TitouanMelon/ENIB_Robot_Mobile_Ros2/docs/latex/motor_command_8h_source.tex

\doxysection{motor\+Command.\+h}
\hypertarget{motor_command_8h_source}{}\label{motor_command_8h_source}\index{C:/Users/Administrator/Documents/GitHub/ENIB\_Robot\_Mobile\_Ros2/finalCode/WORKSPACE\_F411\_uROS/base\_robot/Core/Inc/motorCommand.h@{C:/Users/Administrator/Documents/GitHub/ENIB\_Robot\_Mobile\_Ros2/finalCode/WORKSPACE\_F411\_uROS/base\_robot/Core/Inc/motorCommand.h}}

\begin{DoxyCode}{0}
\DoxyCodeLine{\Hypertarget{motor_command_8h_source_l00001}00001\ \textcolor{comment}{/*}}
\DoxyCodeLine{\Hypertarget{motor_command_8h_source_l00002}00002\ \textcolor{comment}{\ *\ MotorCommand.h}}
\DoxyCodeLine{\Hypertarget{motor_command_8h_source_l00003}00003\ \textcolor{comment}{\ */}}
\DoxyCodeLine{\Hypertarget{motor_command_8h_source_l00004}00004\ }
\DoxyCodeLine{\Hypertarget{motor_command_8h_source_l00005}00005\ \textcolor{preprocessor}{\#ifndef\ INC\_MOTORCOMMAND\_H\_}}
\DoxyCodeLine{\Hypertarget{motor_command_8h_source_l00006}00006\ \textcolor{preprocessor}{\#define\ INC\_MOTORCOMMAND\_H\_}}
\DoxyCodeLine{\Hypertarget{motor_command_8h_source_l00007}00007\ }
\DoxyCodeLine{\Hypertarget{motor_command_8h_source_l00008}00008\ \textcolor{preprocessor}{\#include\ "{}\mbox{\hyperlink{main_8h}{main.h}}"{}}}
\DoxyCodeLine{\Hypertarget{motor_command_8h_source_l00009}00009\ }
\DoxyCodeLine{\Hypertarget{motor_command_8h_source_l00010}00010\ }
\DoxyCodeLine{\Hypertarget{motor_command_8h_source_l00011}00011\ \textcolor{keywordtype}{void}\ motorCommand\_Init(\textcolor{keywordtype}{void});}
\DoxyCodeLine{\Hypertarget{motor_command_8h_source_l00012}00012\ \textcolor{keywordtype}{void}\ motorLeft\_SetDuty(\textcolor{keywordtype}{int});}
\DoxyCodeLine{\Hypertarget{motor_command_8h_source_l00013}00013\ \textcolor{keywordtype}{void}\ motorRight\_SetDuty(\textcolor{keywordtype}{int});}
\DoxyCodeLine{\Hypertarget{motor_command_8h_source_l00014}00014\ }
\DoxyCodeLine{\Hypertarget{motor_command_8h_source_l00015}00015\ }
\DoxyCodeLine{\Hypertarget{motor_command_8h_source_l00016}00016\ }
\DoxyCodeLine{\Hypertarget{motor_command_8h_source_l00017}00017\ \textcolor{preprocessor}{\#endif\ }\textcolor{comment}{/*\ INC\_MOTORCOMMAND\_H\_\ */}\textcolor{preprocessor}{}}

\end{DoxyCode}
