TitouanMelon/ENIB_Robot_Mobile_Ros2/docs/latex/stm32f4xx__hal__conf_8h_source.tex

\doxysection{stm32f4xx\+\_\+hal\+\_\+conf.\+h}
\hypertarget{stm32f4xx__hal__conf_8h_source}{}\label{stm32f4xx__hal__conf_8h_source}\index{C:/Users/Administrator/Documents/GitHub/ENIB\_Robot\_Mobile\_Ros2/finalCode/WORKSPACE\_F411\_uROS/base\_robot/Core/Inc/stm32f4xx\_hal\_conf.h@{C:/Users/Administrator/Documents/GitHub/ENIB\_Robot\_Mobile\_Ros2/finalCode/WORKSPACE\_F411\_uROS/base\_robot/Core/Inc/stm32f4xx\_hal\_conf.h}}

\begin{DoxyCode}{0}
\DoxyCodeLine{\Hypertarget{stm32f4xx__hal__conf_8h_source_l00001}00001\ \textcolor{comment}{/*\ USER\ CODE\ BEGIN\ Header\ */}}
\DoxyCodeLine{\Hypertarget{stm32f4xx__hal__conf_8h_source_l00021}00021\ \textcolor{comment}{/*\ USER\ CODE\ END\ Header\ */}}
\DoxyCodeLine{\Hypertarget{stm32f4xx__hal__conf_8h_source_l00022}00022\ }
\DoxyCodeLine{\Hypertarget{stm32f4xx__hal__conf_8h_source_l00023}00023\ \textcolor{comment}{/*\ Define\ to\ prevent\ recursive\ inclusion\ -\/-\/-\/-\/-\/-\/-\/-\/-\/-\/-\/-\/-\/-\/-\/-\/-\/-\/-\/-\/-\/-\/-\/-\/-\/-\/-\/-\/-\/-\/-\/-\/-\/-\/-\/-\/-\/*/}}
\DoxyCodeLine{\Hypertarget{stm32f4xx__hal__conf_8h_source_l00024}00024\ \textcolor{preprocessor}{\#ifndef\ \_\_STM32F4xx\_HAL\_CONF\_H}}
\DoxyCodeLine{\Hypertarget{stm32f4xx__hal__conf_8h_source_l00025}00025\ \textcolor{preprocessor}{\#define\ \_\_STM32F4xx\_HAL\_CONF\_H}}
\DoxyCodeLine{\Hypertarget{stm32f4xx__hal__conf_8h_source_l00026}00026\ }
\DoxyCodeLine{\Hypertarget{stm32f4xx__hal__conf_8h_source_l00027}00027\ \textcolor{preprocessor}{\#ifdef\ \_\_cplusplus}}
\DoxyCodeLine{\Hypertarget{stm32f4xx__hal__conf_8h_source_l00028}00028\ \ \textcolor{keyword}{extern}\ \textcolor{stringliteral}{"{}C"{}}\ \{}
\DoxyCodeLine{\Hypertarget{stm32f4xx__hal__conf_8h_source_l00029}00029\ \textcolor{preprocessor}{\#endif}}
\DoxyCodeLine{\Hypertarget{stm32f4xx__hal__conf_8h_source_l00030}00030\ }
\DoxyCodeLine{\Hypertarget{stm32f4xx__hal__conf_8h_source_l00031}00031\ \textcolor{comment}{/*\ Exported\ types\ -\/-\/-\/-\/-\/-\/-\/-\/-\/-\/-\/-\/-\/-\/-\/-\/-\/-\/-\/-\/-\/-\/-\/-\/-\/-\/-\/-\/-\/-\/-\/-\/-\/-\/-\/-\/-\/-\/-\/-\/-\/-\/-\/-\/-\/-\/-\/-\/-\/-\/-\/-\/-\/-\/-\/-\/-\/-\/-\/-\/*/}}
\DoxyCodeLine{\Hypertarget{stm32f4xx__hal__conf_8h_source_l00032}00032\ \textcolor{comment}{/*\ Exported\ constants\ -\/-\/-\/-\/-\/-\/-\/-\/-\/-\/-\/-\/-\/-\/-\/-\/-\/-\/-\/-\/-\/-\/-\/-\/-\/-\/-\/-\/-\/-\/-\/-\/-\/-\/-\/-\/-\/-\/-\/-\/-\/-\/-\/-\/-\/-\/-\/-\/-\/-\/-\/-\/-\/-\/-\/-\/*/}}
\DoxyCodeLine{\Hypertarget{stm32f4xx__hal__conf_8h_source_l00033}00033\ }
\DoxyCodeLine{\Hypertarget{stm32f4xx__hal__conf_8h_source_l00034}00034\ \textcolor{comment}{/*\ \#\#\#\#\#\#\#\#\#\#\#\#\#\#\#\#\#\#\#\#\#\#\#\#\#\#\ Module\ Selection\ \#\#\#\#\#\#\#\#\#\#\#\#\#\#\#\#\#\#\#\#\#\#\#\#\#\#\#\#\#\#\ */}}
\DoxyCodeLine{\Hypertarget{stm32f4xx__hal__conf_8h_source_l00038}00038\ \textcolor{preprocessor}{\#define\ HAL\_MODULE\_ENABLED}}
\DoxyCodeLine{\Hypertarget{stm32f4xx__hal__conf_8h_source_l00039}00039\ }
\DoxyCodeLine{\Hypertarget{stm32f4xx__hal__conf_8h_source_l00040}00040\ \textcolor{preprocessor}{\ \#define\ HAL\_ADC\_MODULE\_ENABLED}}
\DoxyCodeLine{\Hypertarget{stm32f4xx__hal__conf_8h_source_l00041}00041\ \textcolor{comment}{/*\ \#define\ HAL\_CRYP\_MODULE\_ENABLED\ \ \ */}}
\DoxyCodeLine{\Hypertarget{stm32f4xx__hal__conf_8h_source_l00042}00042\ \textcolor{comment}{/*\ \#define\ HAL\_CAN\_MODULE\_ENABLED\ \ \ */}}
\DoxyCodeLine{\Hypertarget{stm32f4xx__hal__conf_8h_source_l00043}00043\ \textcolor{comment}{/*\ \#define\ HAL\_CRC\_MODULE\_ENABLED\ \ \ */}}
\DoxyCodeLine{\Hypertarget{stm32f4xx__hal__conf_8h_source_l00044}00044\ \textcolor{comment}{/*\ \#define\ HAL\_CAN\_LEGACY\_MODULE\_ENABLED\ \ \ */}}
\DoxyCodeLine{\Hypertarget{stm32f4xx__hal__conf_8h_source_l00045}00045\ \textcolor{comment}{/*\ \#define\ HAL\_CRYP\_MODULE\_ENABLED\ \ \ */}}
\DoxyCodeLine{\Hypertarget{stm32f4xx__hal__conf_8h_source_l00046}00046\ \textcolor{comment}{/*\ \#define\ HAL\_DAC\_MODULE\_ENABLED\ \ \ */}}
\DoxyCodeLine{\Hypertarget{stm32f4xx__hal__conf_8h_source_l00047}00047\ \textcolor{comment}{/*\ \#define\ HAL\_DCMI\_MODULE\_ENABLED\ \ \ */}}
\DoxyCodeLine{\Hypertarget{stm32f4xx__hal__conf_8h_source_l00048}00048\ \textcolor{comment}{/*\ \#define\ HAL\_DMA2D\_MODULE\_ENABLED\ \ \ */}}
\DoxyCodeLine{\Hypertarget{stm32f4xx__hal__conf_8h_source_l00049}00049\ \textcolor{comment}{/*\ \#define\ HAL\_ETH\_MODULE\_ENABLED\ \ \ */}}
\DoxyCodeLine{\Hypertarget{stm32f4xx__hal__conf_8h_source_l00050}00050\ \textcolor{comment}{/*\ \#define\ HAL\_NAND\_MODULE\_ENABLED\ \ \ */}}
\DoxyCodeLine{\Hypertarget{stm32f4xx__hal__conf_8h_source_l00051}00051\ \textcolor{comment}{/*\ \#define\ HAL\_NOR\_MODULE\_ENABLED\ \ \ */}}
\DoxyCodeLine{\Hypertarget{stm32f4xx__hal__conf_8h_source_l00052}00052\ \textcolor{comment}{/*\ \#define\ HAL\_PCCARD\_MODULE\_ENABLED\ \ \ */}}
\DoxyCodeLine{\Hypertarget{stm32f4xx__hal__conf_8h_source_l00053}00053\ \textcolor{comment}{/*\ \#define\ HAL\_SRAM\_MODULE\_ENABLED\ \ \ */}}
\DoxyCodeLine{\Hypertarget{stm32f4xx__hal__conf_8h_source_l00054}00054\ \textcolor{comment}{/*\ \#define\ HAL\_SDRAM\_MODULE\_ENABLED\ \ \ */}}
\DoxyCodeLine{\Hypertarget{stm32f4xx__hal__conf_8h_source_l00055}00055\ \textcolor{comment}{/*\ \#define\ HAL\_HASH\_MODULE\_ENABLED\ \ \ */}}
\DoxyCodeLine{\Hypertarget{stm32f4xx__hal__conf_8h_source_l00056}00056\ \textcolor{preprocessor}{\#define\ HAL\_I2C\_MODULE\_ENABLED}}
\DoxyCodeLine{\Hypertarget{stm32f4xx__hal__conf_8h_source_l00057}00057\ \textcolor{comment}{/*\ \#define\ HAL\_I2S\_MODULE\_ENABLED\ \ \ */}}
\DoxyCodeLine{\Hypertarget{stm32f4xx__hal__conf_8h_source_l00058}00058\ \textcolor{comment}{/*\ \#define\ HAL\_IWDG\_MODULE\_ENABLED\ \ \ */}}
\DoxyCodeLine{\Hypertarget{stm32f4xx__hal__conf_8h_source_l00059}00059\ \textcolor{comment}{/*\ \#define\ HAL\_LTDC\_MODULE\_ENABLED\ \ \ */}}
\DoxyCodeLine{\Hypertarget{stm32f4xx__hal__conf_8h_source_l00060}00060\ \textcolor{comment}{/*\ \#define\ HAL\_RNG\_MODULE\_ENABLED\ \ \ */}}
\DoxyCodeLine{\Hypertarget{stm32f4xx__hal__conf_8h_source_l00061}00061\ \textcolor{comment}{/*\ \#define\ HAL\_RTC\_MODULE\_ENABLED\ \ \ */}}
\DoxyCodeLine{\Hypertarget{stm32f4xx__hal__conf_8h_source_l00062}00062\ \textcolor{comment}{/*\ \#define\ HAL\_SAI\_MODULE\_ENABLED\ \ \ */}}
\DoxyCodeLine{\Hypertarget{stm32f4xx__hal__conf_8h_source_l00063}00063\ \textcolor{comment}{/*\ \#define\ HAL\_SD\_MODULE\_ENABLED\ \ \ */}}
\DoxyCodeLine{\Hypertarget{stm32f4xx__hal__conf_8h_source_l00064}00064\ \textcolor{comment}{/*\ \#define\ HAL\_MMC\_MODULE\_ENABLED\ \ \ */}}
\DoxyCodeLine{\Hypertarget{stm32f4xx__hal__conf_8h_source_l00065}00065\ \textcolor{comment}{/*\ \#define\ HAL\_SPI\_MODULE\_ENABLED\ \ \ */}}
\DoxyCodeLine{\Hypertarget{stm32f4xx__hal__conf_8h_source_l00066}00066\ \textcolor{preprocessor}{\#define\ HAL\_TIM\_MODULE\_ENABLED}}
\DoxyCodeLine{\Hypertarget{stm32f4xx__hal__conf_8h_source_l00067}00067\ \textcolor{preprocessor}{\#define\ HAL\_UART\_MODULE\_ENABLED}}
\DoxyCodeLine{\Hypertarget{stm32f4xx__hal__conf_8h_source_l00068}00068\ \textcolor{comment}{/*\ \#define\ HAL\_USART\_MODULE\_ENABLED\ \ \ */}}
\DoxyCodeLine{\Hypertarget{stm32f4xx__hal__conf_8h_source_l00069}00069\ \textcolor{comment}{/*\ \#define\ HAL\_IRDA\_MODULE\_ENABLED\ \ \ */}}
\DoxyCodeLine{\Hypertarget{stm32f4xx__hal__conf_8h_source_l00070}00070\ \textcolor{comment}{/*\ \#define\ HAL\_SMARTCARD\_MODULE\_ENABLED\ \ \ */}}
\DoxyCodeLine{\Hypertarget{stm32f4xx__hal__conf_8h_source_l00071}00071\ \textcolor{comment}{/*\ \#define\ HAL\_SMBUS\_MODULE\_ENABLED\ \ \ */}}
\DoxyCodeLine{\Hypertarget{stm32f4xx__hal__conf_8h_source_l00072}00072\ \textcolor{comment}{/*\ \#define\ HAL\_WWDG\_MODULE\_ENABLED\ \ \ */}}
\DoxyCodeLine{\Hypertarget{stm32f4xx__hal__conf_8h_source_l00073}00073\ \textcolor{comment}{/*\ \#define\ HAL\_PCD\_MODULE\_ENABLED\ \ \ */}}
\DoxyCodeLine{\Hypertarget{stm32f4xx__hal__conf_8h_source_l00074}00074\ \textcolor{comment}{/*\ \#define\ HAL\_HCD\_MODULE\_ENABLED\ \ \ */}}
\DoxyCodeLine{\Hypertarget{stm32f4xx__hal__conf_8h_source_l00075}00075\ \textcolor{comment}{/*\ \#define\ HAL\_DSI\_MODULE\_ENABLED\ \ \ */}}
\DoxyCodeLine{\Hypertarget{stm32f4xx__hal__conf_8h_source_l00076}00076\ \textcolor{comment}{/*\ \#define\ HAL\_QSPI\_MODULE\_ENABLED\ \ \ */}}
\DoxyCodeLine{\Hypertarget{stm32f4xx__hal__conf_8h_source_l00077}00077\ \textcolor{comment}{/*\ \#define\ HAL\_QSPI\_MODULE\_ENABLED\ \ \ */}}
\DoxyCodeLine{\Hypertarget{stm32f4xx__hal__conf_8h_source_l00078}00078\ \textcolor{comment}{/*\ \#define\ HAL\_CEC\_MODULE\_ENABLED\ \ \ */}}
\DoxyCodeLine{\Hypertarget{stm32f4xx__hal__conf_8h_source_l00079}00079\ \textcolor{comment}{/*\ \#define\ HAL\_FMPI2C\_MODULE\_ENABLED\ \ \ */}}
\DoxyCodeLine{\Hypertarget{stm32f4xx__hal__conf_8h_source_l00080}00080\ \textcolor{comment}{/*\ \#define\ HAL\_FMPSMBUS\_MODULE\_ENABLED\ \ \ */}}
\DoxyCodeLine{\Hypertarget{stm32f4xx__hal__conf_8h_source_l00081}00081\ \textcolor{comment}{/*\ \#define\ HAL\_SPDIFRX\_MODULE\_ENABLED\ \ \ */}}
\DoxyCodeLine{\Hypertarget{stm32f4xx__hal__conf_8h_source_l00082}00082\ \textcolor{comment}{/*\ \#define\ HAL\_DFSDM\_MODULE\_ENABLED\ \ \ */}}
\DoxyCodeLine{\Hypertarget{stm32f4xx__hal__conf_8h_source_l00083}00083\ \textcolor{comment}{/*\ \#define\ HAL\_LPTIM\_MODULE\_ENABLED\ \ \ */}}
\DoxyCodeLine{\Hypertarget{stm32f4xx__hal__conf_8h_source_l00084}00084\ \textcolor{preprocessor}{\#define\ HAL\_GPIO\_MODULE\_ENABLED}}
\DoxyCodeLine{\Hypertarget{stm32f4xx__hal__conf_8h_source_l00085}00085\ \textcolor{preprocessor}{\#define\ HAL\_EXTI\_MODULE\_ENABLED}}
\DoxyCodeLine{\Hypertarget{stm32f4xx__hal__conf_8h_source_l00086}00086\ \textcolor{preprocessor}{\#define\ HAL\_DMA\_MODULE\_ENABLED}}
\DoxyCodeLine{\Hypertarget{stm32f4xx__hal__conf_8h_source_l00087}00087\ \textcolor{preprocessor}{\#define\ HAL\_RCC\_MODULE\_ENABLED}}
\DoxyCodeLine{\Hypertarget{stm32f4xx__hal__conf_8h_source_l00088}00088\ \textcolor{preprocessor}{\#define\ HAL\_FLASH\_MODULE\_ENABLED}}
\DoxyCodeLine{\Hypertarget{stm32f4xx__hal__conf_8h_source_l00089}00089\ \textcolor{preprocessor}{\#define\ HAL\_PWR\_MODULE\_ENABLED}}
\DoxyCodeLine{\Hypertarget{stm32f4xx__hal__conf_8h_source_l00090}00090\ \textcolor{preprocessor}{\#define\ HAL\_CORTEX\_MODULE\_ENABLED}}
\DoxyCodeLine{\Hypertarget{stm32f4xx__hal__conf_8h_source_l00091}00091\ }
\DoxyCodeLine{\Hypertarget{stm32f4xx__hal__conf_8h_source_l00092}00092\ \textcolor{comment}{/*\ \#\#\#\#\#\#\#\#\#\#\#\#\#\#\#\#\#\#\#\#\#\#\#\#\#\#\ HSE/HSI\ Values\ adaptation\ \#\#\#\#\#\#\#\#\#\#\#\#\#\#\#\#\#\#\#\#\#\ */}}
\DoxyCodeLine{\Hypertarget{stm32f4xx__hal__conf_8h_source_l00098}00098\ \textcolor{preprocessor}{\#if\ !defined\ \ (HSE\_VALUE)}}
\DoxyCodeLine{\Hypertarget{stm32f4xx__hal__conf_8h_source_l00099}00099\ \textcolor{preprocessor}{\ \ \#define\ HSE\_VALUE\ \ \ \ 8000000U\ }}
\DoxyCodeLine{\Hypertarget{stm32f4xx__hal__conf_8h_source_l00100}00100\ \textcolor{preprocessor}{\#endif\ }\textcolor{comment}{/*\ HSE\_VALUE\ */}\textcolor{preprocessor}{}}
\DoxyCodeLine{\Hypertarget{stm32f4xx__hal__conf_8h_source_l00101}00101\ }
\DoxyCodeLine{\Hypertarget{stm32f4xx__hal__conf_8h_source_l00102}00102\ \textcolor{preprocessor}{\#if\ !defined\ \ (HSE\_STARTUP\_TIMEOUT)}}
\DoxyCodeLine{\Hypertarget{stm32f4xx__hal__conf_8h_source_l00103}00103\ \textcolor{preprocessor}{\ \ \#define\ HSE\_STARTUP\_TIMEOUT\ \ \ \ 100U\ \ \ }}
\DoxyCodeLine{\Hypertarget{stm32f4xx__hal__conf_8h_source_l00104}00104\ \textcolor{preprocessor}{\#endif\ }\textcolor{comment}{/*\ HSE\_STARTUP\_TIMEOUT\ */}\textcolor{preprocessor}{}}
\DoxyCodeLine{\Hypertarget{stm32f4xx__hal__conf_8h_source_l00105}00105\ }
\DoxyCodeLine{\Hypertarget{stm32f4xx__hal__conf_8h_source_l00111}00111\ \textcolor{preprocessor}{\#if\ !defined\ \ (HSI\_VALUE)}}
\DoxyCodeLine{\Hypertarget{stm32f4xx__hal__conf_8h_source_l00112}00112\ \textcolor{preprocessor}{\ \ \#define\ HSI\_VALUE\ \ \ \ ((uint32\_t)16000000U)\ }}
\DoxyCodeLine{\Hypertarget{stm32f4xx__hal__conf_8h_source_l00113}00113\ \textcolor{preprocessor}{\#endif\ }\textcolor{comment}{/*\ HSI\_VALUE\ */}\textcolor{preprocessor}{}}
\DoxyCodeLine{\Hypertarget{stm32f4xx__hal__conf_8h_source_l00114}00114\ }
\DoxyCodeLine{\Hypertarget{stm32f4xx__hal__conf_8h_source_l00118}00118\ \textcolor{preprocessor}{\#if\ !defined\ \ (LSI\_VALUE)}}
\DoxyCodeLine{\Hypertarget{stm32f4xx__hal__conf_8h_source_l00119}00119\ \textcolor{preprocessor}{\ \#define\ LSI\_VALUE\ \ 32000U\ \ \ \ \ \ \ }}
\DoxyCodeLine{\Hypertarget{stm32f4xx__hal__conf_8h_source_l00120}00120\ \textcolor{preprocessor}{\#endif\ }\textcolor{comment}{/*\ LSI\_VALUE\ */}\textcolor{preprocessor}{\ \ \ \ \ \ \ \ \ \ \ \ \ \ \ \ \ \ \ \ \ \ }}
\DoxyCodeLine{\Hypertarget{stm32f4xx__hal__conf_8h_source_l00126}00126\ \textcolor{preprocessor}{\#if\ !defined\ \ (LSE\_VALUE)}}
\DoxyCodeLine{\Hypertarget{stm32f4xx__hal__conf_8h_source_l00127}00127\ \textcolor{preprocessor}{\ \#define\ LSE\_VALUE\ \ 32768U\ \ \ \ }}
\DoxyCodeLine{\Hypertarget{stm32f4xx__hal__conf_8h_source_l00128}00128\ \textcolor{preprocessor}{\#endif\ }\textcolor{comment}{/*\ LSE\_VALUE\ */}\textcolor{preprocessor}{}}
\DoxyCodeLine{\Hypertarget{stm32f4xx__hal__conf_8h_source_l00129}00129\ }
\DoxyCodeLine{\Hypertarget{stm32f4xx__hal__conf_8h_source_l00130}00130\ \textcolor{preprocessor}{\#if\ !defined\ \ (LSE\_STARTUP\_TIMEOUT)}}
\DoxyCodeLine{\Hypertarget{stm32f4xx__hal__conf_8h_source_l00131}00131\ \textcolor{preprocessor}{\ \ \#define\ LSE\_STARTUP\_TIMEOUT\ \ \ \ 5000U\ \ \ }}
\DoxyCodeLine{\Hypertarget{stm32f4xx__hal__conf_8h_source_l00132}00132\ \textcolor{preprocessor}{\#endif\ }\textcolor{comment}{/*\ LSE\_STARTUP\_TIMEOUT\ */}\textcolor{preprocessor}{}}
\DoxyCodeLine{\Hypertarget{stm32f4xx__hal__conf_8h_source_l00133}00133\ }
\DoxyCodeLine{\Hypertarget{stm32f4xx__hal__conf_8h_source_l00139}00139\ \textcolor{preprocessor}{\#if\ !defined\ \ (EXTERNAL\_CLOCK\_VALUE)}}
\DoxyCodeLine{\Hypertarget{stm32f4xx__hal__conf_8h_source_l00140}00140\ \textcolor{preprocessor}{\ \ \#define\ EXTERNAL\_CLOCK\_VALUE\ \ \ \ 12288000U\ }}
\DoxyCodeLine{\Hypertarget{stm32f4xx__hal__conf_8h_source_l00141}00141\ \textcolor{preprocessor}{\#endif\ }\textcolor{comment}{/*\ EXTERNAL\_CLOCK\_VALUE\ */}\textcolor{preprocessor}{}}
\DoxyCodeLine{\Hypertarget{stm32f4xx__hal__conf_8h_source_l00142}00142\ }
\DoxyCodeLine{\Hypertarget{stm32f4xx__hal__conf_8h_source_l00143}00143\ \textcolor{comment}{/*\ Tip:\ To\ avoid\ modifying\ this\ file\ each\ time\ you\ need\ to\ use\ different\ HSE,}}
\DoxyCodeLine{\Hypertarget{stm32f4xx__hal__conf_8h_source_l00144}00144\ \textcolor{comment}{\ \ \ ===\ \ you\ can\ define\ the\ HSE\ value\ in\ your\ toolchain\ compiler\ preprocessor.\ */}}
\DoxyCodeLine{\Hypertarget{stm32f4xx__hal__conf_8h_source_l00145}00145\ }
\DoxyCodeLine{\Hypertarget{stm32f4xx__hal__conf_8h_source_l00146}00146\ \textcolor{comment}{/*\ \#\#\#\#\#\#\#\#\#\#\#\#\#\#\#\#\#\#\#\#\#\#\#\#\#\#\#\ System\ Configuration\ \#\#\#\#\#\#\#\#\#\#\#\#\#\#\#\#\#\#\#\#\#\#\#\#\#\ */}}
\DoxyCodeLine{\Hypertarget{stm32f4xx__hal__conf_8h_source_l00150}00150\ \textcolor{preprocessor}{\#define\ \ VDD\_VALUE\ \ \ \ \ \ \ \ \ \ \ \ 3300U\ }}
\DoxyCodeLine{\Hypertarget{stm32f4xx__hal__conf_8h_source_l00151}00151\ \textcolor{preprocessor}{\#define\ \ TICK\_INT\_PRIORITY\ \ \ \ \ \ \ \ \ \ \ \ 15U\ \ \ }}
\DoxyCodeLine{\Hypertarget{stm32f4xx__hal__conf_8h_source_l00152}00152\ \textcolor{preprocessor}{\#define\ \ USE\_RTOS\ \ \ \ \ \ \ \ \ \ \ \ \ \ \ \ \ \ \ \ \ 0U}}
\DoxyCodeLine{\Hypertarget{stm32f4xx__hal__conf_8h_source_l00153}00153\ \textcolor{preprocessor}{\#define\ \ PREFETCH\_ENABLE\ \ \ \ \ \ \ \ \ \ \ \ \ \ 1U}}
\DoxyCodeLine{\Hypertarget{stm32f4xx__hal__conf_8h_source_l00154}00154\ \textcolor{preprocessor}{\#define\ \ INSTRUCTION\_CACHE\_ENABLE\ \ \ \ \ 1U}}
\DoxyCodeLine{\Hypertarget{stm32f4xx__hal__conf_8h_source_l00155}00155\ \textcolor{preprocessor}{\#define\ \ DATA\_CACHE\_ENABLE\ \ \ \ \ \ \ \ \ \ \ \ 1U}}
\DoxyCodeLine{\Hypertarget{stm32f4xx__hal__conf_8h_source_l00156}00156\ }
\DoxyCodeLine{\Hypertarget{stm32f4xx__hal__conf_8h_source_l00157}00157\ \textcolor{preprocessor}{\#define\ \ USE\_HAL\_ADC\_REGISTER\_CALLBACKS\ \ \ \ \ \ \ \ \ 0U\ }\textcolor{comment}{/*\ ADC\ register\ callback\ disabled\ \ \ \ \ \ \ */}\textcolor{preprocessor}{}}
\DoxyCodeLine{\Hypertarget{stm32f4xx__hal__conf_8h_source_l00158}00158\ \textcolor{preprocessor}{\#define\ \ USE\_HAL\_CAN\_REGISTER\_CALLBACKS\ \ \ \ \ \ \ \ \ 0U\ }\textcolor{comment}{/*\ CAN\ register\ callback\ disabled\ \ \ \ \ \ \ */}\textcolor{preprocessor}{}}
\DoxyCodeLine{\Hypertarget{stm32f4xx__hal__conf_8h_source_l00159}00159\ \textcolor{preprocessor}{\#define\ \ USE\_HAL\_CEC\_REGISTER\_CALLBACKS\ \ \ \ \ \ \ \ \ 0U\ }\textcolor{comment}{/*\ CEC\ register\ callback\ disabled\ \ \ \ \ \ \ */}\textcolor{preprocessor}{}}
\DoxyCodeLine{\Hypertarget{stm32f4xx__hal__conf_8h_source_l00160}00160\ \textcolor{preprocessor}{\#define\ \ USE\_HAL\_CRYP\_REGISTER\_CALLBACKS\ \ \ \ \ \ \ \ 0U\ }\textcolor{comment}{/*\ CRYP\ register\ callback\ disabled\ \ \ \ \ \ */}\textcolor{preprocessor}{}}
\DoxyCodeLine{\Hypertarget{stm32f4xx__hal__conf_8h_source_l00161}00161\ \textcolor{preprocessor}{\#define\ \ USE\_HAL\_DAC\_REGISTER\_CALLBACKS\ \ \ \ \ \ \ \ \ 0U\ }\textcolor{comment}{/*\ DAC\ register\ callback\ disabled\ \ \ \ \ \ \ */}\textcolor{preprocessor}{}}
\DoxyCodeLine{\Hypertarget{stm32f4xx__hal__conf_8h_source_l00162}00162\ \textcolor{preprocessor}{\#define\ \ USE\_HAL\_DCMI\_REGISTER\_CALLBACKS\ \ \ \ \ \ \ \ 0U\ }\textcolor{comment}{/*\ DCMI\ register\ callback\ disabled\ \ \ \ \ \ */}\textcolor{preprocessor}{}}
\DoxyCodeLine{\Hypertarget{stm32f4xx__hal__conf_8h_source_l00163}00163\ \textcolor{preprocessor}{\#define\ \ USE\_HAL\_DFSDM\_REGISTER\_CALLBACKS\ \ \ \ \ \ \ 0U\ }\textcolor{comment}{/*\ DFSDM\ register\ callback\ disabled\ \ \ \ \ */}\textcolor{preprocessor}{}}
\DoxyCodeLine{\Hypertarget{stm32f4xx__hal__conf_8h_source_l00164}00164\ \textcolor{preprocessor}{\#define\ \ USE\_HAL\_DMA2D\_REGISTER\_CALLBACKS\ \ \ \ \ \ \ 0U\ }\textcolor{comment}{/*\ DMA2D\ register\ callback\ disabled\ \ \ \ \ */}\textcolor{preprocessor}{}}
\DoxyCodeLine{\Hypertarget{stm32f4xx__hal__conf_8h_source_l00165}00165\ \textcolor{preprocessor}{\#define\ \ USE\_HAL\_DSI\_REGISTER\_CALLBACKS\ \ \ \ \ \ \ \ \ 0U\ }\textcolor{comment}{/*\ DSI\ register\ callback\ disabled\ \ \ \ \ \ \ */}\textcolor{preprocessor}{}}
\DoxyCodeLine{\Hypertarget{stm32f4xx__hal__conf_8h_source_l00166}00166\ \textcolor{preprocessor}{\#define\ \ USE\_HAL\_ETH\_REGISTER\_CALLBACKS\ \ \ \ \ \ \ \ \ 0U\ }\textcolor{comment}{/*\ ETH\ register\ callback\ disabled\ \ \ \ \ \ \ */}\textcolor{preprocessor}{}}
\DoxyCodeLine{\Hypertarget{stm32f4xx__hal__conf_8h_source_l00167}00167\ \textcolor{preprocessor}{\#define\ \ USE\_HAL\_HASH\_REGISTER\_CALLBACKS\ \ \ \ \ \ \ \ 0U\ }\textcolor{comment}{/*\ HASH\ register\ callback\ disabled\ \ \ \ \ \ */}\textcolor{preprocessor}{}}
\DoxyCodeLine{\Hypertarget{stm32f4xx__hal__conf_8h_source_l00168}00168\ \textcolor{preprocessor}{\#define\ \ USE\_HAL\_HCD\_REGISTER\_CALLBACKS\ \ \ \ \ \ \ \ \ 0U\ }\textcolor{comment}{/*\ HCD\ register\ callback\ disabled\ \ \ \ \ \ \ */}\textcolor{preprocessor}{}}
\DoxyCodeLine{\Hypertarget{stm32f4xx__hal__conf_8h_source_l00169}00169\ \textcolor{preprocessor}{\#define\ \ USE\_HAL\_I2C\_REGISTER\_CALLBACKS\ \ \ \ \ \ \ \ \ 0U\ }\textcolor{comment}{/*\ I2C\ register\ callback\ disabled\ \ \ \ \ \ \ */}\textcolor{preprocessor}{}}
\DoxyCodeLine{\Hypertarget{stm32f4xx__hal__conf_8h_source_l00170}00170\ \textcolor{preprocessor}{\#define\ \ USE\_HAL\_FMPI2C\_REGISTER\_CALLBACKS\ \ \ \ \ \ 0U\ }\textcolor{comment}{/*\ FMPI2C\ register\ callback\ disabled\ \ \ \ */}\textcolor{preprocessor}{}}
\DoxyCodeLine{\Hypertarget{stm32f4xx__hal__conf_8h_source_l00171}00171\ \textcolor{preprocessor}{\#define\ \ USE\_HAL\_FMPSMBUS\_REGISTER\_CALLBACKS\ \ \ \ 0U\ }\textcolor{comment}{/*\ FMPSMBUS\ register\ callback\ disabled\ \ */}\textcolor{preprocessor}{}}
\DoxyCodeLine{\Hypertarget{stm32f4xx__hal__conf_8h_source_l00172}00172\ \textcolor{preprocessor}{\#define\ \ USE\_HAL\_I2S\_REGISTER\_CALLBACKS\ \ \ \ \ \ \ \ \ 0U\ }\textcolor{comment}{/*\ I2S\ register\ callback\ disabled\ \ \ \ \ \ \ */}\textcolor{preprocessor}{}}
\DoxyCodeLine{\Hypertarget{stm32f4xx__hal__conf_8h_source_l00173}00173\ \textcolor{preprocessor}{\#define\ \ USE\_HAL\_IRDA\_REGISTER\_CALLBACKS\ \ \ \ \ \ \ \ 0U\ }\textcolor{comment}{/*\ IRDA\ register\ callback\ disabled\ \ \ \ \ \ */}\textcolor{preprocessor}{}}
\DoxyCodeLine{\Hypertarget{stm32f4xx__hal__conf_8h_source_l00174}00174\ \textcolor{preprocessor}{\#define\ \ USE\_HAL\_LPTIM\_REGISTER\_CALLBACKS\ \ \ \ \ \ \ 0U\ }\textcolor{comment}{/*\ LPTIM\ register\ callback\ disabled\ \ \ \ \ */}\textcolor{preprocessor}{}}
\DoxyCodeLine{\Hypertarget{stm32f4xx__hal__conf_8h_source_l00175}00175\ \textcolor{preprocessor}{\#define\ \ USE\_HAL\_LTDC\_REGISTER\_CALLBACKS\ \ \ \ \ \ \ \ 0U\ }\textcolor{comment}{/*\ LTDC\ register\ callback\ disabled\ \ \ \ \ \ */}\textcolor{preprocessor}{}}
\DoxyCodeLine{\Hypertarget{stm32f4xx__hal__conf_8h_source_l00176}00176\ \textcolor{preprocessor}{\#define\ \ USE\_HAL\_MMC\_REGISTER\_CALLBACKS\ \ \ \ \ \ \ \ \ 0U\ }\textcolor{comment}{/*\ MMC\ register\ callback\ disabled\ \ \ \ \ \ \ */}\textcolor{preprocessor}{}}
\DoxyCodeLine{\Hypertarget{stm32f4xx__hal__conf_8h_source_l00177}00177\ \textcolor{preprocessor}{\#define\ \ USE\_HAL\_NAND\_REGISTER\_CALLBACKS\ \ \ \ \ \ \ \ 0U\ }\textcolor{comment}{/*\ NAND\ register\ callback\ disabled\ \ \ \ \ \ */}\textcolor{preprocessor}{}}
\DoxyCodeLine{\Hypertarget{stm32f4xx__hal__conf_8h_source_l00178}00178\ \textcolor{preprocessor}{\#define\ \ USE\_HAL\_NOR\_REGISTER\_CALLBACKS\ \ \ \ \ \ \ \ \ 0U\ }\textcolor{comment}{/*\ NOR\ register\ callback\ disabled\ \ \ \ \ \ \ */}\textcolor{preprocessor}{}}
\DoxyCodeLine{\Hypertarget{stm32f4xx__hal__conf_8h_source_l00179}00179\ \textcolor{preprocessor}{\#define\ \ USE\_HAL\_PCCARD\_REGISTER\_CALLBACKS\ \ \ \ \ \ 0U\ }\textcolor{comment}{/*\ PCCARD\ register\ callback\ disabled\ \ \ \ */}\textcolor{preprocessor}{}}
\DoxyCodeLine{\Hypertarget{stm32f4xx__hal__conf_8h_source_l00180}00180\ \textcolor{preprocessor}{\#define\ \ USE\_HAL\_PCD\_REGISTER\_CALLBACKS\ \ \ \ \ \ \ \ \ 0U\ }\textcolor{comment}{/*\ PCD\ register\ callback\ disabled\ \ \ \ \ \ \ */}\textcolor{preprocessor}{}}
\DoxyCodeLine{\Hypertarget{stm32f4xx__hal__conf_8h_source_l00181}00181\ \textcolor{preprocessor}{\#define\ \ USE\_HAL\_QSPI\_REGISTER\_CALLBACKS\ \ \ \ \ \ \ \ 0U\ }\textcolor{comment}{/*\ QSPI\ register\ callback\ disabled\ \ \ \ \ \ */}\textcolor{preprocessor}{}}
\DoxyCodeLine{\Hypertarget{stm32f4xx__hal__conf_8h_source_l00182}00182\ \textcolor{preprocessor}{\#define\ \ USE\_HAL\_RNG\_REGISTER\_CALLBACKS\ \ \ \ \ \ \ \ \ 0U\ }\textcolor{comment}{/*\ RNG\ register\ callback\ disabled\ \ \ \ \ \ \ */}\textcolor{preprocessor}{}}
\DoxyCodeLine{\Hypertarget{stm32f4xx__hal__conf_8h_source_l00183}00183\ \textcolor{preprocessor}{\#define\ \ USE\_HAL\_RTC\_REGISTER\_CALLBACKS\ \ \ \ \ \ \ \ \ 0U\ }\textcolor{comment}{/*\ RTC\ register\ callback\ disabled\ \ \ \ \ \ \ */}\textcolor{preprocessor}{}}
\DoxyCodeLine{\Hypertarget{stm32f4xx__hal__conf_8h_source_l00184}00184\ \textcolor{preprocessor}{\#define\ \ USE\_HAL\_SAI\_REGISTER\_CALLBACKS\ \ \ \ \ \ \ \ \ 0U\ }\textcolor{comment}{/*\ SAI\ register\ callback\ disabled\ \ \ \ \ \ \ */}\textcolor{preprocessor}{}}
\DoxyCodeLine{\Hypertarget{stm32f4xx__hal__conf_8h_source_l00185}00185\ \textcolor{preprocessor}{\#define\ \ USE\_HAL\_SD\_REGISTER\_CALLBACKS\ \ \ \ \ \ \ \ \ \ 0U\ }\textcolor{comment}{/*\ SD\ register\ callback\ disabled\ \ \ \ \ \ \ \ */}\textcolor{preprocessor}{}}
\DoxyCodeLine{\Hypertarget{stm32f4xx__hal__conf_8h_source_l00186}00186\ \textcolor{preprocessor}{\#define\ \ USE\_HAL\_SMARTCARD\_REGISTER\_CALLBACKS\ \ \ 0U\ }\textcolor{comment}{/*\ SMARTCARD\ register\ callback\ disabled\ */}\textcolor{preprocessor}{}}
\DoxyCodeLine{\Hypertarget{stm32f4xx__hal__conf_8h_source_l00187}00187\ \textcolor{preprocessor}{\#define\ \ USE\_HAL\_SDRAM\_REGISTER\_CALLBACKS\ \ \ \ \ \ \ 0U\ }\textcolor{comment}{/*\ SDRAM\ register\ callback\ disabled\ \ \ \ \ */}\textcolor{preprocessor}{}}
\DoxyCodeLine{\Hypertarget{stm32f4xx__hal__conf_8h_source_l00188}00188\ \textcolor{preprocessor}{\#define\ \ USE\_HAL\_SRAM\_REGISTER\_CALLBACKS\ \ \ \ \ \ \ \ 0U\ }\textcolor{comment}{/*\ SRAM\ register\ callback\ disabled\ \ \ \ \ \ */}\textcolor{preprocessor}{}}
\DoxyCodeLine{\Hypertarget{stm32f4xx__hal__conf_8h_source_l00189}00189\ \textcolor{preprocessor}{\#define\ \ USE\_HAL\_SPDIFRX\_REGISTER\_CALLBACKS\ \ \ \ \ 0U\ }\textcolor{comment}{/*\ SPDIFRX\ register\ callback\ disabled\ \ \ */}\textcolor{preprocessor}{}}
\DoxyCodeLine{\Hypertarget{stm32f4xx__hal__conf_8h_source_l00190}00190\ \textcolor{preprocessor}{\#define\ \ USE\_HAL\_SMBUS\_REGISTER\_CALLBACKS\ \ \ \ \ \ \ 0U\ }\textcolor{comment}{/*\ SMBUS\ register\ callback\ disabled\ \ \ \ \ */}\textcolor{preprocessor}{}}
\DoxyCodeLine{\Hypertarget{stm32f4xx__hal__conf_8h_source_l00191}00191\ \textcolor{preprocessor}{\#define\ \ USE\_HAL\_SPI\_REGISTER\_CALLBACKS\ \ \ \ \ \ \ \ \ 0U\ }\textcolor{comment}{/*\ SPI\ register\ callback\ disabled\ \ \ \ \ \ \ */}\textcolor{preprocessor}{}}
\DoxyCodeLine{\Hypertarget{stm32f4xx__hal__conf_8h_source_l00192}00192\ \textcolor{preprocessor}{\#define\ \ USE\_HAL\_TIM\_REGISTER\_CALLBACKS\ \ \ \ \ \ \ \ \ 0U\ }\textcolor{comment}{/*\ TIM\ register\ callback\ disabled\ \ \ \ \ \ \ */}\textcolor{preprocessor}{}}
\DoxyCodeLine{\Hypertarget{stm32f4xx__hal__conf_8h_source_l00193}00193\ \textcolor{preprocessor}{\#define\ \ USE\_HAL\_UART\_REGISTER\_CALLBACKS\ \ \ \ \ \ \ \ 0U\ }\textcolor{comment}{/*\ UART\ register\ callback\ disabled\ \ \ \ \ \ */}\textcolor{preprocessor}{}}
\DoxyCodeLine{\Hypertarget{stm32f4xx__hal__conf_8h_source_l00194}00194\ \textcolor{preprocessor}{\#define\ \ USE\_HAL\_USART\_REGISTER\_CALLBACKS\ \ \ \ \ \ \ 0U\ }\textcolor{comment}{/*\ USART\ register\ callback\ disabled\ \ \ \ \ */}\textcolor{preprocessor}{}}
\DoxyCodeLine{\Hypertarget{stm32f4xx__hal__conf_8h_source_l00195}00195\ \textcolor{preprocessor}{\#define\ \ USE\_HAL\_WWDG\_REGISTER\_CALLBACKS\ \ \ \ \ \ \ \ 0U\ }\textcolor{comment}{/*\ WWDG\ register\ callback\ disabled\ \ \ \ \ \ */}\textcolor{preprocessor}{}}
\DoxyCodeLine{\Hypertarget{stm32f4xx__hal__conf_8h_source_l00196}00196\ }
\DoxyCodeLine{\Hypertarget{stm32f4xx__hal__conf_8h_source_l00197}00197\ \textcolor{comment}{/*\ \#\#\#\#\#\#\#\#\#\#\#\#\#\#\#\#\#\#\#\#\#\#\#\#\#\#\ Assert\ Selection\ \#\#\#\#\#\#\#\#\#\#\#\#\#\#\#\#\#\#\#\#\#\#\#\#\#\#\#\#\#\#\ */}}
\DoxyCodeLine{\Hypertarget{stm32f4xx__hal__conf_8h_source_l00202}00202\ \textcolor{comment}{/*\ \#define\ USE\_FULL\_ASSERT\ \ \ \ 1U\ */}}
\DoxyCodeLine{\Hypertarget{stm32f4xx__hal__conf_8h_source_l00203}00203\ }
\DoxyCodeLine{\Hypertarget{stm32f4xx__hal__conf_8h_source_l00204}00204\ \textcolor{comment}{/*\ \#\#\#\#\#\#\#\#\#\#\#\#\#\#\#\#\#\#\ Ethernet\ peripheral\ configuration\ \#\#\#\#\#\#\#\#\#\#\#\#\#\#\#\#\#\#\#\#\#\ */}}
\DoxyCodeLine{\Hypertarget{stm32f4xx__hal__conf_8h_source_l00205}00205\ }
\DoxyCodeLine{\Hypertarget{stm32f4xx__hal__conf_8h_source_l00206}00206\ \textcolor{comment}{/*\ Section\ 1\ :\ Ethernet\ peripheral\ configuration\ */}}
\DoxyCodeLine{\Hypertarget{stm32f4xx__hal__conf_8h_source_l00207}00207\ }
\DoxyCodeLine{\Hypertarget{stm32f4xx__hal__conf_8h_source_l00208}00208\ \textcolor{comment}{/*\ MAC\ ADDRESS:\ MAC\_ADDR0:MAC\_ADDR1:MAC\_ADDR2:MAC\_ADDR3:MAC\_ADDR4:MAC\_ADDR5\ */}}
\DoxyCodeLine{\Hypertarget{stm32f4xx__hal__conf_8h_source_l00209}00209\ \textcolor{preprocessor}{\#define\ MAC\_ADDR0\ \ \ 2U}}
\DoxyCodeLine{\Hypertarget{stm32f4xx__hal__conf_8h_source_l00210}00210\ \textcolor{preprocessor}{\#define\ MAC\_ADDR1\ \ \ 0U}}
\DoxyCodeLine{\Hypertarget{stm32f4xx__hal__conf_8h_source_l00211}00211\ \textcolor{preprocessor}{\#define\ MAC\_ADDR2\ \ \ 0U}}
\DoxyCodeLine{\Hypertarget{stm32f4xx__hal__conf_8h_source_l00212}00212\ \textcolor{preprocessor}{\#define\ MAC\_ADDR3\ \ \ 0U}}
\DoxyCodeLine{\Hypertarget{stm32f4xx__hal__conf_8h_source_l00213}00213\ \textcolor{preprocessor}{\#define\ MAC\_ADDR4\ \ \ 0U}}
\DoxyCodeLine{\Hypertarget{stm32f4xx__hal__conf_8h_source_l00214}00214\ \textcolor{preprocessor}{\#define\ MAC\_ADDR5\ \ \ 0U}}
\DoxyCodeLine{\Hypertarget{stm32f4xx__hal__conf_8h_source_l00215}00215\ }
\DoxyCodeLine{\Hypertarget{stm32f4xx__hal__conf_8h_source_l00216}00216\ \textcolor{comment}{/*\ Definition\ of\ the\ Ethernet\ driver\ buffers\ size\ and\ count\ */}}
\DoxyCodeLine{\Hypertarget{stm32f4xx__hal__conf_8h_source_l00217}00217\ \textcolor{preprocessor}{\#define\ ETH\_RX\_BUF\_SIZE\ \ \ \ \ \ \ \ \ \ \ \ \ \ \ \ ETH\_MAX\_PACKET\_SIZE\ }\textcolor{comment}{/*\ buffer\ size\ for\ receive\ \ \ \ \ \ \ \ \ \ \ \ \ \ \ */}\textcolor{preprocessor}{}}
\DoxyCodeLine{\Hypertarget{stm32f4xx__hal__conf_8h_source_l00218}00218\ \textcolor{preprocessor}{\#define\ ETH\_TX\_BUF\_SIZE\ \ \ \ \ \ \ \ \ \ \ \ \ \ \ \ ETH\_MAX\_PACKET\_SIZE\ }\textcolor{comment}{/*\ buffer\ size\ for\ transmit\ \ \ \ \ \ \ \ \ \ \ \ \ \ */}\textcolor{preprocessor}{}}
\DoxyCodeLine{\Hypertarget{stm32f4xx__hal__conf_8h_source_l00219}00219\ \textcolor{preprocessor}{\#define\ ETH\_RXBUFNB\ \ \ \ \ \ \ \ \ \ \ \ \ \ \ \ \ \ \ \ 4U\ \ \ \ \ \ \ }\textcolor{comment}{/*\ 4\ Rx\ buffers\ of\ size\ ETH\_RX\_BUF\_SIZE\ \ */}\textcolor{preprocessor}{}}
\DoxyCodeLine{\Hypertarget{stm32f4xx__hal__conf_8h_source_l00220}00220\ \textcolor{preprocessor}{\#define\ ETH\_TXBUFNB\ \ \ \ \ \ \ \ \ \ \ \ \ \ \ \ \ \ \ \ 4U\ \ \ \ \ \ \ }\textcolor{comment}{/*\ 4\ Tx\ buffers\ of\ size\ ETH\_TX\_BUF\_SIZE\ \ */}\textcolor{preprocessor}{}}
\DoxyCodeLine{\Hypertarget{stm32f4xx__hal__conf_8h_source_l00221}00221\ }
\DoxyCodeLine{\Hypertarget{stm32f4xx__hal__conf_8h_source_l00222}00222\ \textcolor{comment}{/*\ Section\ 2:\ PHY\ configuration\ section\ */}}
\DoxyCodeLine{\Hypertarget{stm32f4xx__hal__conf_8h_source_l00223}00223\ }
\DoxyCodeLine{\Hypertarget{stm32f4xx__hal__conf_8h_source_l00224}00224\ \textcolor{comment}{/*\ DP83848\_PHY\_ADDRESS\ Address*/}}
\DoxyCodeLine{\Hypertarget{stm32f4xx__hal__conf_8h_source_l00225}00225\ \textcolor{preprocessor}{\#define\ DP83848\_PHY\_ADDRESS\ \ \ \ \ \ \ \ \ \ \ 0x01U}}
\DoxyCodeLine{\Hypertarget{stm32f4xx__hal__conf_8h_source_l00226}00226\ \textcolor{comment}{/*\ PHY\ Reset\ delay\ these\ values\ are\ based\ on\ a\ 1\ ms\ Systick\ interrupt*/}}
\DoxyCodeLine{\Hypertarget{stm32f4xx__hal__conf_8h_source_l00227}00227\ \textcolor{preprocessor}{\#define\ PHY\_RESET\_DELAY\ \ \ \ \ \ \ \ \ \ \ \ \ \ \ \ \ 0x000000FFU}}
\DoxyCodeLine{\Hypertarget{stm32f4xx__hal__conf_8h_source_l00228}00228\ \textcolor{comment}{/*\ PHY\ Configuration\ delay\ */}}
\DoxyCodeLine{\Hypertarget{stm32f4xx__hal__conf_8h_source_l00229}00229\ \textcolor{preprocessor}{\#define\ PHY\_CONFIG\_DELAY\ \ \ \ \ \ \ \ \ \ \ \ \ \ \ \ 0x00000FFFU}}
\DoxyCodeLine{\Hypertarget{stm32f4xx__hal__conf_8h_source_l00230}00230\ }
\DoxyCodeLine{\Hypertarget{stm32f4xx__hal__conf_8h_source_l00231}00231\ \textcolor{preprocessor}{\#define\ PHY\_READ\_TO\ \ \ \ \ \ \ \ \ \ \ \ \ \ \ \ \ \ \ \ \ 0x0000FFFFU}}
\DoxyCodeLine{\Hypertarget{stm32f4xx__hal__conf_8h_source_l00232}00232\ \textcolor{preprocessor}{\#define\ PHY\_WRITE\_TO\ \ \ \ \ \ \ \ \ \ \ \ \ \ \ \ \ \ \ \ 0x0000FFFFU}}
\DoxyCodeLine{\Hypertarget{stm32f4xx__hal__conf_8h_source_l00233}00233\ }
\DoxyCodeLine{\Hypertarget{stm32f4xx__hal__conf_8h_source_l00234}00234\ \textcolor{comment}{/*\ Section\ 3:\ Common\ PHY\ Registers\ */}}
\DoxyCodeLine{\Hypertarget{stm32f4xx__hal__conf_8h_source_l00235}00235\ }
\DoxyCodeLine{\Hypertarget{stm32f4xx__hal__conf_8h_source_l00236}00236\ \textcolor{preprocessor}{\#define\ PHY\_BCR\ \ \ \ \ \ \ \ \ \ \ \ \ \ \ \ \ \ \ \ \ \ \ \ \ ((uint16\_t)0x0000U)\ \ \ \ }}
\DoxyCodeLine{\Hypertarget{stm32f4xx__hal__conf_8h_source_l00237}00237\ \textcolor{preprocessor}{\#define\ PHY\_BSR\ \ \ \ \ \ \ \ \ \ \ \ \ \ \ \ \ \ \ \ \ \ \ \ \ ((uint16\_t)0x0001U)\ \ \ \ }}
\DoxyCodeLine{\Hypertarget{stm32f4xx__hal__conf_8h_source_l00239}00239\ \textcolor{preprocessor}{\#define\ PHY\_RESET\ \ \ \ \ \ \ \ \ \ \ \ \ \ \ \ \ \ \ \ \ \ \ ((uint16\_t)0x8000U)\ \ }}
\DoxyCodeLine{\Hypertarget{stm32f4xx__hal__conf_8h_source_l00240}00240\ \textcolor{preprocessor}{\#define\ PHY\_LOOPBACK\ \ \ \ \ \ \ \ \ \ \ \ \ \ \ \ \ \ \ \ ((uint16\_t)0x4000U)\ \ }}
\DoxyCodeLine{\Hypertarget{stm32f4xx__hal__conf_8h_source_l00241}00241\ \textcolor{preprocessor}{\#define\ PHY\_FULLDUPLEX\_100M\ \ \ \ \ \ \ \ \ \ \ \ \ ((uint16\_t)0x2100U)\ \ }}
\DoxyCodeLine{\Hypertarget{stm32f4xx__hal__conf_8h_source_l00242}00242\ \textcolor{preprocessor}{\#define\ PHY\_HALFDUPLEX\_100M\ \ \ \ \ \ \ \ \ \ \ \ \ ((uint16\_t)0x2000U)\ \ }}
\DoxyCodeLine{\Hypertarget{stm32f4xx__hal__conf_8h_source_l00243}00243\ \textcolor{preprocessor}{\#define\ PHY\_FULLDUPLEX\_10M\ \ \ \ \ \ \ \ \ \ \ \ \ \ ((uint16\_t)0x0100U)\ \ }}
\DoxyCodeLine{\Hypertarget{stm32f4xx__hal__conf_8h_source_l00244}00244\ \textcolor{preprocessor}{\#define\ PHY\_HALFDUPLEX\_10M\ \ \ \ \ \ \ \ \ \ \ \ \ \ ((uint16\_t)0x0000U)\ \ }}
\DoxyCodeLine{\Hypertarget{stm32f4xx__hal__conf_8h_source_l00245}00245\ \textcolor{preprocessor}{\#define\ PHY\_AUTONEGOTIATION\ \ \ \ \ \ \ \ \ \ \ \ \ ((uint16\_t)0x1000U)\ \ }}
\DoxyCodeLine{\Hypertarget{stm32f4xx__hal__conf_8h_source_l00246}00246\ \textcolor{preprocessor}{\#define\ PHY\_RESTART\_AUTONEGOTIATION\ \ \ \ \ ((uint16\_t)0x0200U)\ \ }}
\DoxyCodeLine{\Hypertarget{stm32f4xx__hal__conf_8h_source_l00247}00247\ \textcolor{preprocessor}{\#define\ PHY\_POWERDOWN\ \ \ \ \ \ \ \ \ \ \ \ \ \ \ \ \ \ \ ((uint16\_t)0x0800U)\ \ }}
\DoxyCodeLine{\Hypertarget{stm32f4xx__hal__conf_8h_source_l00248}00248\ \textcolor{preprocessor}{\#define\ PHY\_ISOLATE\ \ \ \ \ \ \ \ \ \ \ \ \ \ \ \ \ \ \ \ \ ((uint16\_t)0x0400U)\ \ }}
\DoxyCodeLine{\Hypertarget{stm32f4xx__hal__conf_8h_source_l00250}00250\ \textcolor{preprocessor}{\#define\ PHY\_AUTONEGO\_COMPLETE\ \ \ \ \ \ \ \ \ \ \ ((uint16\_t)0x0020U)\ \ }}
\DoxyCodeLine{\Hypertarget{stm32f4xx__hal__conf_8h_source_l00251}00251\ \textcolor{preprocessor}{\#define\ PHY\_LINKED\_STATUS\ \ \ \ \ \ \ \ \ \ \ \ \ \ \ ((uint16\_t)0x0004U)\ \ }}
\DoxyCodeLine{\Hypertarget{stm32f4xx__hal__conf_8h_source_l00252}00252\ \textcolor{preprocessor}{\#define\ PHY\_JABBER\_DETECTION\ \ \ \ \ \ \ \ \ \ \ \ ((uint16\_t)0x0002U)\ \ }}
\DoxyCodeLine{\Hypertarget{stm32f4xx__hal__conf_8h_source_l00254}00254\ \textcolor{comment}{/*\ Section\ 4:\ Extended\ PHY\ Registers\ */}}
\DoxyCodeLine{\Hypertarget{stm32f4xx__hal__conf_8h_source_l00255}00255\ \textcolor{preprocessor}{\#define\ PHY\_SR\ \ \ \ \ \ \ \ \ \ \ \ \ \ \ \ \ \ \ \ \ \ \ \ \ \ ((uint16\_t)0x10U)\ \ \ \ }}
\DoxyCodeLine{\Hypertarget{stm32f4xx__hal__conf_8h_source_l00257}00257\ \textcolor{preprocessor}{\#define\ PHY\_SPEED\_STATUS\ \ \ \ \ \ \ \ \ \ \ \ \ \ \ \ ((uint16\_t)0x0002U)\ \ }}
\DoxyCodeLine{\Hypertarget{stm32f4xx__hal__conf_8h_source_l00258}00258\ \textcolor{preprocessor}{\#define\ PHY\_DUPLEX\_STATUS\ \ \ \ \ \ \ \ \ \ \ \ \ \ \ ((uint16\_t)0x0004U)\ \ }}
\DoxyCodeLine{\Hypertarget{stm32f4xx__hal__conf_8h_source_l00260}00260\ \textcolor{comment}{/*\ \#\#\#\#\#\#\#\#\#\#\#\#\#\#\#\#\#\#\ SPI\ peripheral\ configuration\ \#\#\#\#\#\#\#\#\#\#\#\#\#\#\#\#\#\#\#\#\#\#\#\#\#\#\ */}}
\DoxyCodeLine{\Hypertarget{stm32f4xx__hal__conf_8h_source_l00261}00261\ }
\DoxyCodeLine{\Hypertarget{stm32f4xx__hal__conf_8h_source_l00262}00262\ \textcolor{comment}{/*\ CRC\ FEATURE:\ Use\ to\ activate\ CRC\ feature\ inside\ HAL\ SPI\ Driver}}
\DoxyCodeLine{\Hypertarget{stm32f4xx__hal__conf_8h_source_l00263}00263\ \textcolor{comment}{*\ Activated:\ CRC\ code\ is\ present\ inside\ driver}}
\DoxyCodeLine{\Hypertarget{stm32f4xx__hal__conf_8h_source_l00264}00264\ \textcolor{comment}{*\ Deactivated:\ CRC\ code\ cleaned\ from\ driver}}
\DoxyCodeLine{\Hypertarget{stm32f4xx__hal__conf_8h_source_l00265}00265\ \textcolor{comment}{*/}}
\DoxyCodeLine{\Hypertarget{stm32f4xx__hal__conf_8h_source_l00266}00266\ }
\DoxyCodeLine{\Hypertarget{stm32f4xx__hal__conf_8h_source_l00267}00267\ \textcolor{preprocessor}{\#define\ USE\_SPI\_CRC\ \ \ \ \ \ \ \ \ \ \ \ \ \ \ \ \ \ \ \ \ 0U}}
\DoxyCodeLine{\Hypertarget{stm32f4xx__hal__conf_8h_source_l00268}00268\ }
\DoxyCodeLine{\Hypertarget{stm32f4xx__hal__conf_8h_source_l00269}00269\ \textcolor{comment}{/*\ Includes\ -\/-\/-\/-\/-\/-\/-\/-\/-\/-\/-\/-\/-\/-\/-\/-\/-\/-\/-\/-\/-\/-\/-\/-\/-\/-\/-\/-\/-\/-\/-\/-\/-\/-\/-\/-\/-\/-\/-\/-\/-\/-\/-\/-\/-\/-\/-\/-\/-\/-\/-\/-\/-\/-\/-\/-\/-\/-\/-\/-\/-\/-\/-\/-\/-\/-\/*/}}
\DoxyCodeLine{\Hypertarget{stm32f4xx__hal__conf_8h_source_l00274}00274\ \textcolor{preprocessor}{\#ifdef\ HAL\_RCC\_MODULE\_ENABLED}}
\DoxyCodeLine{\Hypertarget{stm32f4xx__hal__conf_8h_source_l00275}00275\ \textcolor{preprocessor}{\ \ \#include\ "{}stm32f4xx\_hal\_rcc.h"{}}}
\DoxyCodeLine{\Hypertarget{stm32f4xx__hal__conf_8h_source_l00276}00276\ \textcolor{preprocessor}{\#endif\ }\textcolor{comment}{/*\ HAL\_RCC\_MODULE\_ENABLED\ */}\textcolor{preprocessor}{}}
\DoxyCodeLine{\Hypertarget{stm32f4xx__hal__conf_8h_source_l00277}00277\ }
\DoxyCodeLine{\Hypertarget{stm32f4xx__hal__conf_8h_source_l00278}00278\ \textcolor{preprocessor}{\#ifdef\ HAL\_GPIO\_MODULE\_ENABLED}}
\DoxyCodeLine{\Hypertarget{stm32f4xx__hal__conf_8h_source_l00279}00279\ \textcolor{preprocessor}{\ \ \#include\ "{}stm32f4xx\_hal\_gpio.h"{}}}
\DoxyCodeLine{\Hypertarget{stm32f4xx__hal__conf_8h_source_l00280}00280\ \textcolor{preprocessor}{\#endif\ }\textcolor{comment}{/*\ HAL\_GPIO\_MODULE\_ENABLED\ */}\textcolor{preprocessor}{}}
\DoxyCodeLine{\Hypertarget{stm32f4xx__hal__conf_8h_source_l00281}00281\ }
\DoxyCodeLine{\Hypertarget{stm32f4xx__hal__conf_8h_source_l00282}00282\ \textcolor{preprocessor}{\#ifdef\ HAL\_EXTI\_MODULE\_ENABLED}}
\DoxyCodeLine{\Hypertarget{stm32f4xx__hal__conf_8h_source_l00283}00283\ \textcolor{preprocessor}{\ \ \#include\ "{}stm32f4xx\_hal\_exti.h"{}}}
\DoxyCodeLine{\Hypertarget{stm32f4xx__hal__conf_8h_source_l00284}00284\ \textcolor{preprocessor}{\#endif\ }\textcolor{comment}{/*\ HAL\_EXTI\_MODULE\_ENABLED\ */}\textcolor{preprocessor}{}}
\DoxyCodeLine{\Hypertarget{stm32f4xx__hal__conf_8h_source_l00285}00285\ }
\DoxyCodeLine{\Hypertarget{stm32f4xx__hal__conf_8h_source_l00286}00286\ \textcolor{preprocessor}{\#ifdef\ HAL\_DMA\_MODULE\_ENABLED}}
\DoxyCodeLine{\Hypertarget{stm32f4xx__hal__conf_8h_source_l00287}00287\ \textcolor{preprocessor}{\ \ \#include\ "{}stm32f4xx\_hal\_dma.h"{}}}
\DoxyCodeLine{\Hypertarget{stm32f4xx__hal__conf_8h_source_l00288}00288\ \textcolor{preprocessor}{\#endif\ }\textcolor{comment}{/*\ HAL\_DMA\_MODULE\_ENABLED\ */}\textcolor{preprocessor}{}}
\DoxyCodeLine{\Hypertarget{stm32f4xx__hal__conf_8h_source_l00289}00289\ }
\DoxyCodeLine{\Hypertarget{stm32f4xx__hal__conf_8h_source_l00290}00290\ \textcolor{preprocessor}{\#ifdef\ HAL\_CORTEX\_MODULE\_ENABLED}}
\DoxyCodeLine{\Hypertarget{stm32f4xx__hal__conf_8h_source_l00291}00291\ \textcolor{preprocessor}{\ \ \#include\ "{}stm32f4xx\_hal\_cortex.h"{}}}
\DoxyCodeLine{\Hypertarget{stm32f4xx__hal__conf_8h_source_l00292}00292\ \textcolor{preprocessor}{\#endif\ }\textcolor{comment}{/*\ HAL\_CORTEX\_MODULE\_ENABLED\ */}\textcolor{preprocessor}{}}
\DoxyCodeLine{\Hypertarget{stm32f4xx__hal__conf_8h_source_l00293}00293\ }
\DoxyCodeLine{\Hypertarget{stm32f4xx__hal__conf_8h_source_l00294}00294\ \textcolor{preprocessor}{\#ifdef\ HAL\_ADC\_MODULE\_ENABLED}}
\DoxyCodeLine{\Hypertarget{stm32f4xx__hal__conf_8h_source_l00295}00295\ \textcolor{preprocessor}{\ \ \#include\ "{}stm32f4xx\_hal\_adc.h"{}}}
\DoxyCodeLine{\Hypertarget{stm32f4xx__hal__conf_8h_source_l00296}00296\ \textcolor{preprocessor}{\#endif\ }\textcolor{comment}{/*\ HAL\_ADC\_MODULE\_ENABLED\ */}\textcolor{preprocessor}{}}
\DoxyCodeLine{\Hypertarget{stm32f4xx__hal__conf_8h_source_l00297}00297\ }
\DoxyCodeLine{\Hypertarget{stm32f4xx__hal__conf_8h_source_l00298}00298\ \textcolor{preprocessor}{\#ifdef\ HAL\_CAN\_MODULE\_ENABLED}}
\DoxyCodeLine{\Hypertarget{stm32f4xx__hal__conf_8h_source_l00299}00299\ \textcolor{preprocessor}{\ \ \#include\ "{}stm32f4xx\_hal\_can.h"{}}}
\DoxyCodeLine{\Hypertarget{stm32f4xx__hal__conf_8h_source_l00300}00300\ \textcolor{preprocessor}{\#endif\ }\textcolor{comment}{/*\ HAL\_CAN\_MODULE\_ENABLED\ */}\textcolor{preprocessor}{}}
\DoxyCodeLine{\Hypertarget{stm32f4xx__hal__conf_8h_source_l00301}00301\ }
\DoxyCodeLine{\Hypertarget{stm32f4xx__hal__conf_8h_source_l00302}00302\ \textcolor{preprocessor}{\#ifdef\ HAL\_CAN\_LEGACY\_MODULE\_ENABLED}}
\DoxyCodeLine{\Hypertarget{stm32f4xx__hal__conf_8h_source_l00303}00303\ \textcolor{preprocessor}{\ \ \#include\ "{}stm32f4xx\_hal\_can\_legacy.h"{}}}
\DoxyCodeLine{\Hypertarget{stm32f4xx__hal__conf_8h_source_l00304}00304\ \textcolor{preprocessor}{\#endif\ }\textcolor{comment}{/*\ HAL\_CAN\_LEGACY\_MODULE\_ENABLED\ */}\textcolor{preprocessor}{}}
\DoxyCodeLine{\Hypertarget{stm32f4xx__hal__conf_8h_source_l00305}00305\ }
\DoxyCodeLine{\Hypertarget{stm32f4xx__hal__conf_8h_source_l00306}00306\ \textcolor{preprocessor}{\#ifdef\ HAL\_CRC\_MODULE\_ENABLED}}
\DoxyCodeLine{\Hypertarget{stm32f4xx__hal__conf_8h_source_l00307}00307\ \textcolor{preprocessor}{\ \ \#include\ "{}stm32f4xx\_hal\_crc.h"{}}}
\DoxyCodeLine{\Hypertarget{stm32f4xx__hal__conf_8h_source_l00308}00308\ \textcolor{preprocessor}{\#endif\ }\textcolor{comment}{/*\ HAL\_CRC\_MODULE\_ENABLED\ */}\textcolor{preprocessor}{}}
\DoxyCodeLine{\Hypertarget{stm32f4xx__hal__conf_8h_source_l00309}00309\ }
\DoxyCodeLine{\Hypertarget{stm32f4xx__hal__conf_8h_source_l00310}00310\ \textcolor{preprocessor}{\#ifdef\ HAL\_CRYP\_MODULE\_ENABLED}}
\DoxyCodeLine{\Hypertarget{stm32f4xx__hal__conf_8h_source_l00311}00311\ \textcolor{preprocessor}{\ \ \#include\ "{}stm32f4xx\_hal\_cryp.h"{}}}
\DoxyCodeLine{\Hypertarget{stm32f4xx__hal__conf_8h_source_l00312}00312\ \textcolor{preprocessor}{\#endif\ }\textcolor{comment}{/*\ HAL\_CRYP\_MODULE\_ENABLED\ */}\textcolor{preprocessor}{}}
\DoxyCodeLine{\Hypertarget{stm32f4xx__hal__conf_8h_source_l00313}00313\ }
\DoxyCodeLine{\Hypertarget{stm32f4xx__hal__conf_8h_source_l00314}00314\ \textcolor{preprocessor}{\#ifdef\ HAL\_DMA2D\_MODULE\_ENABLED}}
\DoxyCodeLine{\Hypertarget{stm32f4xx__hal__conf_8h_source_l00315}00315\ \textcolor{preprocessor}{\ \ \#include\ "{}stm32f4xx\_hal\_dma2d.h"{}}}
\DoxyCodeLine{\Hypertarget{stm32f4xx__hal__conf_8h_source_l00316}00316\ \textcolor{preprocessor}{\#endif\ }\textcolor{comment}{/*\ HAL\_DMA2D\_MODULE\_ENABLED\ */}\textcolor{preprocessor}{}}
\DoxyCodeLine{\Hypertarget{stm32f4xx__hal__conf_8h_source_l00317}00317\ }
\DoxyCodeLine{\Hypertarget{stm32f4xx__hal__conf_8h_source_l00318}00318\ \textcolor{preprocessor}{\#ifdef\ HAL\_DAC\_MODULE\_ENABLED}}
\DoxyCodeLine{\Hypertarget{stm32f4xx__hal__conf_8h_source_l00319}00319\ \textcolor{preprocessor}{\ \ \#include\ "{}stm32f4xx\_hal\_dac.h"{}}}
\DoxyCodeLine{\Hypertarget{stm32f4xx__hal__conf_8h_source_l00320}00320\ \textcolor{preprocessor}{\#endif\ }\textcolor{comment}{/*\ HAL\_DAC\_MODULE\_ENABLED\ */}\textcolor{preprocessor}{}}
\DoxyCodeLine{\Hypertarget{stm32f4xx__hal__conf_8h_source_l00321}00321\ }
\DoxyCodeLine{\Hypertarget{stm32f4xx__hal__conf_8h_source_l00322}00322\ \textcolor{preprocessor}{\#ifdef\ HAL\_DCMI\_MODULE\_ENABLED}}
\DoxyCodeLine{\Hypertarget{stm32f4xx__hal__conf_8h_source_l00323}00323\ \textcolor{preprocessor}{\ \ \#include\ "{}stm32f4xx\_hal\_dcmi.h"{}}}
\DoxyCodeLine{\Hypertarget{stm32f4xx__hal__conf_8h_source_l00324}00324\ \textcolor{preprocessor}{\#endif\ }\textcolor{comment}{/*\ HAL\_DCMI\_MODULE\_ENABLED\ */}\textcolor{preprocessor}{}}
\DoxyCodeLine{\Hypertarget{stm32f4xx__hal__conf_8h_source_l00325}00325\ }
\DoxyCodeLine{\Hypertarget{stm32f4xx__hal__conf_8h_source_l00326}00326\ \textcolor{preprocessor}{\#ifdef\ HAL\_ETH\_MODULE\_ENABLED}}
\DoxyCodeLine{\Hypertarget{stm32f4xx__hal__conf_8h_source_l00327}00327\ \textcolor{preprocessor}{\ \ \#include\ "{}stm32f4xx\_hal\_eth.h"{}}}
\DoxyCodeLine{\Hypertarget{stm32f4xx__hal__conf_8h_source_l00328}00328\ \textcolor{preprocessor}{\#endif\ }\textcolor{comment}{/*\ HAL\_ETH\_MODULE\_ENABLED\ */}\textcolor{preprocessor}{}}
\DoxyCodeLine{\Hypertarget{stm32f4xx__hal__conf_8h_source_l00329}00329\ }
\DoxyCodeLine{\Hypertarget{stm32f4xx__hal__conf_8h_source_l00330}00330\ \textcolor{preprocessor}{\#ifdef\ HAL\_FLASH\_MODULE\_ENABLED}}
\DoxyCodeLine{\Hypertarget{stm32f4xx__hal__conf_8h_source_l00331}00331\ \textcolor{preprocessor}{\ \ \#include\ "{}stm32f4xx\_hal\_flash.h"{}}}
\DoxyCodeLine{\Hypertarget{stm32f4xx__hal__conf_8h_source_l00332}00332\ \textcolor{preprocessor}{\#endif\ }\textcolor{comment}{/*\ HAL\_FLASH\_MODULE\_ENABLED\ */}\textcolor{preprocessor}{}}
\DoxyCodeLine{\Hypertarget{stm32f4xx__hal__conf_8h_source_l00333}00333\ }
\DoxyCodeLine{\Hypertarget{stm32f4xx__hal__conf_8h_source_l00334}00334\ \textcolor{preprocessor}{\#ifdef\ HAL\_SRAM\_MODULE\_ENABLED}}
\DoxyCodeLine{\Hypertarget{stm32f4xx__hal__conf_8h_source_l00335}00335\ \textcolor{preprocessor}{\ \ \#include\ "{}stm32f4xx\_hal\_sram.h"{}}}
\DoxyCodeLine{\Hypertarget{stm32f4xx__hal__conf_8h_source_l00336}00336\ \textcolor{preprocessor}{\#endif\ }\textcolor{comment}{/*\ HAL\_SRAM\_MODULE\_ENABLED\ */}\textcolor{preprocessor}{}}
\DoxyCodeLine{\Hypertarget{stm32f4xx__hal__conf_8h_source_l00337}00337\ }
\DoxyCodeLine{\Hypertarget{stm32f4xx__hal__conf_8h_source_l00338}00338\ \textcolor{preprocessor}{\#ifdef\ HAL\_NOR\_MODULE\_ENABLED}}
\DoxyCodeLine{\Hypertarget{stm32f4xx__hal__conf_8h_source_l00339}00339\ \textcolor{preprocessor}{\ \ \#include\ "{}stm32f4xx\_hal\_nor.h"{}}}
\DoxyCodeLine{\Hypertarget{stm32f4xx__hal__conf_8h_source_l00340}00340\ \textcolor{preprocessor}{\#endif\ }\textcolor{comment}{/*\ HAL\_NOR\_MODULE\_ENABLED\ */}\textcolor{preprocessor}{}}
\DoxyCodeLine{\Hypertarget{stm32f4xx__hal__conf_8h_source_l00341}00341\ }
\DoxyCodeLine{\Hypertarget{stm32f4xx__hal__conf_8h_source_l00342}00342\ \textcolor{preprocessor}{\#ifdef\ HAL\_NAND\_MODULE\_ENABLED}}
\DoxyCodeLine{\Hypertarget{stm32f4xx__hal__conf_8h_source_l00343}00343\ \textcolor{preprocessor}{\ \ \#include\ "{}stm32f4xx\_hal\_nand.h"{}}}
\DoxyCodeLine{\Hypertarget{stm32f4xx__hal__conf_8h_source_l00344}00344\ \textcolor{preprocessor}{\#endif\ }\textcolor{comment}{/*\ HAL\_NAND\_MODULE\_ENABLED\ */}\textcolor{preprocessor}{}}
\DoxyCodeLine{\Hypertarget{stm32f4xx__hal__conf_8h_source_l00345}00345\ }
\DoxyCodeLine{\Hypertarget{stm32f4xx__hal__conf_8h_source_l00346}00346\ \textcolor{preprocessor}{\#ifdef\ HAL\_PCCARD\_MODULE\_ENABLED}}
\DoxyCodeLine{\Hypertarget{stm32f4xx__hal__conf_8h_source_l00347}00347\ \textcolor{preprocessor}{\ \ \#include\ "{}stm32f4xx\_hal\_pccard.h"{}}}
\DoxyCodeLine{\Hypertarget{stm32f4xx__hal__conf_8h_source_l00348}00348\ \textcolor{preprocessor}{\#endif\ }\textcolor{comment}{/*\ HAL\_PCCARD\_MODULE\_ENABLED\ */}\textcolor{preprocessor}{}}
\DoxyCodeLine{\Hypertarget{stm32f4xx__hal__conf_8h_source_l00349}00349\ }
\DoxyCodeLine{\Hypertarget{stm32f4xx__hal__conf_8h_source_l00350}00350\ \textcolor{preprocessor}{\#ifdef\ HAL\_SDRAM\_MODULE\_ENABLED}}
\DoxyCodeLine{\Hypertarget{stm32f4xx__hal__conf_8h_source_l00351}00351\ \textcolor{preprocessor}{\ \ \#include\ "{}stm32f4xx\_hal\_sdram.h"{}}}
\DoxyCodeLine{\Hypertarget{stm32f4xx__hal__conf_8h_source_l00352}00352\ \textcolor{preprocessor}{\#endif\ }\textcolor{comment}{/*\ HAL\_SDRAM\_MODULE\_ENABLED\ */}\textcolor{preprocessor}{}}
\DoxyCodeLine{\Hypertarget{stm32f4xx__hal__conf_8h_source_l00353}00353\ }
\DoxyCodeLine{\Hypertarget{stm32f4xx__hal__conf_8h_source_l00354}00354\ \textcolor{preprocessor}{\#ifdef\ HAL\_HASH\_MODULE\_ENABLED}}
\DoxyCodeLine{\Hypertarget{stm32f4xx__hal__conf_8h_source_l00355}00355\ \textcolor{preprocessor}{\ \#include\ "{}stm32f4xx\_hal\_hash.h"{}}}
\DoxyCodeLine{\Hypertarget{stm32f4xx__hal__conf_8h_source_l00356}00356\ \textcolor{preprocessor}{\#endif\ }\textcolor{comment}{/*\ HAL\_HASH\_MODULE\_ENABLED\ */}\textcolor{preprocessor}{}}
\DoxyCodeLine{\Hypertarget{stm32f4xx__hal__conf_8h_source_l00357}00357\ }
\DoxyCodeLine{\Hypertarget{stm32f4xx__hal__conf_8h_source_l00358}00358\ \textcolor{preprocessor}{\#ifdef\ HAL\_I2C\_MODULE\_ENABLED}}
\DoxyCodeLine{\Hypertarget{stm32f4xx__hal__conf_8h_source_l00359}00359\ \textcolor{preprocessor}{\ \#include\ "{}stm32f4xx\_hal\_i2c.h"{}}}
\DoxyCodeLine{\Hypertarget{stm32f4xx__hal__conf_8h_source_l00360}00360\ \textcolor{preprocessor}{\#endif\ }\textcolor{comment}{/*\ HAL\_I2C\_MODULE\_ENABLED\ */}\textcolor{preprocessor}{}}
\DoxyCodeLine{\Hypertarget{stm32f4xx__hal__conf_8h_source_l00361}00361\ }
\DoxyCodeLine{\Hypertarget{stm32f4xx__hal__conf_8h_source_l00362}00362\ \textcolor{preprocessor}{\#ifdef\ HAL\_SMBUS\_MODULE\_ENABLED}}
\DoxyCodeLine{\Hypertarget{stm32f4xx__hal__conf_8h_source_l00363}00363\ \textcolor{preprocessor}{\ \#include\ "{}stm32f4xx\_hal\_smbus.h"{}}}
\DoxyCodeLine{\Hypertarget{stm32f4xx__hal__conf_8h_source_l00364}00364\ \textcolor{preprocessor}{\#endif\ }\textcolor{comment}{/*\ HAL\_SMBUS\_MODULE\_ENABLED\ */}\textcolor{preprocessor}{}}
\DoxyCodeLine{\Hypertarget{stm32f4xx__hal__conf_8h_source_l00365}00365\ }
\DoxyCodeLine{\Hypertarget{stm32f4xx__hal__conf_8h_source_l00366}00366\ \textcolor{preprocessor}{\#ifdef\ HAL\_I2S\_MODULE\_ENABLED}}
\DoxyCodeLine{\Hypertarget{stm32f4xx__hal__conf_8h_source_l00367}00367\ \textcolor{preprocessor}{\ \#include\ "{}stm32f4xx\_hal\_i2s.h"{}}}
\DoxyCodeLine{\Hypertarget{stm32f4xx__hal__conf_8h_source_l00368}00368\ \textcolor{preprocessor}{\#endif\ }\textcolor{comment}{/*\ HAL\_I2S\_MODULE\_ENABLED\ */}\textcolor{preprocessor}{}}
\DoxyCodeLine{\Hypertarget{stm32f4xx__hal__conf_8h_source_l00369}00369\ }
\DoxyCodeLine{\Hypertarget{stm32f4xx__hal__conf_8h_source_l00370}00370\ \textcolor{preprocessor}{\#ifdef\ HAL\_IWDG\_MODULE\_ENABLED}}
\DoxyCodeLine{\Hypertarget{stm32f4xx__hal__conf_8h_source_l00371}00371\ \textcolor{preprocessor}{\ \#include\ "{}stm32f4xx\_hal\_iwdg.h"{}}}
\DoxyCodeLine{\Hypertarget{stm32f4xx__hal__conf_8h_source_l00372}00372\ \textcolor{preprocessor}{\#endif\ }\textcolor{comment}{/*\ HAL\_IWDG\_MODULE\_ENABLED\ */}\textcolor{preprocessor}{}}
\DoxyCodeLine{\Hypertarget{stm32f4xx__hal__conf_8h_source_l00373}00373\ }
\DoxyCodeLine{\Hypertarget{stm32f4xx__hal__conf_8h_source_l00374}00374\ \textcolor{preprocessor}{\#ifdef\ HAL\_LTDC\_MODULE\_ENABLED}}
\DoxyCodeLine{\Hypertarget{stm32f4xx__hal__conf_8h_source_l00375}00375\ \textcolor{preprocessor}{\ \#include\ "{}stm32f4xx\_hal\_ltdc.h"{}}}
\DoxyCodeLine{\Hypertarget{stm32f4xx__hal__conf_8h_source_l00376}00376\ \textcolor{preprocessor}{\#endif\ }\textcolor{comment}{/*\ HAL\_LTDC\_MODULE\_ENABLED\ */}\textcolor{preprocessor}{}}
\DoxyCodeLine{\Hypertarget{stm32f4xx__hal__conf_8h_source_l00377}00377\ }
\DoxyCodeLine{\Hypertarget{stm32f4xx__hal__conf_8h_source_l00378}00378\ \textcolor{preprocessor}{\#ifdef\ HAL\_PWR\_MODULE\_ENABLED}}
\DoxyCodeLine{\Hypertarget{stm32f4xx__hal__conf_8h_source_l00379}00379\ \textcolor{preprocessor}{\ \#include\ "{}stm32f4xx\_hal\_pwr.h"{}}}
\DoxyCodeLine{\Hypertarget{stm32f4xx__hal__conf_8h_source_l00380}00380\ \textcolor{preprocessor}{\#endif\ }\textcolor{comment}{/*\ HAL\_PWR\_MODULE\_ENABLED\ */}\textcolor{preprocessor}{}}
\DoxyCodeLine{\Hypertarget{stm32f4xx__hal__conf_8h_source_l00381}00381\ }
\DoxyCodeLine{\Hypertarget{stm32f4xx__hal__conf_8h_source_l00382}00382\ \textcolor{preprocessor}{\#ifdef\ HAL\_RNG\_MODULE\_ENABLED}}
\DoxyCodeLine{\Hypertarget{stm32f4xx__hal__conf_8h_source_l00383}00383\ \textcolor{preprocessor}{\ \#include\ "{}stm32f4xx\_hal\_rng.h"{}}}
\DoxyCodeLine{\Hypertarget{stm32f4xx__hal__conf_8h_source_l00384}00384\ \textcolor{preprocessor}{\#endif\ }\textcolor{comment}{/*\ HAL\_RNG\_MODULE\_ENABLED\ */}\textcolor{preprocessor}{}}
\DoxyCodeLine{\Hypertarget{stm32f4xx__hal__conf_8h_source_l00385}00385\ }
\DoxyCodeLine{\Hypertarget{stm32f4xx__hal__conf_8h_source_l00386}00386\ \textcolor{preprocessor}{\#ifdef\ HAL\_RTC\_MODULE\_ENABLED}}
\DoxyCodeLine{\Hypertarget{stm32f4xx__hal__conf_8h_source_l00387}00387\ \textcolor{preprocessor}{\ \#include\ "{}stm32f4xx\_hal\_rtc.h"{}}}
\DoxyCodeLine{\Hypertarget{stm32f4xx__hal__conf_8h_source_l00388}00388\ \textcolor{preprocessor}{\#endif\ }\textcolor{comment}{/*\ HAL\_RTC\_MODULE\_ENABLED\ */}\textcolor{preprocessor}{}}
\DoxyCodeLine{\Hypertarget{stm32f4xx__hal__conf_8h_source_l00389}00389\ }
\DoxyCodeLine{\Hypertarget{stm32f4xx__hal__conf_8h_source_l00390}00390\ \textcolor{preprocessor}{\#ifdef\ HAL\_SAI\_MODULE\_ENABLED}}
\DoxyCodeLine{\Hypertarget{stm32f4xx__hal__conf_8h_source_l00391}00391\ \textcolor{preprocessor}{\ \#include\ "{}stm32f4xx\_hal\_sai.h"{}}}
\DoxyCodeLine{\Hypertarget{stm32f4xx__hal__conf_8h_source_l00392}00392\ \textcolor{preprocessor}{\#endif\ }\textcolor{comment}{/*\ HAL\_SAI\_MODULE\_ENABLED\ */}\textcolor{preprocessor}{}}
\DoxyCodeLine{\Hypertarget{stm32f4xx__hal__conf_8h_source_l00393}00393\ }
\DoxyCodeLine{\Hypertarget{stm32f4xx__hal__conf_8h_source_l00394}00394\ \textcolor{preprocessor}{\#ifdef\ HAL\_SD\_MODULE\_ENABLED}}
\DoxyCodeLine{\Hypertarget{stm32f4xx__hal__conf_8h_source_l00395}00395\ \textcolor{preprocessor}{\ \#include\ "{}stm32f4xx\_hal\_sd.h"{}}}
\DoxyCodeLine{\Hypertarget{stm32f4xx__hal__conf_8h_source_l00396}00396\ \textcolor{preprocessor}{\#endif\ }\textcolor{comment}{/*\ HAL\_SD\_MODULE\_ENABLED\ */}\textcolor{preprocessor}{}}
\DoxyCodeLine{\Hypertarget{stm32f4xx__hal__conf_8h_source_l00397}00397\ }
\DoxyCodeLine{\Hypertarget{stm32f4xx__hal__conf_8h_source_l00398}00398\ \textcolor{preprocessor}{\#ifdef\ HAL\_SPI\_MODULE\_ENABLED}}
\DoxyCodeLine{\Hypertarget{stm32f4xx__hal__conf_8h_source_l00399}00399\ \textcolor{preprocessor}{\ \#include\ "{}stm32f4xx\_hal\_spi.h"{}}}
\DoxyCodeLine{\Hypertarget{stm32f4xx__hal__conf_8h_source_l00400}00400\ \textcolor{preprocessor}{\#endif\ }\textcolor{comment}{/*\ HAL\_SPI\_MODULE\_ENABLED\ */}\textcolor{preprocessor}{}}
\DoxyCodeLine{\Hypertarget{stm32f4xx__hal__conf_8h_source_l00401}00401\ }
\DoxyCodeLine{\Hypertarget{stm32f4xx__hal__conf_8h_source_l00402}00402\ \textcolor{preprocessor}{\#ifdef\ HAL\_TIM\_MODULE\_ENABLED}}
\DoxyCodeLine{\Hypertarget{stm32f4xx__hal__conf_8h_source_l00403}00403\ \textcolor{preprocessor}{\ \#include\ "{}stm32f4xx\_hal\_tim.h"{}}}
\DoxyCodeLine{\Hypertarget{stm32f4xx__hal__conf_8h_source_l00404}00404\ \textcolor{preprocessor}{\#endif\ }\textcolor{comment}{/*\ HAL\_TIM\_MODULE\_ENABLED\ */}\textcolor{preprocessor}{}}
\DoxyCodeLine{\Hypertarget{stm32f4xx__hal__conf_8h_source_l00405}00405\ }
\DoxyCodeLine{\Hypertarget{stm32f4xx__hal__conf_8h_source_l00406}00406\ \textcolor{preprocessor}{\#ifdef\ HAL\_UART\_MODULE\_ENABLED}}
\DoxyCodeLine{\Hypertarget{stm32f4xx__hal__conf_8h_source_l00407}00407\ \textcolor{preprocessor}{\ \#include\ "{}stm32f4xx\_hal\_uart.h"{}}}
\DoxyCodeLine{\Hypertarget{stm32f4xx__hal__conf_8h_source_l00408}00408\ \textcolor{preprocessor}{\#endif\ }\textcolor{comment}{/*\ HAL\_UART\_MODULE\_ENABLED\ */}\textcolor{preprocessor}{}}
\DoxyCodeLine{\Hypertarget{stm32f4xx__hal__conf_8h_source_l00409}00409\ }
\DoxyCodeLine{\Hypertarget{stm32f4xx__hal__conf_8h_source_l00410}00410\ \textcolor{preprocessor}{\#ifdef\ HAL\_USART\_MODULE\_ENABLED}}
\DoxyCodeLine{\Hypertarget{stm32f4xx__hal__conf_8h_source_l00411}00411\ \textcolor{preprocessor}{\ \#include\ "{}stm32f4xx\_hal\_usart.h"{}}}
\DoxyCodeLine{\Hypertarget{stm32f4xx__hal__conf_8h_source_l00412}00412\ \textcolor{preprocessor}{\#endif\ }\textcolor{comment}{/*\ HAL\_USART\_MODULE\_ENABLED\ */}\textcolor{preprocessor}{}}
\DoxyCodeLine{\Hypertarget{stm32f4xx__hal__conf_8h_source_l00413}00413\ }
\DoxyCodeLine{\Hypertarget{stm32f4xx__hal__conf_8h_source_l00414}00414\ \textcolor{preprocessor}{\#ifdef\ HAL\_IRDA\_MODULE\_ENABLED}}
\DoxyCodeLine{\Hypertarget{stm32f4xx__hal__conf_8h_source_l00415}00415\ \textcolor{preprocessor}{\ \#include\ "{}stm32f4xx\_hal\_irda.h"{}}}
\DoxyCodeLine{\Hypertarget{stm32f4xx__hal__conf_8h_source_l00416}00416\ \textcolor{preprocessor}{\#endif\ }\textcolor{comment}{/*\ HAL\_IRDA\_MODULE\_ENABLED\ */}\textcolor{preprocessor}{}}
\DoxyCodeLine{\Hypertarget{stm32f4xx__hal__conf_8h_source_l00417}00417\ }
\DoxyCodeLine{\Hypertarget{stm32f4xx__hal__conf_8h_source_l00418}00418\ \textcolor{preprocessor}{\#ifdef\ HAL\_SMARTCARD\_MODULE\_ENABLED}}
\DoxyCodeLine{\Hypertarget{stm32f4xx__hal__conf_8h_source_l00419}00419\ \textcolor{preprocessor}{\ \#include\ "{}stm32f4xx\_hal\_smartcard.h"{}}}
\DoxyCodeLine{\Hypertarget{stm32f4xx__hal__conf_8h_source_l00420}00420\ \textcolor{preprocessor}{\#endif\ }\textcolor{comment}{/*\ HAL\_SMARTCARD\_MODULE\_ENABLED\ */}\textcolor{preprocessor}{}}
\DoxyCodeLine{\Hypertarget{stm32f4xx__hal__conf_8h_source_l00421}00421\ }
\DoxyCodeLine{\Hypertarget{stm32f4xx__hal__conf_8h_source_l00422}00422\ \textcolor{preprocessor}{\#ifdef\ HAL\_WWDG\_MODULE\_ENABLED}}
\DoxyCodeLine{\Hypertarget{stm32f4xx__hal__conf_8h_source_l00423}00423\ \textcolor{preprocessor}{\ \#include\ "{}stm32f4xx\_hal\_wwdg.h"{}}}
\DoxyCodeLine{\Hypertarget{stm32f4xx__hal__conf_8h_source_l00424}00424\ \textcolor{preprocessor}{\#endif\ }\textcolor{comment}{/*\ HAL\_WWDG\_MODULE\_ENABLED\ */}\textcolor{preprocessor}{}}
\DoxyCodeLine{\Hypertarget{stm32f4xx__hal__conf_8h_source_l00425}00425\ }
\DoxyCodeLine{\Hypertarget{stm32f4xx__hal__conf_8h_source_l00426}00426\ \textcolor{preprocessor}{\#ifdef\ HAL\_PCD\_MODULE\_ENABLED}}
\DoxyCodeLine{\Hypertarget{stm32f4xx__hal__conf_8h_source_l00427}00427\ \textcolor{preprocessor}{\ \#include\ "{}stm32f4xx\_hal\_pcd.h"{}}}
\DoxyCodeLine{\Hypertarget{stm32f4xx__hal__conf_8h_source_l00428}00428\ \textcolor{preprocessor}{\#endif\ }\textcolor{comment}{/*\ HAL\_PCD\_MODULE\_ENABLED\ */}\textcolor{preprocessor}{}}
\DoxyCodeLine{\Hypertarget{stm32f4xx__hal__conf_8h_source_l00429}00429\ }
\DoxyCodeLine{\Hypertarget{stm32f4xx__hal__conf_8h_source_l00430}00430\ \textcolor{preprocessor}{\#ifdef\ HAL\_HCD\_MODULE\_ENABLED}}
\DoxyCodeLine{\Hypertarget{stm32f4xx__hal__conf_8h_source_l00431}00431\ \textcolor{preprocessor}{\ \#include\ "{}stm32f4xx\_hal\_hcd.h"{}}}
\DoxyCodeLine{\Hypertarget{stm32f4xx__hal__conf_8h_source_l00432}00432\ \textcolor{preprocessor}{\#endif\ }\textcolor{comment}{/*\ HAL\_HCD\_MODULE\_ENABLED\ */}\textcolor{preprocessor}{}}
\DoxyCodeLine{\Hypertarget{stm32f4xx__hal__conf_8h_source_l00433}00433\ }
\DoxyCodeLine{\Hypertarget{stm32f4xx__hal__conf_8h_source_l00434}00434\ \textcolor{preprocessor}{\#ifdef\ HAL\_DSI\_MODULE\_ENABLED}}
\DoxyCodeLine{\Hypertarget{stm32f4xx__hal__conf_8h_source_l00435}00435\ \textcolor{preprocessor}{\ \#include\ "{}stm32f4xx\_hal\_dsi.h"{}}}
\DoxyCodeLine{\Hypertarget{stm32f4xx__hal__conf_8h_source_l00436}00436\ \textcolor{preprocessor}{\#endif\ }\textcolor{comment}{/*\ HAL\_DSI\_MODULE\_ENABLED\ */}\textcolor{preprocessor}{}}
\DoxyCodeLine{\Hypertarget{stm32f4xx__hal__conf_8h_source_l00437}00437\ }
\DoxyCodeLine{\Hypertarget{stm32f4xx__hal__conf_8h_source_l00438}00438\ \textcolor{preprocessor}{\#ifdef\ HAL\_QSPI\_MODULE\_ENABLED}}
\DoxyCodeLine{\Hypertarget{stm32f4xx__hal__conf_8h_source_l00439}00439\ \textcolor{preprocessor}{\ \#include\ "{}stm32f4xx\_hal\_qspi.h"{}}}
\DoxyCodeLine{\Hypertarget{stm32f4xx__hal__conf_8h_source_l00440}00440\ \textcolor{preprocessor}{\#endif\ }\textcolor{comment}{/*\ HAL\_QSPI\_MODULE\_ENABLED\ */}\textcolor{preprocessor}{}}
\DoxyCodeLine{\Hypertarget{stm32f4xx__hal__conf_8h_source_l00441}00441\ }
\DoxyCodeLine{\Hypertarget{stm32f4xx__hal__conf_8h_source_l00442}00442\ \textcolor{preprocessor}{\#ifdef\ HAL\_CEC\_MODULE\_ENABLED}}
\DoxyCodeLine{\Hypertarget{stm32f4xx__hal__conf_8h_source_l00443}00443\ \textcolor{preprocessor}{\ \#include\ "{}stm32f4xx\_hal\_cec.h"{}}}
\DoxyCodeLine{\Hypertarget{stm32f4xx__hal__conf_8h_source_l00444}00444\ \textcolor{preprocessor}{\#endif\ }\textcolor{comment}{/*\ HAL\_CEC\_MODULE\_ENABLED\ */}\textcolor{preprocessor}{}}
\DoxyCodeLine{\Hypertarget{stm32f4xx__hal__conf_8h_source_l00445}00445\ }
\DoxyCodeLine{\Hypertarget{stm32f4xx__hal__conf_8h_source_l00446}00446\ \textcolor{preprocessor}{\#ifdef\ HAL\_FMPI2C\_MODULE\_ENABLED}}
\DoxyCodeLine{\Hypertarget{stm32f4xx__hal__conf_8h_source_l00447}00447\ \textcolor{preprocessor}{\ \#include\ "{}stm32f4xx\_hal\_fmpi2c.h"{}}}
\DoxyCodeLine{\Hypertarget{stm32f4xx__hal__conf_8h_source_l00448}00448\ \textcolor{preprocessor}{\#endif\ }\textcolor{comment}{/*\ HAL\_FMPI2C\_MODULE\_ENABLED\ */}\textcolor{preprocessor}{}}
\DoxyCodeLine{\Hypertarget{stm32f4xx__hal__conf_8h_source_l00449}00449\ }
\DoxyCodeLine{\Hypertarget{stm32f4xx__hal__conf_8h_source_l00450}00450\ \textcolor{preprocessor}{\#ifdef\ HAL\_FMPSMBUS\_MODULE\_ENABLED}}
\DoxyCodeLine{\Hypertarget{stm32f4xx__hal__conf_8h_source_l00451}00451\ \textcolor{preprocessor}{\ \#include\ "{}stm32f4xx\_hal\_fmpsmbus.h"{}}}
\DoxyCodeLine{\Hypertarget{stm32f4xx__hal__conf_8h_source_l00452}00452\ \textcolor{preprocessor}{\#endif\ }\textcolor{comment}{/*\ HAL\_FMPSMBUS\_MODULE\_ENABLED\ */}\textcolor{preprocessor}{}}
\DoxyCodeLine{\Hypertarget{stm32f4xx__hal__conf_8h_source_l00453}00453\ }
\DoxyCodeLine{\Hypertarget{stm32f4xx__hal__conf_8h_source_l00454}00454\ \textcolor{preprocessor}{\#ifdef\ HAL\_SPDIFRX\_MODULE\_ENABLED}}
\DoxyCodeLine{\Hypertarget{stm32f4xx__hal__conf_8h_source_l00455}00455\ \textcolor{preprocessor}{\ \#include\ "{}stm32f4xx\_hal\_spdifrx.h"{}}}
\DoxyCodeLine{\Hypertarget{stm32f4xx__hal__conf_8h_source_l00456}00456\ \textcolor{preprocessor}{\#endif\ }\textcolor{comment}{/*\ HAL\_SPDIFRX\_MODULE\_ENABLED\ */}\textcolor{preprocessor}{}}
\DoxyCodeLine{\Hypertarget{stm32f4xx__hal__conf_8h_source_l00457}00457\ }
\DoxyCodeLine{\Hypertarget{stm32f4xx__hal__conf_8h_source_l00458}00458\ \textcolor{preprocessor}{\#ifdef\ HAL\_DFSDM\_MODULE\_ENABLED}}
\DoxyCodeLine{\Hypertarget{stm32f4xx__hal__conf_8h_source_l00459}00459\ \textcolor{preprocessor}{\ \#include\ "{}stm32f4xx\_hal\_dfsdm.h"{}}}
\DoxyCodeLine{\Hypertarget{stm32f4xx__hal__conf_8h_source_l00460}00460\ \textcolor{preprocessor}{\#endif\ }\textcolor{comment}{/*\ HAL\_DFSDM\_MODULE\_ENABLED\ */}\textcolor{preprocessor}{}}
\DoxyCodeLine{\Hypertarget{stm32f4xx__hal__conf_8h_source_l00461}00461\ }
\DoxyCodeLine{\Hypertarget{stm32f4xx__hal__conf_8h_source_l00462}00462\ \textcolor{preprocessor}{\#ifdef\ HAL\_LPTIM\_MODULE\_ENABLED}}
\DoxyCodeLine{\Hypertarget{stm32f4xx__hal__conf_8h_source_l00463}00463\ \textcolor{preprocessor}{\ \#include\ "{}stm32f4xx\_hal\_lptim.h"{}}}
\DoxyCodeLine{\Hypertarget{stm32f4xx__hal__conf_8h_source_l00464}00464\ \textcolor{preprocessor}{\#endif\ }\textcolor{comment}{/*\ HAL\_LPTIM\_MODULE\_ENABLED\ */}\textcolor{preprocessor}{}}
\DoxyCodeLine{\Hypertarget{stm32f4xx__hal__conf_8h_source_l00465}00465\ }
\DoxyCodeLine{\Hypertarget{stm32f4xx__hal__conf_8h_source_l00466}00466\ \textcolor{preprocessor}{\#ifdef\ HAL\_MMC\_MODULE\_ENABLED}}
\DoxyCodeLine{\Hypertarget{stm32f4xx__hal__conf_8h_source_l00467}00467\ \textcolor{preprocessor}{\ \#include\ "{}stm32f4xx\_hal\_mmc.h"{}}}
\DoxyCodeLine{\Hypertarget{stm32f4xx__hal__conf_8h_source_l00468}00468\ \textcolor{preprocessor}{\#endif\ }\textcolor{comment}{/*\ HAL\_MMC\_MODULE\_ENABLED\ */}\textcolor{preprocessor}{}}
\DoxyCodeLine{\Hypertarget{stm32f4xx__hal__conf_8h_source_l00469}00469\ }
\DoxyCodeLine{\Hypertarget{stm32f4xx__hal__conf_8h_source_l00470}00470\ \textcolor{comment}{/*\ Exported\ macro\ -\/-\/-\/-\/-\/-\/-\/-\/-\/-\/-\/-\/-\/-\/-\/-\/-\/-\/-\/-\/-\/-\/-\/-\/-\/-\/-\/-\/-\/-\/-\/-\/-\/-\/-\/-\/-\/-\/-\/-\/-\/-\/-\/-\/-\/-\/-\/-\/-\/-\/-\/-\/-\/-\/-\/-\/-\/-\/-\/-\/*/}}
\DoxyCodeLine{\Hypertarget{stm32f4xx__hal__conf_8h_source_l00471}00471\ \textcolor{preprocessor}{\#ifdef\ \ USE\_FULL\_ASSERT}}
\DoxyCodeLine{\Hypertarget{stm32f4xx__hal__conf_8h_source_l00480}00480\ \textcolor{preprocessor}{\ \ \#define\ assert\_param(expr)\ ((expr)\ ?\ (void)0U\ :\ assert\_failed((uint8\_t\ *)\_\_FILE\_\_,\ \_\_LINE\_\_))}}
\DoxyCodeLine{\Hypertarget{stm32f4xx__hal__conf_8h_source_l00481}00481\ \textcolor{comment}{/*\ Exported\ functions\ -\/-\/-\/-\/-\/-\/-\/-\/-\/-\/-\/-\/-\/-\/-\/-\/-\/-\/-\/-\/-\/-\/-\/-\/-\/-\/-\/-\/-\/-\/-\/-\/-\/-\/-\/-\/-\/-\/-\/-\/-\/-\/-\/-\/-\/-\/-\/-\/-\/-\/-\/-\/-\/-\/-\/\ */}}
\DoxyCodeLine{\Hypertarget{stm32f4xx__hal__conf_8h_source_l00482}00482\ \ \ \textcolor{keywordtype}{void}\ assert\_failed(uint8\_t*\ file,\ uint32\_t\ line);}
\DoxyCodeLine{\Hypertarget{stm32f4xx__hal__conf_8h_source_l00483}00483\ \textcolor{preprocessor}{\#else}}
\DoxyCodeLine{\Hypertarget{stm32f4xx__hal__conf_8h_source_l00484}00484\ \textcolor{preprocessor}{\ \ \#define\ assert\_param(expr)\ ((void)0U)}}
\DoxyCodeLine{\Hypertarget{stm32f4xx__hal__conf_8h_source_l00485}00485\ \textcolor{preprocessor}{\#endif\ }\textcolor{comment}{/*\ USE\_FULL\_ASSERT\ */}\textcolor{preprocessor}{}}
\DoxyCodeLine{\Hypertarget{stm32f4xx__hal__conf_8h_source_l00486}00486\ }
\DoxyCodeLine{\Hypertarget{stm32f4xx__hal__conf_8h_source_l00487}00487\ \textcolor{preprocessor}{\#ifdef\ \_\_cplusplus}}
\DoxyCodeLine{\Hypertarget{stm32f4xx__hal__conf_8h_source_l00488}00488\ \}}
\DoxyCodeLine{\Hypertarget{stm32f4xx__hal__conf_8h_source_l00489}00489\ \textcolor{preprocessor}{\#endif}}
\DoxyCodeLine{\Hypertarget{stm32f4xx__hal__conf_8h_source_l00490}00490\ }
\DoxyCodeLine{\Hypertarget{stm32f4xx__hal__conf_8h_source_l00491}00491\ \textcolor{preprocessor}{\#endif\ }\textcolor{comment}{/*\ \_\_STM32F4xx\_HAL\_CONF\_H\ */}\textcolor{preprocessor}{}}

\end{DoxyCode}
