TitouanMelon/ENIB_Robot_Mobile_Ros2/docs/latex/stm32f4xx__it_8c_source.tex

\doxysection{stm32f4xx\+\_\+it.\+c}
\hypertarget{stm32f4xx__it_8c_source}{}\label{stm32f4xx__it_8c_source}\index{C:/Users/Administrator/Documents/GitHub/ENIB\_Robot\_Mobile\_Ros2/finalCode/WORKSPACE\_F411\_uROS/base\_robot/Core/Src/stm32f4xx\_it.c@{C:/Users/Administrator/Documents/GitHub/ENIB\_Robot\_Mobile\_Ros2/finalCode/WORKSPACE\_F411\_uROS/base\_robot/Core/Src/stm32f4xx\_it.c}}

\begin{DoxyCode}{0}
\DoxyCodeLine{\Hypertarget{stm32f4xx__it_8c_source_l00001}00001\ }
\DoxyCodeLine{\Hypertarget{stm32f4xx__it_8c_source_l00002}00002\ \textcolor{preprocessor}{\#include\ "{}\mbox{\hyperlink{main_8h}{main.h}}"{}}}
\DoxyCodeLine{\Hypertarget{stm32f4xx__it_8c_source_l00003}00003\ \textcolor{preprocessor}{\#include\ "{}\mbox{\hyperlink{stm32f4xx__it_8h}{stm32f4xx\_it.h}}"{}}}
\DoxyCodeLine{\Hypertarget{stm32f4xx__it_8c_source_l00004}00004\ }
\DoxyCodeLine{\Hypertarget{stm32f4xx__it_8c_source_l00005}00005\ \textcolor{keyword}{extern}\ DMA\_HandleTypeDef\ hdma\_usart1\_rx;}
\DoxyCodeLine{\Hypertarget{stm32f4xx__it_8c_source_l00006}00006\ \textcolor{keyword}{extern}\ DMA\_HandleTypeDef\ hdma\_usart1\_tx;}
\DoxyCodeLine{\Hypertarget{stm32f4xx__it_8c_source_l00007}00007\ \textcolor{keyword}{extern}\ DMA\_HandleTypeDef\ hdma\_usart2\_rx;}
\DoxyCodeLine{\Hypertarget{stm32f4xx__it_8c_source_l00008}00008\ \textcolor{keyword}{extern}\ DMA\_HandleTypeDef\ hdma\_usart2\_tx;}
\DoxyCodeLine{\Hypertarget{stm32f4xx__it_8c_source_l00009}00009\ \textcolor{keyword}{extern}\ UART\_HandleTypeDef\ huart1;}
\DoxyCodeLine{\Hypertarget{stm32f4xx__it_8c_source_l00010}00010\ \textcolor{keyword}{extern}\ UART\_HandleTypeDef\ huart2;}
\DoxyCodeLine{\Hypertarget{stm32f4xx__it_8c_source_l00011}00011\ \textcolor{keyword}{extern}\ TIM\_HandleTypeDef\ htim4;}
\DoxyCodeLine{\Hypertarget{stm32f4xx__it_8c_source_l00012}00012\ \textcolor{keyword}{extern}\ I2C\_HandleTypeDef\ hi2c1;}
\DoxyCodeLine{\Hypertarget{stm32f4xx__it_8c_source_l00013}00013\ }
\DoxyCodeLine{\Hypertarget{stm32f4xx__it_8c_source_l00014}00014\ }
\DoxyCodeLine{\Hypertarget{stm32f4xx__it_8c_source_l00015}00015\ \textcolor{keywordtype}{void}\ NMI\_Handler(\textcolor{keywordtype}{void})}
\DoxyCodeLine{\Hypertarget{stm32f4xx__it_8c_source_l00016}00016\ \{}
\DoxyCodeLine{\Hypertarget{stm32f4xx__it_8c_source_l00017}00017\ \ \ \textcolor{keywordflow}{while}\ (1)}
\DoxyCodeLine{\Hypertarget{stm32f4xx__it_8c_source_l00018}00018\ \ \ \{}
\DoxyCodeLine{\Hypertarget{stm32f4xx__it_8c_source_l00019}00019\ \ \ \}}
\DoxyCodeLine{\Hypertarget{stm32f4xx__it_8c_source_l00020}00020\ \}}
\DoxyCodeLine{\Hypertarget{stm32f4xx__it_8c_source_l00021}00021\ }
\DoxyCodeLine{\Hypertarget{stm32f4xx__it_8c_source_l00022}00022\ \textcolor{keywordtype}{void}\ HardFault\_Handler(\textcolor{keywordtype}{void})}
\DoxyCodeLine{\Hypertarget{stm32f4xx__it_8c_source_l00023}00023\ \{}
\DoxyCodeLine{\Hypertarget{stm32f4xx__it_8c_source_l00024}00024\ }
\DoxyCodeLine{\Hypertarget{stm32f4xx__it_8c_source_l00025}00025\ \ \ \textcolor{keywordflow}{while}\ (1)}
\DoxyCodeLine{\Hypertarget{stm32f4xx__it_8c_source_l00026}00026\ \ \ \{}
\DoxyCodeLine{\Hypertarget{stm32f4xx__it_8c_source_l00027}00027\ \ \ \}}
\DoxyCodeLine{\Hypertarget{stm32f4xx__it_8c_source_l00028}00028\ \}}
\DoxyCodeLine{\Hypertarget{stm32f4xx__it_8c_source_l00029}00029\ }
\DoxyCodeLine{\Hypertarget{stm32f4xx__it_8c_source_l00030}00030\ \textcolor{keywordtype}{void}\ MemManage\_Handler(\textcolor{keywordtype}{void})}
\DoxyCodeLine{\Hypertarget{stm32f4xx__it_8c_source_l00031}00031\ \{}
\DoxyCodeLine{\Hypertarget{stm32f4xx__it_8c_source_l00032}00032\ \ \ \textcolor{keywordflow}{while}\ (1)}
\DoxyCodeLine{\Hypertarget{stm32f4xx__it_8c_source_l00033}00033\ \ \ \{}
\DoxyCodeLine{\Hypertarget{stm32f4xx__it_8c_source_l00034}00034\ \ \ \}}
\DoxyCodeLine{\Hypertarget{stm32f4xx__it_8c_source_l00035}00035\ \}}
\DoxyCodeLine{\Hypertarget{stm32f4xx__it_8c_source_l00036}00036\ }
\DoxyCodeLine{\Hypertarget{stm32f4xx__it_8c_source_l00037}00037\ }
\DoxyCodeLine{\Hypertarget{stm32f4xx__it_8c_source_l00038}00038\ \textcolor{keywordtype}{void}\ BusFault\_Handler(\textcolor{keywordtype}{void})}
\DoxyCodeLine{\Hypertarget{stm32f4xx__it_8c_source_l00039}00039\ \{}
\DoxyCodeLine{\Hypertarget{stm32f4xx__it_8c_source_l00040}00040\ \ \ \textcolor{keywordflow}{while}\ (1)}
\DoxyCodeLine{\Hypertarget{stm32f4xx__it_8c_source_l00041}00041\ \ \ \{}
\DoxyCodeLine{\Hypertarget{stm32f4xx__it_8c_source_l00042}00042\ \ \ \}}
\DoxyCodeLine{\Hypertarget{stm32f4xx__it_8c_source_l00043}00043\ \}}
\DoxyCodeLine{\Hypertarget{stm32f4xx__it_8c_source_l00044}00044\ }
\DoxyCodeLine{\Hypertarget{stm32f4xx__it_8c_source_l00048}\mbox{\hyperlink{stm32f4xx__it_8h_a1d98923de2ed6b7309b66f9ba2971647}{00048}}\ \textcolor{keywordtype}{void}\ \mbox{\hyperlink{stm32f4xx__it_8h_a1d98923de2ed6b7309b66f9ba2971647}{UsageFault\_Handler}}(\textcolor{keywordtype}{void})}
\DoxyCodeLine{\Hypertarget{stm32f4xx__it_8c_source_l00049}00049\ \{}
\DoxyCodeLine{\Hypertarget{stm32f4xx__it_8c_source_l00050}00050\ \ \ \textcolor{keywordflow}{while}\ (1)}
\DoxyCodeLine{\Hypertarget{stm32f4xx__it_8c_source_l00051}00051\ \ \ \{}
\DoxyCodeLine{\Hypertarget{stm32f4xx__it_8c_source_l00052}00052\ \ \ \}}
\DoxyCodeLine{\Hypertarget{stm32f4xx__it_8c_source_l00053}00053\ \}}
\DoxyCodeLine{\Hypertarget{stm32f4xx__it_8c_source_l00054}00054\ }
\DoxyCodeLine{\Hypertarget{stm32f4xx__it_8c_source_l00055}00055\ \textcolor{keywordtype}{void}\ DebugMon\_Handler(\textcolor{keywordtype}{void})}
\DoxyCodeLine{\Hypertarget{stm32f4xx__it_8c_source_l00056}00056\ \{}
\DoxyCodeLine{\Hypertarget{stm32f4xx__it_8c_source_l00057}00057\ \}}
\DoxyCodeLine{\Hypertarget{stm32f4xx__it_8c_source_l00058}00058\ }
\DoxyCodeLine{\Hypertarget{stm32f4xx__it_8c_source_l00059}00059\ \textcolor{comment}{/******************************************************************************/}}
\DoxyCodeLine{\Hypertarget{stm32f4xx__it_8c_source_l00060}00060\ \textcolor{comment}{/*\ STM32F4xx\ Peripheral\ Interrupt\ Handlers\ \ \ \ \ \ \ \ \ \ \ \ \ \ \ \ \ \ \ \ \ \ \ \ \ \ \ \ \ \ \ \ \ \ \ \ */}}
\DoxyCodeLine{\Hypertarget{stm32f4xx__it_8c_source_l00061}00061\ \textcolor{comment}{/*\ Add\ here\ the\ Interrupt\ Handlers\ for\ the\ used\ peripherals.\ \ \ \ \ \ \ \ \ \ \ \ \ \ \ \ \ \ */}}
\DoxyCodeLine{\Hypertarget{stm32f4xx__it_8c_source_l00062}00062\ \textcolor{comment}{/*\ For\ the\ available\ peripheral\ interrupt\ handler\ names,\ \ \ \ \ \ \ \ \ \ \ \ \ \ \ \ \ \ \ \ \ \ */}}
\DoxyCodeLine{\Hypertarget{stm32f4xx__it_8c_source_l00063}00063\ \textcolor{comment}{/*\ please\ refer\ to\ the\ startup\ file\ (startup\_stm32f4xx.s).\ \ \ \ \ \ \ \ \ \ \ \ \ \ \ \ \ \ \ \ */}}
\DoxyCodeLine{\Hypertarget{stm32f4xx__it_8c_source_l00064}00064\ \textcolor{comment}{/******************************************************************************/}}
\DoxyCodeLine{\Hypertarget{stm32f4xx__it_8c_source_l00065}00065\ }
\DoxyCodeLine{\Hypertarget{stm32f4xx__it_8c_source_l00066}00066\ \textcolor{keywordtype}{void}\ DMA1\_Stream5\_IRQHandler(\textcolor{keywordtype}{void})}
\DoxyCodeLine{\Hypertarget{stm32f4xx__it_8c_source_l00067}00067\ \{}
\DoxyCodeLine{\Hypertarget{stm32f4xx__it_8c_source_l00068}00068\ \ \ HAL\_DMA\_IRQHandler(\&hdma\_usart2\_rx);}
\DoxyCodeLine{\Hypertarget{stm32f4xx__it_8c_source_l00069}00069\ \}}
\DoxyCodeLine{\Hypertarget{stm32f4xx__it_8c_source_l00070}00070\ }
\DoxyCodeLine{\Hypertarget{stm32f4xx__it_8c_source_l00071}00071\ }
\DoxyCodeLine{\Hypertarget{stm32f4xx__it_8c_source_l00072}00072\ \textcolor{keywordtype}{void}\ DMA1\_Stream6\_IRQHandler(\textcolor{keywordtype}{void})}
\DoxyCodeLine{\Hypertarget{stm32f4xx__it_8c_source_l00073}00073\ \{}
\DoxyCodeLine{\Hypertarget{stm32f4xx__it_8c_source_l00074}00074\ \ \ HAL\_DMA\_IRQHandler(\&hdma\_usart2\_tx);}
\DoxyCodeLine{\Hypertarget{stm32f4xx__it_8c_source_l00075}00075\ \}}
\DoxyCodeLine{\Hypertarget{stm32f4xx__it_8c_source_l00076}00076\ }
\DoxyCodeLine{\Hypertarget{stm32f4xx__it_8c_source_l00077}00077\ \textcolor{comment}{/*void\ TIM1\_UP\_TIM10\_IRQHandler(void)}}
\DoxyCodeLine{\Hypertarget{stm32f4xx__it_8c_source_l00078}00078\ \textcolor{comment}{\{}}
\DoxyCodeLine{\Hypertarget{stm32f4xx__it_8c_source_l00079}00079\ \textcolor{comment}{\ \ HAL\_TIM\_IRQHandler(\&htim1);}}
\DoxyCodeLine{\Hypertarget{stm32f4xx__it_8c_source_l00080}00080\ \textcolor{comment}{\}*/}}
\DoxyCodeLine{\Hypertarget{stm32f4xx__it_8c_source_l00081}00081\ }
\DoxyCodeLine{\Hypertarget{stm32f4xx__it_8c_source_l00082}00082\ \textcolor{keywordtype}{void}\ TIM4\_IRQHandler(\textcolor{keywordtype}{void})}
\DoxyCodeLine{\Hypertarget{stm32f4xx__it_8c_source_l00083}00083\ \{}
\DoxyCodeLine{\Hypertarget{stm32f4xx__it_8c_source_l00084}00084\ \ \ HAL\_TIM\_IRQHandler(\&htim4);}
\DoxyCodeLine{\Hypertarget{stm32f4xx__it_8c_source_l00085}00085\ \}}
\DoxyCodeLine{\Hypertarget{stm32f4xx__it_8c_source_l00086}00086\ }
\DoxyCodeLine{\Hypertarget{stm32f4xx__it_8c_source_l00087}00087\ \textcolor{keywordtype}{void}\ USART1\_IRQHandler(\textcolor{keywordtype}{void})}
\DoxyCodeLine{\Hypertarget{stm32f4xx__it_8c_source_l00088}00088\ \{}
\DoxyCodeLine{\Hypertarget{stm32f4xx__it_8c_source_l00089}00089\ \ \ HAL\_UART\_IRQHandler(\&huart1);}
\DoxyCodeLine{\Hypertarget{stm32f4xx__it_8c_source_l00090}00090\ \}}
\DoxyCodeLine{\Hypertarget{stm32f4xx__it_8c_source_l00091}00091\ }
\DoxyCodeLine{\Hypertarget{stm32f4xx__it_8c_source_l00092}00092\ \textcolor{keywordtype}{void}\ USART2\_IRQHandler(\textcolor{keywordtype}{void})}
\DoxyCodeLine{\Hypertarget{stm32f4xx__it_8c_source_l00093}00093\ \{}
\DoxyCodeLine{\Hypertarget{stm32f4xx__it_8c_source_l00094}00094\ \ \ HAL\_UART\_IRQHandler(\&huart2);}
\DoxyCodeLine{\Hypertarget{stm32f4xx__it_8c_source_l00095}00095\ \}}
\DoxyCodeLine{\Hypertarget{stm32f4xx__it_8c_source_l00096}00096\ }
\DoxyCodeLine{\Hypertarget{stm32f4xx__it_8c_source_l00097}00097\ \textcolor{keywordtype}{void}\ DMA2\_Stream2\_IRQHandler(\textcolor{keywordtype}{void})}
\DoxyCodeLine{\Hypertarget{stm32f4xx__it_8c_source_l00098}00098\ \{}
\DoxyCodeLine{\Hypertarget{stm32f4xx__it_8c_source_l00099}00099\ \ \ HAL\_DMA\_IRQHandler(\&hdma\_usart1\_rx);}
\DoxyCodeLine{\Hypertarget{stm32f4xx__it_8c_source_l00100}00100\ \}}
\DoxyCodeLine{\Hypertarget{stm32f4xx__it_8c_source_l00101}00101\ }
\DoxyCodeLine{\Hypertarget{stm32f4xx__it_8c_source_l00102}00102\ \textcolor{keywordtype}{void}\ DMA2\_Stream7\_IRQHandler(\textcolor{keywordtype}{void})}
\DoxyCodeLine{\Hypertarget{stm32f4xx__it_8c_source_l00103}00103\ \{}
\DoxyCodeLine{\Hypertarget{stm32f4xx__it_8c_source_l00104}00104\ \ \ HAL\_DMA\_IRQHandler(\&hdma\_usart1\_tx);}
\DoxyCodeLine{\Hypertarget{stm32f4xx__it_8c_source_l00105}00105\ \}}
\DoxyCodeLine{\Hypertarget{stm32f4xx__it_8c_source_l00106}00106\ }
\DoxyCodeLine{\Hypertarget{stm32f4xx__it_8c_source_l00107}00107\ }
\DoxyCodeLine{\Hypertarget{stm32f4xx__it_8c_source_l00108}00108\ }
\DoxyCodeLine{\Hypertarget{stm32f4xx__it_8c_source_l00109}00109\ }
\DoxyCodeLine{\Hypertarget{stm32f4xx__it_8c_source_l00110}00110\ \textcolor{comment}{//=======================================================}}
\DoxyCodeLine{\Hypertarget{stm32f4xx__it_8c_source_l00111}00111\ \textcolor{comment}{//\ \ \ \ \ \ ENCODER\ INDEX\ LEFT}}
\DoxyCodeLine{\Hypertarget{stm32f4xx__it_8c_source_l00112}00112\ \textcolor{comment}{//=======================================================}}
\DoxyCodeLine{\Hypertarget{stm32f4xx__it_8c_source_l00113}00113\ \textcolor{keywordtype}{void}\ EXTI15\_10\_IRQHandler(\textcolor{keywordtype}{void})}
\DoxyCodeLine{\Hypertarget{stm32f4xx__it_8c_source_l00114}00114\ \{}
\DoxyCodeLine{\Hypertarget{stm32f4xx__it_8c_source_l00115}00115\ \ \ HAL\_GPIO\_EXTI\_IRQHandler(GPIO\_PIN\_10);}
\DoxyCodeLine{\Hypertarget{stm32f4xx__it_8c_source_l00116}00116\ \}}
\DoxyCodeLine{\Hypertarget{stm32f4xx__it_8c_source_l00117}00117\ \textcolor{comment}{//=======================================================}}
\DoxyCodeLine{\Hypertarget{stm32f4xx__it_8c_source_l00118}00118\ \textcolor{comment}{//\ \ \ \ \ \ ENCODER\ INDEX\ RIGHT}}
\DoxyCodeLine{\Hypertarget{stm32f4xx__it_8c_source_l00119}00119\ \textcolor{comment}{//=======================================================}}
\DoxyCodeLine{\Hypertarget{stm32f4xx__it_8c_source_l00120}00120\ }
\DoxyCodeLine{\Hypertarget{stm32f4xx__it_8c_source_l00121}00121\ \textcolor{keywordtype}{void}\ EXTI0\_IRQHandler(\textcolor{keywordtype}{void})}
\DoxyCodeLine{\Hypertarget{stm32f4xx__it_8c_source_l00122}00122\ \{}
\DoxyCodeLine{\Hypertarget{stm32f4xx__it_8c_source_l00123}00123\ \ \ HAL\_GPIO\_EXTI\_IRQHandler(GPIO\_PIN\_0);}
\DoxyCodeLine{\Hypertarget{stm32f4xx__it_8c_source_l00124}00124\ \}}
\DoxyCodeLine{\Hypertarget{stm32f4xx__it_8c_source_l00125}00125\ }
\DoxyCodeLine{\Hypertarget{stm32f4xx__it_8c_source_l00126}00126\ }
\DoxyCodeLine{\Hypertarget{stm32f4xx__it_8c_source_l00127}00127\ \textcolor{keywordtype}{void}\ I2C1\_EV\_IRQHandler(\textcolor{keywordtype}{void})}
\DoxyCodeLine{\Hypertarget{stm32f4xx__it_8c_source_l00128}00128\ \{}
\DoxyCodeLine{\Hypertarget{stm32f4xx__it_8c_source_l00129}00129\ \ \ \ \ \ \ HAL\_I2C\_EV\_IRQHandler(\&hi2c1);}
\DoxyCodeLine{\Hypertarget{stm32f4xx__it_8c_source_l00130}00130\ \}}
\DoxyCodeLine{\Hypertarget{stm32f4xx__it_8c_source_l00131}00131\ }
\DoxyCodeLine{\Hypertarget{stm32f4xx__it_8c_source_l00132}00132\ \textcolor{keywordtype}{void}\ I2C1\_ER\_IRQHandler(\textcolor{keywordtype}{void})}
\DoxyCodeLine{\Hypertarget{stm32f4xx__it_8c_source_l00133}00133\ \{}
\DoxyCodeLine{\Hypertarget{stm32f4xx__it_8c_source_l00134}00134\ \ \ \ \ \ \ HAL\_I2C\_ER\_IRQHandler(\&hi2c1);}
\DoxyCodeLine{\Hypertarget{stm32f4xx__it_8c_source_l00135}00135\ \}}
\DoxyCodeLine{\Hypertarget{stm32f4xx__it_8c_source_l00136}00136\ }

\end{DoxyCode}
