TitouanMelon/ENIB_Robot_Mobile_Ros2/docs/latex/stm32f4xx__it_8h.tex

\doxysection{C\+:/\+Users/\+Administrator/\+Documents/\+Git\+Hub/\+ENIB\+\_\+\+Robot\+\_\+\+Mobile\+\_\+\+Ros2/final\+Code/\+WORKSPACE\+\_\+\+F411\+\_\+u\+ROS/base\+\_\+robot/\+Core/\+Inc/stm32f4xx\+\_\+it.h File Reference}
\hypertarget{stm32f4xx__it_8h}{}\label{stm32f4xx__it_8h}\index{C:/Users/Administrator/Documents/GitHub/ENIB\_Robot\_Mobile\_Ros2/finalCode/WORKSPACE\_F411\_uROS/base\_robot/Core/Inc/stm32f4xx\_it.h@{C:/Users/Administrator/Documents/GitHub/ENIB\_Robot\_Mobile\_Ros2/finalCode/WORKSPACE\_F411\_uROS/base\_robot/Core/Inc/stm32f4xx\_it.h}}

This file contains the headers of the interrupt handlers.  

\doxysubsubsection*{Functions}
\begin{DoxyCompactItemize}
\item 
void \mbox{\hyperlink{stm32f4xx__it_8h_a6ad7a5e3ee69cb6db6a6b9111ba898bc}{NMI\+\_\+\+Handler}} (void)
\item 
void \mbox{\hyperlink{stm32f4xx__it_8h_a2bffc10d5bd4106753b7c30e86903bea}{Hard\+Fault\+\_\+\+Handler}} (void)
\item 
void \mbox{\hyperlink{stm32f4xx__it_8h_a3150f74512510287a942624aa9b44cc5}{Mem\+Manage\+\_\+\+Handler}} (void)
\item 
void \mbox{\hyperlink{stm32f4xx__it_8h_a850cefb17a977292ae5eb4cafa9976c3}{Bus\+Fault\+\_\+\+Handler}} (void)
\item 
void \mbox{\hyperlink{stm32f4xx__it_8h_a1d98923de2ed6b7309b66f9ba2971647}{Usage\+Fault\+\_\+\+Handler}} (void)
\begin{DoxyCompactList}\small\item\em This function handles Undefined instruction or illegal state. \end{DoxyCompactList}\item 
void \mbox{\hyperlink{stm32f4xx__it_8h_adbdfb05858cc36fc520974df37ec3cb0}{Debug\+Mon\+\_\+\+Handler}} (void)
\item 
void \mbox{\hyperlink{stm32f4xx__it_8h_ac201b60d58b0eba2ce0b55710eb3c4d0}{DMA1\+\_\+\+Stream5\+\_\+\+IRQHandler}} (void)
\item 
void \mbox{\hyperlink{stm32f4xx__it_8h_aa28fd448462a6347589129f63bb0a388}{DMA1\+\_\+\+Stream6\+\_\+\+IRQHandler}} (void)
\item 
\Hypertarget{stm32f4xx__it_8h_ad1fd361bc5ad89facee67c76d1ff8dc0}\label{stm32f4xx__it_8h_ad1fd361bc5ad89facee67c76d1ff8dc0} 
void {\bfseries TIM1\+\_\+\+UP\+\_\+\+TIM10\+\_\+\+IRQHandler} (void)
\item 
void \mbox{\hyperlink{stm32f4xx__it_8h_a7139cd4baabbbcbab0c1fe6d7d4ae1cc}{USART1\+\_\+\+IRQHandler}} (void)
\item 
void \mbox{\hyperlink{stm32f4xx__it_8h_a0ca6fd0e6f77921dd1123539857ba0a8}{USART2\+\_\+\+IRQHandler}} (void)
\item 
void \mbox{\hyperlink{stm32f4xx__it_8h_a7e367d7c7b74485c4c75cdef30ad01e1}{DMA2\+\_\+\+Stream2\+\_\+\+IRQHandler}} (void)
\item 
void \mbox{\hyperlink{stm32f4xx__it_8h_afc1d00127dcf2fb0afdbc50e4b587fdf}{DMA2\+\_\+\+Stream7\+\_\+\+IRQHandler}} (void)
\end{DoxyCompactItemize}

\doxysubsection{Detailed Description}
This file contains the headers of the interrupt handlers. 

\begin{DoxyAttention}{Attention}

\end{DoxyAttention}
Copyright (c) 2022 STMicroelectronics. All rights reserved.

This software is licensed under terms that can be found in the LICENSE file in the root directory of this software component. If no LICENSE file comes with this software, it is provided AS-\/\+IS. 

Definition in file \mbox{\hyperlink{stm32f4xx__it_8h_source}{stm32f4xx\+\_\+it.\+h}}.

\doxysubsection{Function Documentation}
\Hypertarget{stm32f4xx__it_8h_a850cefb17a977292ae5eb4cafa9976c3}\label{stm32f4xx__it_8h_a850cefb17a977292ae5eb4cafa9976c3} 
\index{stm32f4xx\_it.h@{stm32f4xx\_it.h}!BusFault\_Handler@{BusFault\_Handler}}
\index{BusFault\_Handler@{BusFault\_Handler}!stm32f4xx\_it.h@{stm32f4xx\_it.h}}
\doxysubsubsection{\texorpdfstring{BusFault\_Handler()}{BusFault\_Handler()}}
{\footnotesize\ttfamily void Bus\+Fault\+\_\+\+Handler (\begin{DoxyParamCaption}\item[{void}]{ }\end{DoxyParamCaption})}

Definition at line \mbox{\hyperlink{stm32f4xx__it_8c_source_l00038}{38}} of file \mbox{\hyperlink{stm32f4xx__it_8c_source}{stm32f4xx\+\_\+it.\+c}}.

\Hypertarget{stm32f4xx__it_8h_adbdfb05858cc36fc520974df37ec3cb0}\label{stm32f4xx__it_8h_adbdfb05858cc36fc520974df37ec3cb0} 
\index{stm32f4xx\_it.h@{stm32f4xx\_it.h}!DebugMon\_Handler@{DebugMon\_Handler}}
\index{DebugMon\_Handler@{DebugMon\_Handler}!stm32f4xx\_it.h@{stm32f4xx\_it.h}}
\doxysubsubsection{\texorpdfstring{DebugMon\_Handler()}{DebugMon\_Handler()}}
{\footnotesize\ttfamily void Debug\+Mon\+\_\+\+Handler (\begin{DoxyParamCaption}\item[{void}]{ }\end{DoxyParamCaption})}

Definition at line \mbox{\hyperlink{stm32f4xx__it_8c_source_l00055}{55}} of file \mbox{\hyperlink{stm32f4xx__it_8c_source}{stm32f4xx\+\_\+it.\+c}}.

\Hypertarget{stm32f4xx__it_8h_ac201b60d58b0eba2ce0b55710eb3c4d0}\label{stm32f4xx__it_8h_ac201b60d58b0eba2ce0b55710eb3c4d0} 
\index{stm32f4xx\_it.h@{stm32f4xx\_it.h}!DMA1\_Stream5\_IRQHandler@{DMA1\_Stream5\_IRQHandler}}
\index{DMA1\_Stream5\_IRQHandler@{DMA1\_Stream5\_IRQHandler}!stm32f4xx\_it.h@{stm32f4xx\_it.h}}
\doxysubsubsection{\texorpdfstring{DMA1\_Stream5\_IRQHandler()}{DMA1\_Stream5\_IRQHandler()}}
{\footnotesize\ttfamily void DMA1\+\_\+\+Stream5\+\_\+\+IRQHandler (\begin{DoxyParamCaption}\item[{void}]{ }\end{DoxyParamCaption})}

Definition at line \mbox{\hyperlink{stm32f4xx__it_8c_source_l00066}{66}} of file \mbox{\hyperlink{stm32f4xx__it_8c_source}{stm32f4xx\+\_\+it.\+c}}.

\Hypertarget{stm32f4xx__it_8h_aa28fd448462a6347589129f63bb0a388}\label{stm32f4xx__it_8h_aa28fd448462a6347589129f63bb0a388} 
\index{stm32f4xx\_it.h@{stm32f4xx\_it.h}!DMA1\_Stream6\_IRQHandler@{DMA1\_Stream6\_IRQHandler}}
\index{DMA1\_Stream6\_IRQHandler@{DMA1\_Stream6\_IRQHandler}!stm32f4xx\_it.h@{stm32f4xx\_it.h}}
\doxysubsubsection{\texorpdfstring{DMA1\_Stream6\_IRQHandler()}{DMA1\_Stream6\_IRQHandler()}}
{\footnotesize\ttfamily void DMA1\+\_\+\+Stream6\+\_\+\+IRQHandler (\begin{DoxyParamCaption}\item[{void}]{ }\end{DoxyParamCaption})}

Definition at line \mbox{\hyperlink{stm32f4xx__it_8c_source_l00072}{72}} of file \mbox{\hyperlink{stm32f4xx__it_8c_source}{stm32f4xx\+\_\+it.\+c}}.

\Hypertarget{stm32f4xx__it_8h_a7e367d7c7b74485c4c75cdef30ad01e1}\label{stm32f4xx__it_8h_a7e367d7c7b74485c4c75cdef30ad01e1} 
\index{stm32f4xx\_it.h@{stm32f4xx\_it.h}!DMA2\_Stream2\_IRQHandler@{DMA2\_Stream2\_IRQHandler}}
\index{DMA2\_Stream2\_IRQHandler@{DMA2\_Stream2\_IRQHandler}!stm32f4xx\_it.h@{stm32f4xx\_it.h}}
\doxysubsubsection{\texorpdfstring{DMA2\_Stream2\_IRQHandler()}{DMA2\_Stream2\_IRQHandler()}}
{\footnotesize\ttfamily void DMA2\+\_\+\+Stream2\+\_\+\+IRQHandler (\begin{DoxyParamCaption}\item[{void}]{ }\end{DoxyParamCaption})}

Definition at line \mbox{\hyperlink{stm32f4xx__it_8c_source_l00097}{97}} of file \mbox{\hyperlink{stm32f4xx__it_8c_source}{stm32f4xx\+\_\+it.\+c}}.

\Hypertarget{stm32f4xx__it_8h_afc1d00127dcf2fb0afdbc50e4b587fdf}\label{stm32f4xx__it_8h_afc1d00127dcf2fb0afdbc50e4b587fdf} 
\index{stm32f4xx\_it.h@{stm32f4xx\_it.h}!DMA2\_Stream7\_IRQHandler@{DMA2\_Stream7\_IRQHandler}}
\index{DMA2\_Stream7\_IRQHandler@{DMA2\_Stream7\_IRQHandler}!stm32f4xx\_it.h@{stm32f4xx\_it.h}}
\doxysubsubsection{\texorpdfstring{DMA2\_Stream7\_IRQHandler()}{DMA2\_Stream7\_IRQHandler()}}
{\footnotesize\ttfamily void DMA2\+\_\+\+Stream7\+\_\+\+IRQHandler (\begin{DoxyParamCaption}\item[{void}]{ }\end{DoxyParamCaption})}

Definition at line \mbox{\hyperlink{stm32f4xx__it_8c_source_l00102}{102}} of file \mbox{\hyperlink{stm32f4xx__it_8c_source}{stm32f4xx\+\_\+it.\+c}}.

\Hypertarget{stm32f4xx__it_8h_a2bffc10d5bd4106753b7c30e86903bea}\label{stm32f4xx__it_8h_a2bffc10d5bd4106753b7c30e86903bea} 
\index{stm32f4xx\_it.h@{stm32f4xx\_it.h}!HardFault\_Handler@{HardFault\_Handler}}
\index{HardFault\_Handler@{HardFault\_Handler}!stm32f4xx\_it.h@{stm32f4xx\_it.h}}
\doxysubsubsection{\texorpdfstring{HardFault\_Handler()}{HardFault\_Handler()}}
{\footnotesize\ttfamily void Hard\+Fault\+\_\+\+Handler (\begin{DoxyParamCaption}\item[{void}]{ }\end{DoxyParamCaption})}

Definition at line \mbox{\hyperlink{stm32f4xx__it_8c_source_l00022}{22}} of file \mbox{\hyperlink{stm32f4xx__it_8c_source}{stm32f4xx\+\_\+it.\+c}}.

\Hypertarget{stm32f4xx__it_8h_a3150f74512510287a942624aa9b44cc5}\label{stm32f4xx__it_8h_a3150f74512510287a942624aa9b44cc5} 
\index{stm32f4xx\_it.h@{stm32f4xx\_it.h}!MemManage\_Handler@{MemManage\_Handler}}
\index{MemManage\_Handler@{MemManage\_Handler}!stm32f4xx\_it.h@{stm32f4xx\_it.h}}
\doxysubsubsection{\texorpdfstring{MemManage\_Handler()}{MemManage\_Handler()}}
{\footnotesize\ttfamily void Mem\+Manage\+\_\+\+Handler (\begin{DoxyParamCaption}\item[{void}]{ }\end{DoxyParamCaption})}

Definition at line \mbox{\hyperlink{stm32f4xx__it_8c_source_l00030}{30}} of file \mbox{\hyperlink{stm32f4xx__it_8c_source}{stm32f4xx\+\_\+it.\+c}}.

\Hypertarget{stm32f4xx__it_8h_a6ad7a5e3ee69cb6db6a6b9111ba898bc}\label{stm32f4xx__it_8h_a6ad7a5e3ee69cb6db6a6b9111ba898bc} 
\index{stm32f4xx\_it.h@{stm32f4xx\_it.h}!NMI\_Handler@{NMI\_Handler}}
\index{NMI\_Handler@{NMI\_Handler}!stm32f4xx\_it.h@{stm32f4xx\_it.h}}
\doxysubsubsection{\texorpdfstring{NMI\_Handler()}{NMI\_Handler()}}
{\footnotesize\ttfamily void NMI\+\_\+\+Handler (\begin{DoxyParamCaption}\item[{void}]{ }\end{DoxyParamCaption})}

Definition at line \mbox{\hyperlink{stm32f4xx__it_8c_source_l00015}{15}} of file \mbox{\hyperlink{stm32f4xx__it_8c_source}{stm32f4xx\+\_\+it.\+c}}.

\Hypertarget{stm32f4xx__it_8h_a1d98923de2ed6b7309b66f9ba2971647}\label{stm32f4xx__it_8h_a1d98923de2ed6b7309b66f9ba2971647} 
\index{stm32f4xx\_it.h@{stm32f4xx\_it.h}!UsageFault\_Handler@{UsageFault\_Handler}}
\index{UsageFault\_Handler@{UsageFault\_Handler}!stm32f4xx\_it.h@{stm32f4xx\_it.h}}
\doxysubsubsection{\texorpdfstring{UsageFault\_Handler()}{UsageFault\_Handler()}}
{\footnotesize\ttfamily void Usage\+Fault\+\_\+\+Handler (\begin{DoxyParamCaption}\item[{void}]{ }\end{DoxyParamCaption})}

This function handles Undefined instruction or illegal state. 

Definition at line \mbox{\hyperlink{stm32f4xx__it_8c_source_l00048}{48}} of file \mbox{\hyperlink{stm32f4xx__it_8c_source}{stm32f4xx\+\_\+it.\+c}}.

\Hypertarget{stm32f4xx__it_8h_a7139cd4baabbbcbab0c1fe6d7d4ae1cc}\label{stm32f4xx__it_8h_a7139cd4baabbbcbab0c1fe6d7d4ae1cc} 
\index{stm32f4xx\_it.h@{stm32f4xx\_it.h}!USART1\_IRQHandler@{USART1\_IRQHandler}}
\index{USART1\_IRQHandler@{USART1\_IRQHandler}!stm32f4xx\_it.h@{stm32f4xx\_it.h}}
\doxysubsubsection{\texorpdfstring{USART1\_IRQHandler()}{USART1\_IRQHandler()}}
{\footnotesize\ttfamily void USART1\+\_\+\+IRQHandler (\begin{DoxyParamCaption}\item[{void}]{ }\end{DoxyParamCaption})}

Definition at line \mbox{\hyperlink{stm32f4xx__it_8c_source_l00087}{87}} of file \mbox{\hyperlink{stm32f4xx__it_8c_source}{stm32f4xx\+\_\+it.\+c}}.

\Hypertarget{stm32f4xx__it_8h_a0ca6fd0e6f77921dd1123539857ba0a8}\label{stm32f4xx__it_8h_a0ca6fd0e6f77921dd1123539857ba0a8} 
\index{stm32f4xx\_it.h@{stm32f4xx\_it.h}!USART2\_IRQHandler@{USART2\_IRQHandler}}
\index{USART2\_IRQHandler@{USART2\_IRQHandler}!stm32f4xx\_it.h@{stm32f4xx\_it.h}}
\doxysubsubsection{\texorpdfstring{USART2\_IRQHandler()}{USART2\_IRQHandler()}}
{\footnotesize\ttfamily void USART2\+\_\+\+IRQHandler (\begin{DoxyParamCaption}\item[{void}]{ }\end{DoxyParamCaption})}

Definition at line \mbox{\hyperlink{stm32f4xx__it_8c_source_l00092}{92}} of file \mbox{\hyperlink{stm32f4xx__it_8c_source}{stm32f4xx\+\_\+it.\+c}}.
