TitouanMelon/ENIB_Robot_Mobile_Ros2/docs/latex/stm32f4xx__it_8h_source.tex

\doxysection{stm32f4xx\+\_\+it.\+h}
\hypertarget{stm32f4xx__it_8h_source}{}\label{stm32f4xx__it_8h_source}\index{C:/Users/Administrator/Documents/GitHub/ENIB\_Robot\_Mobile\_Ros2/finalCode/WORKSPACE\_F411\_uROS/base\_robot/Core/Inc/stm32f4xx\_it.h@{C:/Users/Administrator/Documents/GitHub/ENIB\_Robot\_Mobile\_Ros2/finalCode/WORKSPACE\_F411\_uROS/base\_robot/Core/Inc/stm32f4xx\_it.h}}
\mbox{\hyperlink{stm32f4xx__it_8h}{Go to the documentation of this file.}}
\begin{DoxyCode}{0}
\DoxyCodeLine{\Hypertarget{stm32f4xx__it_8h_source_l00001}00001\ \textcolor{comment}{/*\ USER\ CODE\ BEGIN\ Header\ */}}
\DoxyCodeLine{\Hypertarget{stm32f4xx__it_8h_source_l00018}00018\ \textcolor{comment}{/*\ USER\ CODE\ END\ Header\ */}}
\DoxyCodeLine{\Hypertarget{stm32f4xx__it_8h_source_l00019}00019\ }
\DoxyCodeLine{\Hypertarget{stm32f4xx__it_8h_source_l00020}00020\ \textcolor{comment}{/*\ Define\ to\ prevent\ recursive\ inclusion\ -\/-\/-\/-\/-\/-\/-\/-\/-\/-\/-\/-\/-\/-\/-\/-\/-\/-\/-\/-\/-\/-\/-\/-\/-\/-\/-\/-\/-\/-\/-\/-\/-\/-\/-\/-\/-\/*/}}
\DoxyCodeLine{\Hypertarget{stm32f4xx__it_8h_source_l00021}00021\ \textcolor{preprocessor}{\#ifndef\ \_\_STM32F4xx\_IT\_H}}
\DoxyCodeLine{\Hypertarget{stm32f4xx__it_8h_source_l00022}00022\ \textcolor{preprocessor}{\#define\ \_\_STM32F4xx\_IT\_H}}
\DoxyCodeLine{\Hypertarget{stm32f4xx__it_8h_source_l00023}00023\ }
\DoxyCodeLine{\Hypertarget{stm32f4xx__it_8h_source_l00024}00024\ \textcolor{preprocessor}{\#ifdef\ \_\_cplusplus}}
\DoxyCodeLine{\Hypertarget{stm32f4xx__it_8h_source_l00025}00025\ \ \textcolor{keyword}{extern}\ \textcolor{stringliteral}{"{}C"{}}\ \{}
\DoxyCodeLine{\Hypertarget{stm32f4xx__it_8h_source_l00026}00026\ \textcolor{preprocessor}{\#endif}}
\DoxyCodeLine{\Hypertarget{stm32f4xx__it_8h_source_l00027}00027\ }
\DoxyCodeLine{\Hypertarget{stm32f4xx__it_8h_source_l00028}00028\ \textcolor{comment}{/*\ Private\ includes\ -\/-\/-\/-\/-\/-\/-\/-\/-\/-\/-\/-\/-\/-\/-\/-\/-\/-\/-\/-\/-\/-\/-\/-\/-\/-\/-\/-\/-\/-\/-\/-\/-\/-\/-\/-\/-\/-\/-\/-\/-\/-\/-\/-\/-\/-\/-\/-\/-\/-\/-\/-\/-\/-\/-\/-\/-\/-\/*/}}
\DoxyCodeLine{\Hypertarget{stm32f4xx__it_8h_source_l00029}00029\ \textcolor{comment}{/*\ USER\ CODE\ BEGIN\ Includes\ */}}
\DoxyCodeLine{\Hypertarget{stm32f4xx__it_8h_source_l00030}00030\ }
\DoxyCodeLine{\Hypertarget{stm32f4xx__it_8h_source_l00031}00031\ \textcolor{comment}{/*\ USER\ CODE\ END\ Includes\ */}}
\DoxyCodeLine{\Hypertarget{stm32f4xx__it_8h_source_l00032}00032\ }
\DoxyCodeLine{\Hypertarget{stm32f4xx__it_8h_source_l00033}00033\ \textcolor{comment}{/*\ Exported\ types\ -\/-\/-\/-\/-\/-\/-\/-\/-\/-\/-\/-\/-\/-\/-\/-\/-\/-\/-\/-\/-\/-\/-\/-\/-\/-\/-\/-\/-\/-\/-\/-\/-\/-\/-\/-\/-\/-\/-\/-\/-\/-\/-\/-\/-\/-\/-\/-\/-\/-\/-\/-\/-\/-\/-\/-\/-\/-\/-\/-\/*/}}
\DoxyCodeLine{\Hypertarget{stm32f4xx__it_8h_source_l00034}00034\ \textcolor{comment}{/*\ USER\ CODE\ BEGIN\ ET\ */}}
\DoxyCodeLine{\Hypertarget{stm32f4xx__it_8h_source_l00035}00035\ }
\DoxyCodeLine{\Hypertarget{stm32f4xx__it_8h_source_l00036}00036\ \textcolor{comment}{/*\ USER\ CODE\ END\ ET\ */}}
\DoxyCodeLine{\Hypertarget{stm32f4xx__it_8h_source_l00037}00037\ }
\DoxyCodeLine{\Hypertarget{stm32f4xx__it_8h_source_l00038}00038\ \textcolor{comment}{/*\ Exported\ constants\ -\/-\/-\/-\/-\/-\/-\/-\/-\/-\/-\/-\/-\/-\/-\/-\/-\/-\/-\/-\/-\/-\/-\/-\/-\/-\/-\/-\/-\/-\/-\/-\/-\/-\/-\/-\/-\/-\/-\/-\/-\/-\/-\/-\/-\/-\/-\/-\/-\/-\/-\/-\/-\/-\/-\/-\/*/}}
\DoxyCodeLine{\Hypertarget{stm32f4xx__it_8h_source_l00039}00039\ \textcolor{comment}{/*\ USER\ CODE\ BEGIN\ EC\ */}}
\DoxyCodeLine{\Hypertarget{stm32f4xx__it_8h_source_l00040}00040\ }
\DoxyCodeLine{\Hypertarget{stm32f4xx__it_8h_source_l00041}00041\ \textcolor{comment}{/*\ USER\ CODE\ END\ EC\ */}}
\DoxyCodeLine{\Hypertarget{stm32f4xx__it_8h_source_l00042}00042\ }
\DoxyCodeLine{\Hypertarget{stm32f4xx__it_8h_source_l00043}00043\ \textcolor{comment}{/*\ Exported\ macro\ -\/-\/-\/-\/-\/-\/-\/-\/-\/-\/-\/-\/-\/-\/-\/-\/-\/-\/-\/-\/-\/-\/-\/-\/-\/-\/-\/-\/-\/-\/-\/-\/-\/-\/-\/-\/-\/-\/-\/-\/-\/-\/-\/-\/-\/-\/-\/-\/-\/-\/-\/-\/-\/-\/-\/-\/-\/-\/-\/-\/*/}}
\DoxyCodeLine{\Hypertarget{stm32f4xx__it_8h_source_l00044}00044\ \textcolor{comment}{/*\ USER\ CODE\ BEGIN\ EM\ */}}
\DoxyCodeLine{\Hypertarget{stm32f4xx__it_8h_source_l00045}00045\ }
\DoxyCodeLine{\Hypertarget{stm32f4xx__it_8h_source_l00046}00046\ \textcolor{comment}{/*\ USER\ CODE\ END\ EM\ */}}
\DoxyCodeLine{\Hypertarget{stm32f4xx__it_8h_source_l00047}00047\ }
\DoxyCodeLine{\Hypertarget{stm32f4xx__it_8h_source_l00048}00048\ \textcolor{comment}{/*\ Exported\ functions\ prototypes\ -\/-\/-\/-\/-\/-\/-\/-\/-\/-\/-\/-\/-\/-\/-\/-\/-\/-\/-\/-\/-\/-\/-\/-\/-\/-\/-\/-\/-\/-\/-\/-\/-\/-\/-\/-\/-\/-\/-\/-\/-\/-\/-\/-\/-\/*/}}
\DoxyCodeLine{\Hypertarget{stm32f4xx__it_8h_source_l00049}00049\ \textcolor{keywordtype}{void}\ NMI\_Handler(\textcolor{keywordtype}{void});}
\DoxyCodeLine{\Hypertarget{stm32f4xx__it_8h_source_l00050}00050\ \textcolor{keywordtype}{void}\ HardFault\_Handler(\textcolor{keywordtype}{void});}
\DoxyCodeLine{\Hypertarget{stm32f4xx__it_8h_source_l00051}00051\ \textcolor{keywordtype}{void}\ MemManage\_Handler(\textcolor{keywordtype}{void});}
\DoxyCodeLine{\Hypertarget{stm32f4xx__it_8h_source_l00052}00052\ \textcolor{keywordtype}{void}\ BusFault\_Handler(\textcolor{keywordtype}{void});}
\DoxyCodeLine{\Hypertarget{stm32f4xx__it_8h_source_l00053}00053\ \textcolor{keywordtype}{void}\ \mbox{\hyperlink{stm32f4xx__it_8h_a1d98923de2ed6b7309b66f9ba2971647}{UsageFault\_Handler}}(\textcolor{keywordtype}{void});}
\DoxyCodeLine{\Hypertarget{stm32f4xx__it_8h_source_l00054}00054\ \textcolor{keywordtype}{void}\ DebugMon\_Handler(\textcolor{keywordtype}{void});}
\DoxyCodeLine{\Hypertarget{stm32f4xx__it_8h_source_l00055}00055\ \textcolor{keywordtype}{void}\ DMA1\_Stream5\_IRQHandler(\textcolor{keywordtype}{void});}
\DoxyCodeLine{\Hypertarget{stm32f4xx__it_8h_source_l00056}00056\ \textcolor{keywordtype}{void}\ DMA1\_Stream6\_IRQHandler(\textcolor{keywordtype}{void});}
\DoxyCodeLine{\Hypertarget{stm32f4xx__it_8h_source_l00057}00057\ \textcolor{keywordtype}{void}\ TIM1\_UP\_TIM10\_IRQHandler(\textcolor{keywordtype}{void});}
\DoxyCodeLine{\Hypertarget{stm32f4xx__it_8h_source_l00058}00058\ \textcolor{keywordtype}{void}\ USART1\_IRQHandler(\textcolor{keywordtype}{void});}
\DoxyCodeLine{\Hypertarget{stm32f4xx__it_8h_source_l00059}00059\ \textcolor{keywordtype}{void}\ USART2\_IRQHandler(\textcolor{keywordtype}{void});}
\DoxyCodeLine{\Hypertarget{stm32f4xx__it_8h_source_l00060}00060\ \textcolor{keywordtype}{void}\ DMA2\_Stream2\_IRQHandler(\textcolor{keywordtype}{void});}
\DoxyCodeLine{\Hypertarget{stm32f4xx__it_8h_source_l00061}00061\ \textcolor{keywordtype}{void}\ DMA2\_Stream7\_IRQHandler(\textcolor{keywordtype}{void});}
\DoxyCodeLine{\Hypertarget{stm32f4xx__it_8h_source_l00062}00062\ \textcolor{comment}{/*\ USER\ CODE\ BEGIN\ EFP\ */}}
\DoxyCodeLine{\Hypertarget{stm32f4xx__it_8h_source_l00063}00063\ }
\DoxyCodeLine{\Hypertarget{stm32f4xx__it_8h_source_l00064}00064\ \textcolor{comment}{/*\ USER\ CODE\ END\ EFP\ */}}
\DoxyCodeLine{\Hypertarget{stm32f4xx__it_8h_source_l00065}00065\ }
\DoxyCodeLine{\Hypertarget{stm32f4xx__it_8h_source_l00066}00066\ \textcolor{preprocessor}{\#ifdef\ \_\_cplusplus}}
\DoxyCodeLine{\Hypertarget{stm32f4xx__it_8h_source_l00067}00067\ \}}
\DoxyCodeLine{\Hypertarget{stm32f4xx__it_8h_source_l00068}00068\ \textcolor{preprocessor}{\#endif}}
\DoxyCodeLine{\Hypertarget{stm32f4xx__it_8h_source_l00069}00069\ }
\DoxyCodeLine{\Hypertarget{stm32f4xx__it_8h_source_l00070}00070\ \textcolor{preprocessor}{\#endif\ }\textcolor{comment}{/*\ \_\_STM32F4xx\_IT\_H\ */}\textcolor{preprocessor}{}}

\end{DoxyCode}
