TitouanMelon/ENIB_Robot_Mobile_Ros2/report/Liste matériel.docx

Liste matériel

Nom | Quantité | Prix unitaire | Commentaire
PC | 1
Raspberry PI 4 (8GO) | 1
STM32 F411 | 1
Robot | 1
Webcam | 1
Routeur WIFI | 1
radiateur (pour RPI) | 1
Carte SD 32GO | 1
Adaptateur SD USB | 1
Adaptateur hdmi vers micro-hdmi | 1
