TitouanMelon/ENIB_Robot_Mobile_Ros2/report/README.md

# Vidéo de présentation du projet
- Avec explications pour le module PER : https://youtu.be/u2DFrZgYV7c
- Démonstrations seulement pour le module ERI : https://youtu.be/5mZLJCeMrn4
