TitouanMelon/ENIB_Robot_Mobile_Ros2/docs/latex/capt_dist_i_r_8c_source.tex

\doxysection{capt\+Dist\+IR.\+c}
\hypertarget{capt_dist_i_r_8c_source}{}\label{capt_dist_i_r_8c_source}\index{C:/Users/Administrator/Documents/GitHub/ENIB\_Robot\_Mobile\_Ros2/finalCode/WORKSPACE\_F411\_uROS/base\_robot/Core/Src/captDistIR.c@{C:/Users/Administrator/Documents/GitHub/ENIB\_Robot\_Mobile\_Ros2/finalCode/WORKSPACE\_F411\_uROS/base\_robot/Core/Src/captDistIR.c}}

\begin{DoxyCode}{0}
\DoxyCodeLine{\Hypertarget{capt_dist_i_r_8c_source_l00001}00001\ \textcolor{comment}{/*}}
\DoxyCodeLine{\Hypertarget{capt_dist_i_r_8c_source_l00002}00002\ \textcolor{comment}{\ *\ IRMeasure.c}}
\DoxyCodeLine{\Hypertarget{capt_dist_i_r_8c_source_l00003}00003\ \textcolor{comment}{\ */}}
\DoxyCodeLine{\Hypertarget{capt_dist_i_r_8c_source_l00004}00004\ }
\DoxyCodeLine{\Hypertarget{capt_dist_i_r_8c_source_l00005}00005\ }
\DoxyCodeLine{\Hypertarget{capt_dist_i_r_8c_source_l00006}00006\ \textcolor{preprocessor}{\#include\ "{}captDistIR.h"{}}}
\DoxyCodeLine{\Hypertarget{capt_dist_i_r_8c_source_l00007}00007\ }
\DoxyCodeLine{\Hypertarget{capt_dist_i_r_8c_source_l00008}00008\ ADC\_HandleTypeDef\ \ \ adcHandle;}
\DoxyCodeLine{\Hypertarget{capt_dist_i_r_8c_source_l00009}00009\ ADC\_HandleTypeDef\ \ \ adcHandle\_12;}
\DoxyCodeLine{\Hypertarget{capt_dist_i_r_8c_source_l00010}00010\ ADC\_HandleTypeDef\ \ \ adcHandle\_13;}
\DoxyCodeLine{\Hypertarget{capt_dist_i_r_8c_source_l00011}00011\ ADC\_ChannelConfTypeDef\ \ \ sConfig;}
\DoxyCodeLine{\Hypertarget{capt_dist_i_r_8c_source_l00012}00012\ }
\DoxyCodeLine{\Hypertarget{capt_dist_i_r_8c_source_l00013}00013\ \textcolor{comment}{//=================================================================}}
\DoxyCodeLine{\Hypertarget{capt_dist_i_r_8c_source_l00014}00014\ \textcolor{comment}{//\ \ \ \ \ \ \ \ \ \ ADC\ INIT\ FOR\ IR\ SENSOR\ SHARP\ GP2D12}}
\DoxyCodeLine{\Hypertarget{capt_dist_i_r_8c_source_l00015}00015\ \textcolor{comment}{//=================================================================}}
\DoxyCodeLine{\Hypertarget{capt_dist_i_r_8c_source_l00016}00016\ }
\DoxyCodeLine{\Hypertarget{capt_dist_i_r_8c_source_l00017}00017\ \textcolor{keywordtype}{void}\ \ captDistIR\_Init(\textcolor{keywordtype}{void})}
\DoxyCodeLine{\Hypertarget{capt_dist_i_r_8c_source_l00018}00018\ \{}
\DoxyCodeLine{\Hypertarget{capt_dist_i_r_8c_source_l00019}00019\ \ \ \ \ adcHandle.Instance\ \ \ \ \ \ =\ ADC1;}
\DoxyCodeLine{\Hypertarget{capt_dist_i_r_8c_source_l00020}00020\ }
\DoxyCodeLine{\Hypertarget{capt_dist_i_r_8c_source_l00021}00021\ \ \ \ \ adcHandle.Init.ClockPrescaler\ =\ ADC\_CLOCKPRESCALER\_PCLK\_DIV2;}
\DoxyCodeLine{\Hypertarget{capt_dist_i_r_8c_source_l00022}00022\ \ \ \ \ adcHandle.Init.DataAlign\ =\ ADC\_DATAALIGN\_RIGHT;}
\DoxyCodeLine{\Hypertarget{capt_dist_i_r_8c_source_l00023}00023\ \ \ \ \ adcHandle.Init.Resolution\ =\ ADC\_RESOLUTION12b;}
\DoxyCodeLine{\Hypertarget{capt_dist_i_r_8c_source_l00024}00024\ \ \ \ \ \textcolor{comment}{//\ Don't\ do\ continuous\ conversions\ -\/\ do\ them\ on\ demand}}
\DoxyCodeLine{\Hypertarget{capt_dist_i_r_8c_source_l00025}00025\ \ \ \ \ adcHandle.Init.ContinuousConvMode\ \ \ \ =\ DISABLE;\ \ \textcolor{comment}{//\ Continuous\ mode\ disabled\ to\ have\ only\ 1\ conversion\ at\ each\ conversion\ trig}}
\DoxyCodeLine{\Hypertarget{capt_dist_i_r_8c_source_l00026}00026\ \ \ \ \ \textcolor{comment}{//\ Disable\ the\ scan\ conversion\ so\ we\ do\ one\ at\ a\ time\ */}}
\DoxyCodeLine{\Hypertarget{capt_dist_i_r_8c_source_l00027}00027\ \ \ \ \ adcHandle.Init.ScanConvMode\ =\ DISABLE;}
\DoxyCodeLine{\Hypertarget{capt_dist_i_r_8c_source_l00028}00028\ \ \ \ \ \textcolor{comment}{//Say\ how\ many\ channels\ would\ be\ used\ by\ the\ sequencer}}
\DoxyCodeLine{\Hypertarget{capt_dist_i_r_8c_source_l00029}00029\ \ \ \ \ adcHandle.Init.NbrOfConversion\ =\ 2;}
\DoxyCodeLine{\Hypertarget{capt_dist_i_r_8c_source_l00030}00030\ \ \ \ \ adcHandle.Init.DiscontinuousConvMode\ =\ DISABLE;\ \ \textcolor{comment}{//\ Parameter\ discarded\ because\ sequencer\ is\ disabled}}
\DoxyCodeLine{\Hypertarget{capt_dist_i_r_8c_source_l00031}00031\ \ \ \ \ adcHandle.Init.NbrOfDiscConversion\ =\ 2;}
\DoxyCodeLine{\Hypertarget{capt_dist_i_r_8c_source_l00032}00032\ \ \ \ \ adcHandle.Init.ExternalTrigConvEdge\ =\ \ ADC\_EXTERNALTRIGCONVEDGE\_NONE\ ;}
\DoxyCodeLine{\Hypertarget{capt_dist_i_r_8c_source_l00033}00033\ \ \ \ \ \textcolor{comment}{//Start\ conversion\ by\ software,\ not\ an\ external\ trigger}}
\DoxyCodeLine{\Hypertarget{capt_dist_i_r_8c_source_l00034}00034\ \ \ \ \ adcHandle.Init.ExternalTrigConv\ =\ 0;}
\DoxyCodeLine{\Hypertarget{capt_dist_i_r_8c_source_l00035}00035\ \ \ \ \ adcHandle.Init.DMAContinuousRequests\ =\ DISABLE;}
\DoxyCodeLine{\Hypertarget{capt_dist_i_r_8c_source_l00036}00036\ \ \ \ \ adcHandle.Init.EOCSelection\ =\ DISABLE;}
\DoxyCodeLine{\Hypertarget{capt_dist_i_r_8c_source_l00037}00037\ }
\DoxyCodeLine{\Hypertarget{capt_dist_i_r_8c_source_l00038}00038\ \ \ \ \ HAL\_ADC\_Init(\&adcHandle);}
\DoxyCodeLine{\Hypertarget{capt_dist_i_r_8c_source_l00039}00039\ \}}
\DoxyCodeLine{\Hypertarget{capt_dist_i_r_8c_source_l00040}00040\ }
\DoxyCodeLine{\Hypertarget{capt_dist_i_r_8c_source_l00041}00041\ \textcolor{comment}{//=================================================================}}
\DoxyCodeLine{\Hypertarget{capt_dist_i_r_8c_source_l00042}00042\ \textcolor{comment}{//\ \ \ \ \ \ \ \ \ \ IR\ GET\ (POLL\ METHOD)}}
\DoxyCodeLine{\Hypertarget{capt_dist_i_r_8c_source_l00043}00043\ \textcolor{comment}{//=================================================================}}
\DoxyCodeLine{\Hypertarget{capt_dist_i_r_8c_source_l00044}00044\ }
\DoxyCodeLine{\Hypertarget{capt_dist_i_r_8c_source_l00045}00045\ \textcolor{keywordtype}{int}\ \ captDistIR\_Get(\textcolor{keywordtype}{int}*\ tab)}
\DoxyCodeLine{\Hypertarget{capt_dist_i_r_8c_source_l00046}00046\ \{}
\DoxyCodeLine{\Hypertarget{capt_dist_i_r_8c_source_l00047}00047\ \ \ \ \ sConfig.Channel\ \ \ \ \ \ =\ ADC\_CHANNEL\_4;}
\DoxyCodeLine{\Hypertarget{capt_dist_i_r_8c_source_l00048}00048\ \ \ \ \ sConfig.Rank\ \ \ \ \ \ \ \ \ =\ 1;}
\DoxyCodeLine{\Hypertarget{capt_dist_i_r_8c_source_l00049}00049\ \ \ \ \ sConfig.SamplingTime\ =\ ADC\_SAMPLETIME\_56CYCLES;}
\DoxyCodeLine{\Hypertarget{capt_dist_i_r_8c_source_l00050}00050\ \ \ \ \ HAL\_ADC\_ConfigChannel(\&adcHandle,\ \&sConfig);}
\DoxyCodeLine{\Hypertarget{capt_dist_i_r_8c_source_l00051}00051\ }
\DoxyCodeLine{\Hypertarget{capt_dist_i_r_8c_source_l00052}00052\ \ \ \ \ HAL\_ADC\_Start(\&adcHandle);\ \ \ \ \ \ \ \ \ \ \ \ \ \ \ \ \ \ \textcolor{comment}{//Start\ the\ conversion}}
\DoxyCodeLine{\Hypertarget{capt_dist_i_r_8c_source_l00053}00053\ \ \ \ \ HAL\_ADC\_PollForConversion(\&adcHandle,10);\ \ \ \textcolor{comment}{//Processing\ the\ conversion}}
\DoxyCodeLine{\Hypertarget{capt_dist_i_r_8c_source_l00054}00054\ \ \ \ \ tab[0]=HAL\_ADC\_GetValue(\&adcHandle);\ \ \ \ \ \ \ \ \textcolor{comment}{//Return\ the\ converted\ data}}
\DoxyCodeLine{\Hypertarget{capt_dist_i_r_8c_source_l00055}00055\ }
\DoxyCodeLine{\Hypertarget{capt_dist_i_r_8c_source_l00056}00056\ \ \ \ \ sConfig.Channel\ \ \ \ \ \ =\ ADC\_CHANNEL\_8;}
\DoxyCodeLine{\Hypertarget{capt_dist_i_r_8c_source_l00057}00057\ \ \ \ \ sConfig.Rank\ \ \ \ \ \ \ \ \ =\ 1;}
\DoxyCodeLine{\Hypertarget{capt_dist_i_r_8c_source_l00058}00058\ \ \ \ \ sConfig.SamplingTime\ =\ ADC\_SAMPLETIME\_56CYCLES;}
\DoxyCodeLine{\Hypertarget{capt_dist_i_r_8c_source_l00059}00059\ \ \ \ \ HAL\_ADC\_ConfigChannel(\&adcHandle,\ \&sConfig);}
\DoxyCodeLine{\Hypertarget{capt_dist_i_r_8c_source_l00060}00060\ }
\DoxyCodeLine{\Hypertarget{capt_dist_i_r_8c_source_l00061}00061\ \ \ \ \ HAL\_ADC\_Start(\&adcHandle);\ \ \ \ \ \ \ \ \ \ \ \ \ \ \ \ \ \ \ \ \ \ \textcolor{comment}{//Start\ the\ conversion}}
\DoxyCodeLine{\Hypertarget{capt_dist_i_r_8c_source_l00062}00062\ \ \ \ \ HAL\_ADC\_PollForConversion(\&adcHandle,10);\ \ \ \ \ \ \ \textcolor{comment}{//Processing\ the\ conversion}}
\DoxyCodeLine{\Hypertarget{capt_dist_i_r_8c_source_l00063}00063\ \ \ \ \ tab[1]=HAL\_ADC\_GetValue(\&adcHandle);\ \ \ \ \ \ \ \ \ \ \ \ \textcolor{comment}{//Return\ the\ converted\ data}}
\DoxyCodeLine{\Hypertarget{capt_dist_i_r_8c_source_l00064}00064\ }
\DoxyCodeLine{\Hypertarget{capt_dist_i_r_8c_source_l00065}00065\ \ \ \ \ \textcolor{keywordflow}{return}\ 0;}
\DoxyCodeLine{\Hypertarget{capt_dist_i_r_8c_source_l00066}00066\ \}}
\DoxyCodeLine{\Hypertarget{capt_dist_i_r_8c_source_l00067}00067\ \textcolor{comment}{//=================================================================}}

\end{DoxyCode}
