TitouanMelon/ENIB_Robot_Mobile_Ros2/docs/latex/config_8h_source.tex

\doxysection{config.\+h}
\hypertarget{config_8h_source}{}\label{config_8h_source}\index{C:/Users/Administrator/Documents/GitHub/ENIB\_Robot\_Mobile\_Ros2/finalCode/WORKSPACE\_F411\_uROS/base\_robot/Core/Inc/config.h@{C:/Users/Administrator/Documents/GitHub/ENIB\_Robot\_Mobile\_Ros2/finalCode/WORKSPACE\_F411\_uROS/base\_robot/Core/Inc/config.h}}

\begin{DoxyCode}{0}
\DoxyCodeLine{\Hypertarget{config_8h_source_l00001}00001\ \textcolor{comment}{/*}}
\DoxyCodeLine{\Hypertarget{config_8h_source_l00002}00002\ \textcolor{comment}{\ *\ config.h}}
\DoxyCodeLine{\Hypertarget{config_8h_source_l00003}00003\ \textcolor{comment}{\ */}}
\DoxyCodeLine{\Hypertarget{config_8h_source_l00004}00004\ }
\DoxyCodeLine{\Hypertarget{config_8h_source_l00005}00005\ \textcolor{preprocessor}{\#ifndef\ INC\_CONFIG\_H\_}}
\DoxyCodeLine{\Hypertarget{config_8h_source_l00006}00006\ \textcolor{preprocessor}{\#define\ INC\_CONFIG\_H\_}}
\DoxyCodeLine{\Hypertarget{config_8h_source_l00007}00007\ }
\DoxyCodeLine{\Hypertarget{config_8h_source_l00008}00008\ \textcolor{comment}{//========================================================}}
\DoxyCodeLine{\Hypertarget{config_8h_source_l00009}00009\ \textcolor{comment}{//\ USART\ :\ CHOIX\ DE\ LA\ LIAISON\ SERIE}}
\DoxyCodeLine{\Hypertarget{config_8h_source_l00010}00010\ \textcolor{comment}{//\ USART2\ :\ USART\_STLINK\ (cable)}}
\DoxyCodeLine{\Hypertarget{config_8h_source_l00011}00011\ \textcolor{comment}{//\ USART6\ :\ USART\_ZIGBEE\ (sans\ fil)}}
\DoxyCodeLine{\Hypertarget{config_8h_source_l00012}00012\ \textcolor{comment}{//========================================================}}
\DoxyCodeLine{\Hypertarget{config_8h_source_l00013}00013\ \textcolor{preprocessor}{\#define\ USE\_USART\_STLINK\ 1\ \ \ \ \ \ \ \ \ \ }\textcolor{comment}{//\ A\ Commenter\ pour\ utiliser\ stlink\ dans\ term\_printf\ !!\ faire\ un\ clean}}
\DoxyCodeLine{\Hypertarget{config_8h_source_l00014}00014\ \textcolor{comment}{//\#define\ \ \ USE\_USART\_ZIGBEE\ 1}}
\DoxyCodeLine{\Hypertarget{config_8h_source_l00015}00015\ }
\DoxyCodeLine{\Hypertarget{config_8h_source_l00016}00016\ \textcolor{preprocessor}{\#define\ NB\_CAR\_TO\_RECEIVE\ \ \ \ \ \ \ 1\ \ \ \ \ \ \ }\textcolor{comment}{//\ nombre\ de\ caractères\ à\ recevoir\ pour\ déclencher\ une\ interruption}}
\DoxyCodeLine{\Hypertarget{config_8h_source_l00017}00017\ }
\DoxyCodeLine{\Hypertarget{config_8h_source_l00018}00018\ \textcolor{preprocessor}{\#define\ USART2\_BAUDRATE\ \ \ \ \ \ \ \ \ 115200}}
\DoxyCodeLine{\Hypertarget{config_8h_source_l00019}00019\ \textcolor{preprocessor}{\#define\ USART6\_BAUDRATE\ \ \ \ \ \ \ \ \ 9600}}
\DoxyCodeLine{\Hypertarget{config_8h_source_l00020}00020\ \textcolor{comment}{//========================================================}}
\DoxyCodeLine{\Hypertarget{config_8h_source_l00021}00021\ \textcolor{comment}{//\ \ \ \ \ \ \ \ \ \ \ \ \ \ \ \ \ \ LIAISON\ I2C}}
\DoxyCodeLine{\Hypertarget{config_8h_source_l00022}00022\ \textcolor{comment}{//========================================================}}
\DoxyCodeLine{\Hypertarget{config_8h_source_l00023}00023\ \textcolor{preprocessor}{\#define\ I2C1\_CLOCKSPEED\ \ \ \ \ \ \ \ \ 100000}}
\DoxyCodeLine{\Hypertarget{config_8h_source_l00024}00024\ \textcolor{preprocessor}{\#define\ I2C2\_CLOCKSPEED\ \ \ \ \ \ \ \ \ 100000}}
\DoxyCodeLine{\Hypertarget{config_8h_source_l00025}00025\ }
\DoxyCodeLine{\Hypertarget{config_8h_source_l00026}00026\ \textcolor{comment}{//\ CAPTEUR\ I2C\ DISTANCE\ ULTRASON\ SRF02}}
\DoxyCodeLine{\Hypertarget{config_8h_source_l00027}00027\ \textcolor{preprocessor}{\#define\ CAPT\_US\_LEFT\_ADDRESS\ \ \ \ 0xE0}}
\DoxyCodeLine{\Hypertarget{config_8h_source_l00028}00028\ \textcolor{preprocessor}{\#define\ CAPT\_US\_RIGHT\_ADDRESS\ \ \ 0xE2}}
\DoxyCodeLine{\Hypertarget{config_8h_source_l00029}00029\ }
\DoxyCodeLine{\Hypertarget{config_8h_source_l00030}00030\ \textcolor{comment}{//\ IMU\ MPU9250}}
\DoxyCodeLine{\Hypertarget{config_8h_source_l00031}00031\ \textcolor{preprocessor}{\#define\ \ \ \ MPU9250\_ADDRESS\ \ \ \ \ \ 0x68}}
\DoxyCodeLine{\Hypertarget{config_8h_source_l00032}00032\ \textcolor{preprocessor}{\#define\ \ \ \ AK8963\_ADDRESS\ \ \ \ \ \ \ 0x0C}}
\DoxyCodeLine{\Hypertarget{config_8h_source_l00033}00033\ }
\DoxyCodeLine{\Hypertarget{config_8h_source_l00034}00034\ \textcolor{comment}{//\ ECRAN\ LCD}}
\DoxyCodeLine{\Hypertarget{config_8h_source_l00035}00035\ \textcolor{preprocessor}{\#define\ SCREEN\_LCD\_ADDRESS\ \ \ \ \ \ (0x30<<1)}}
\DoxyCodeLine{\Hypertarget{config_8h_source_l00036}00036\ }
\DoxyCodeLine{\Hypertarget{config_8h_source_l00037}00037\ \textcolor{comment}{//\ SAMPLING\ PERIOD\ in\ ms}}
\DoxyCodeLine{\Hypertarget{config_8h_source_l00038}00038\ \textcolor{preprocessor}{\#define\ SAMPLING\_PERIOD\_ms\ \ \ \ \ \ 5}}
\DoxyCodeLine{\Hypertarget{config_8h_source_l00039}00039\ }
\DoxyCodeLine{\Hypertarget{config_8h_source_l00040}00040\ \textcolor{preprocessor}{\#endif\ }\textcolor{comment}{/*\ INC\_CONFIG\_H\_\ */}\textcolor{preprocessor}{}}
\DoxyCodeLine{\Hypertarget{config_8h_source_l00041}00041\ }
\DoxyCodeLine{\Hypertarget{config_8h_source_l00042}00042\ \textcolor{comment}{/*\string^\string^\string^\string^\string^\string^\string^\string^\string^\string^\string^\string^\string^\string^\string^\string^\string^\string^\string^\string^\string^\string^\string^\string^\string^\string^\string^\string^\string^\string^\string^\string^\string^\string^\string^\string^\string^\string^\string^\string^\string^\string^\string^\string^\string^\string^\string^\string^\string^\string^\string^\string^\string^\string^\string^\string^\string^\string^\string^\string^\string^\string^\string^\string^\string^\string^\string^\string^\string^*/}}

\end{DoxyCode}
