TitouanMelon/ENIB_Robot_Mobile_Ros2/docs/latex/drv__gpio_8c_source.tex

\doxysection{drv\+\_\+gpio.\+c}
\hypertarget{drv__gpio_8c_source}{}\label{drv__gpio_8c_source}\index{C:/Users/Administrator/Documents/GitHub/ENIB\_Robot\_Mobile\_Ros2/finalCode/WORKSPACE\_F411\_uROS/base\_robot/Core/Src/drv\_gpio.c@{C:/Users/Administrator/Documents/GitHub/ENIB\_Robot\_Mobile\_Ros2/finalCode/WORKSPACE\_F411\_uROS/base\_robot/Core/Src/drv\_gpio.c}}

\begin{DoxyCode}{0}
\DoxyCodeLine{\Hypertarget{drv__gpio_8c_source_l00001}00001\ \textcolor{preprocessor}{\#include\ "{}\mbox{\hyperlink{main_8h}{main.h}}"{}}}
\DoxyCodeLine{\Hypertarget{drv__gpio_8c_source_l00002}00002\ \textcolor{preprocessor}{\#include\ "{}drv\_gpio.h"{}}}
\DoxyCodeLine{\Hypertarget{drv__gpio_8c_source_l00003}00003\ }
\DoxyCodeLine{\Hypertarget{drv__gpio_8c_source_l00004}00004\ \textcolor{keywordtype}{void}\ MX\_GPIO\_Init(\textcolor{keywordtype}{void})}
\DoxyCodeLine{\Hypertarget{drv__gpio_8c_source_l00005}00005\ \{}
\DoxyCodeLine{\Hypertarget{drv__gpio_8c_source_l00006}00006\ \ \ GPIO\_InitTypeDef\ GPIO\_InitStruct\ =\ \{0\};}
\DoxyCodeLine{\Hypertarget{drv__gpio_8c_source_l00007}00007\ }
\DoxyCodeLine{\Hypertarget{drv__gpio_8c_source_l00008}00008\ \ \ \textcolor{comment}{/*\ GPIO\ Ports\ Clock\ Enable\ */}}
\DoxyCodeLine{\Hypertarget{drv__gpio_8c_source_l00009}00009\ \ \ \_\_HAL\_RCC\_GPIOC\_CLK\_ENABLE();}
\DoxyCodeLine{\Hypertarget{drv__gpio_8c_source_l00010}00010\ \ \ \_\_HAL\_RCC\_GPIOH\_CLK\_ENABLE();}
\DoxyCodeLine{\Hypertarget{drv__gpio_8c_source_l00011}00011\ \ \ \_\_HAL\_RCC\_GPIOA\_CLK\_ENABLE();}
\DoxyCodeLine{\Hypertarget{drv__gpio_8c_source_l00012}00012\ \ \ \_\_HAL\_RCC\_GPIOB\_CLK\_ENABLE();}
\DoxyCodeLine{\Hypertarget{drv__gpio_8c_source_l00013}00013\ }
\DoxyCodeLine{\Hypertarget{drv__gpio_8c_source_l00014}00014\ \ \ \textcolor{comment}{/*Configure\ GPIO\ pin\ Output\ Level\ */}}
\DoxyCodeLine{\Hypertarget{drv__gpio_8c_source_l00015}00015\ \ \ HAL\_GPIO\_WritePin(LD2\_GPIO\_Port,\ LD2\_Pin,\ GPIO\_PIN\_RESET);}
\DoxyCodeLine{\Hypertarget{drv__gpio_8c_source_l00016}00016\ }
\DoxyCodeLine{\Hypertarget{drv__gpio_8c_source_l00017}00017\ \ \ \textcolor{comment}{/*Configure\ GPIO\ pin\ :\ B1\_Pin\ */}}
\DoxyCodeLine{\Hypertarget{drv__gpio_8c_source_l00018}00018\ \ \ GPIO\_InitStruct.Pin\ =\ B1\_Pin;}
\DoxyCodeLine{\Hypertarget{drv__gpio_8c_source_l00019}00019\ \ \ GPIO\_InitStruct.Mode\ =\ GPIO\_MODE\_IT\_FALLING;}
\DoxyCodeLine{\Hypertarget{drv__gpio_8c_source_l00020}00020\ \ \ GPIO\_InitStruct.Pull\ =\ GPIO\_NOPULL;}
\DoxyCodeLine{\Hypertarget{drv__gpio_8c_source_l00021}00021\ \ \ HAL\_GPIO\_Init(B1\_GPIO\_Port,\ \&GPIO\_InitStruct);}
\DoxyCodeLine{\Hypertarget{drv__gpio_8c_source_l00022}00022\ }
\DoxyCodeLine{\Hypertarget{drv__gpio_8c_source_l00023}00023\ \ \ \textcolor{comment}{/*Configure\ GPIO\ pin\ :\ LD2\_Pin\ */}}
\DoxyCodeLine{\Hypertarget{drv__gpio_8c_source_l00024}00024\ \ \ GPIO\_InitStruct.Pin\ =\ LD2\_Pin;}
\DoxyCodeLine{\Hypertarget{drv__gpio_8c_source_l00025}00025\ \ \ GPIO\_InitStruct.Mode\ =\ GPIO\_MODE\_OUTPUT\_PP;}
\DoxyCodeLine{\Hypertarget{drv__gpio_8c_source_l00026}00026\ \ \ GPIO\_InitStruct.Pull\ =\ GPIO\_NOPULL;}
\DoxyCodeLine{\Hypertarget{drv__gpio_8c_source_l00027}00027\ \ \ GPIO\_InitStruct.Speed\ =\ GPIO\_SPEED\_FREQ\_LOW;}
\DoxyCodeLine{\Hypertarget{drv__gpio_8c_source_l00028}00028\ \ \ HAL\_GPIO\_Init(LD2\_GPIO\_Port,\ \&GPIO\_InitStruct);}
\DoxyCodeLine{\Hypertarget{drv__gpio_8c_source_l00029}00029\ }
\DoxyCodeLine{\Hypertarget{drv__gpio_8c_source_l00030}00030\ \}}
\DoxyCodeLine{\Hypertarget{drv__gpio_8c_source_l00031}00031\ }
\DoxyCodeLine{\Hypertarget{drv__gpio_8c_source_l00032}00032\ \textcolor{keyword}{extern}\ \textcolor{keywordtype}{void}\ quadEncoder\_CallbackIndexL(\textcolor{keywordtype}{void});}
\DoxyCodeLine{\Hypertarget{drv__gpio_8c_source_l00033}00033\ \textcolor{keyword}{extern}\ \textcolor{keywordtype}{void}\ quadEncoder\_CallbackIndexR(\textcolor{keywordtype}{void});}
\DoxyCodeLine{\Hypertarget{drv__gpio_8c_source_l00034}00034\ }
\DoxyCodeLine{\Hypertarget{drv__gpio_8c_source_l00035}00035\ \textcolor{keywordtype}{void}\ HAL\_GPIO\_EXTI\_Callback(uint16\_t\ GPIO\_Pin)}
\DoxyCodeLine{\Hypertarget{drv__gpio_8c_source_l00036}00036\ \{}
\DoxyCodeLine{\Hypertarget{drv__gpio_8c_source_l00037}00037\ \ \ \ \ \textcolor{keywordflow}{switch}(GPIO\_Pin)}
\DoxyCodeLine{\Hypertarget{drv__gpio_8c_source_l00038}00038\ \ \ \ \ \{}
\DoxyCodeLine{\Hypertarget{drv__gpio_8c_source_l00039}00039\ \ \ \ \ \textcolor{keywordflow}{case}\ GPIO\_PIN\_0\ :}
\DoxyCodeLine{\Hypertarget{drv__gpio_8c_source_l00040}00040\ \ \ \ \ \ \ \ \ quadEncoder\_CallbackIndexR();}
\DoxyCodeLine{\Hypertarget{drv__gpio_8c_source_l00041}00041\ \ \ \ \ \ \ \ \ \ \ \ \ \ \ \ \ \ \ \ \ \textcolor{keywordflow}{break};}
\DoxyCodeLine{\Hypertarget{drv__gpio_8c_source_l00042}00042\ }
\DoxyCodeLine{\Hypertarget{drv__gpio_8c_source_l00043}00043\ \ \ \ \ \textcolor{keywordflow}{case}\ GPIO\_PIN\_1\ :}
\DoxyCodeLine{\Hypertarget{drv__gpio_8c_source_l00044}00044\ }
\DoxyCodeLine{\Hypertarget{drv__gpio_8c_source_l00045}00045\ \ \ \ \ \ \ \ \ \ \ \ \ \ \ \ \ \ \ \ \ \textcolor{keywordflow}{break};}
\DoxyCodeLine{\Hypertarget{drv__gpio_8c_source_l00046}00046\ }
\DoxyCodeLine{\Hypertarget{drv__gpio_8c_source_l00047}00047\ \ \ \ \ \textcolor{keywordflow}{case}\ GPIO\_PIN\_3:}
\DoxyCodeLine{\Hypertarget{drv__gpio_8c_source_l00048}00048\ \ \ \ \ \ \ \ \ \ \ \ \ \ \ \ \ \ \ \ \ \textcolor{keywordflow}{break};}
\DoxyCodeLine{\Hypertarget{drv__gpio_8c_source_l00049}00049\ }
\DoxyCodeLine{\Hypertarget{drv__gpio_8c_source_l00050}00050\ \ \ \ \ \textcolor{keywordflow}{case}\ GPIO\_PIN\_10:}
\DoxyCodeLine{\Hypertarget{drv__gpio_8c_source_l00051}00051\ \ \ \ \ \ \ \ \ quadEncoder\_CallbackIndexL();}
\DoxyCodeLine{\Hypertarget{drv__gpio_8c_source_l00052}00052\ \ \ \ \ \ \ \ \ \ \ \ \ \ \ \ \ \ \ \ \ \textcolor{keywordflow}{break};}
\DoxyCodeLine{\Hypertarget{drv__gpio_8c_source_l00053}00053\ }
\DoxyCodeLine{\Hypertarget{drv__gpio_8c_source_l00054}00054\ \ \ \ \ \textcolor{keywordflow}{case}\ GPIO\_PIN\_13\ :\ \ \ \ \ \ \textcolor{comment}{//\ USER\ BUTTON}}
\DoxyCodeLine{\Hypertarget{drv__gpio_8c_source_l00055}00055\ \ \ \ \ \ \ \ \ \ \ \ \ \ \ \ \ \ \ \ \ \textcolor{keywordflow}{break};}
\DoxyCodeLine{\Hypertarget{drv__gpio_8c_source_l00056}00056\ }
\DoxyCodeLine{\Hypertarget{drv__gpio_8c_source_l00057}00057\ \ \ \ \ default\ :\ \ \ \ \ \ \ \textcolor{keywordflow}{break};}
\DoxyCodeLine{\Hypertarget{drv__gpio_8c_source_l00058}00058\ }
\DoxyCodeLine{\Hypertarget{drv__gpio_8c_source_l00059}00059\ }
\DoxyCodeLine{\Hypertarget{drv__gpio_8c_source_l00060}00060\ \ \ \ \ \}}
\DoxyCodeLine{\Hypertarget{drv__gpio_8c_source_l00061}00061\ \}}

\end{DoxyCode}
