TitouanMelon/ENIB_Robot_Mobile_Ros2/docs/latex/drv__i2c_8c_source.tex

\doxysection{drv\+\_\+i2c.\+c}
\hypertarget{drv__i2c_8c_source}{}\label{drv__i2c_8c_source}\index{C:/Users/Administrator/Documents/GitHub/ENIB\_Robot\_Mobile\_Ros2/finalCode/WORKSPACE\_F411\_uROS/base\_robot/Core/Src/drv\_i2c.c@{C:/Users/Administrator/Documents/GitHub/ENIB\_Robot\_Mobile\_Ros2/finalCode/WORKSPACE\_F411\_uROS/base\_robot/Core/Src/drv\_i2c.c}}

\begin{DoxyCode}{0}
\DoxyCodeLine{\Hypertarget{drv__i2c_8c_source_l00001}00001\ \textcolor{preprocessor}{\#include\ "{}\mbox{\hyperlink{main_8h}{main.h}}"{}}}
\DoxyCodeLine{\Hypertarget{drv__i2c_8c_source_l00002}00002\ \textcolor{preprocessor}{\#include\ <string.h>}}
\DoxyCodeLine{\Hypertarget{drv__i2c_8c_source_l00003}00003\ \textcolor{preprocessor}{\#include\ "{}drv\_i2c.h"{}}}
\DoxyCodeLine{\Hypertarget{drv__i2c_8c_source_l00004}00004\ }
\DoxyCodeLine{\Hypertarget{drv__i2c_8c_source_l00005}00005\ }
\DoxyCodeLine{\Hypertarget{drv__i2c_8c_source_l00006}00006\ I2C\_HandleTypeDef\ hi2c1;}
\DoxyCodeLine{\Hypertarget{drv__i2c_8c_source_l00007}00007\ }
\DoxyCodeLine{\Hypertarget{drv__i2c_8c_source_l00008}00008\ \textcolor{keywordtype}{void}\ MX\_I2C1\_Init(\textcolor{keywordtype}{void})}
\DoxyCodeLine{\Hypertarget{drv__i2c_8c_source_l00009}00009\ \{}
\DoxyCodeLine{\Hypertarget{drv__i2c_8c_source_l00010}00010\ }
\DoxyCodeLine{\Hypertarget{drv__i2c_8c_source_l00011}00011\ \ \ hi2c1.Instance\ =\ I2C1;}
\DoxyCodeLine{\Hypertarget{drv__i2c_8c_source_l00012}00012\ \ \ hi2c1.Init.ClockSpeed\ =\ 100000;}
\DoxyCodeLine{\Hypertarget{drv__i2c_8c_source_l00013}00013\ \ \ hi2c1.Init.DutyCycle\ =\ I2C\_DUTYCYCLE\_2;}
\DoxyCodeLine{\Hypertarget{drv__i2c_8c_source_l00014}00014\ \ \ hi2c1.Init.OwnAddress1\ =\ 0;}
\DoxyCodeLine{\Hypertarget{drv__i2c_8c_source_l00015}00015\ \ \ hi2c1.Init.AddressingMode\ =\ I2C\_ADDRESSINGMODE\_7BIT;}
\DoxyCodeLine{\Hypertarget{drv__i2c_8c_source_l00016}00016\ \ \ hi2c1.Init.DualAddressMode\ =\ I2C\_DUALADDRESS\_DISABLE;}
\DoxyCodeLine{\Hypertarget{drv__i2c_8c_source_l00017}00017\ \ \ hi2c1.Init.OwnAddress2\ =\ 0;}
\DoxyCodeLine{\Hypertarget{drv__i2c_8c_source_l00018}00018\ \ \ hi2c1.Init.GeneralCallMode\ =\ I2C\_GENERALCALL\_DISABLE;}
\DoxyCodeLine{\Hypertarget{drv__i2c_8c_source_l00019}00019\ \ \ hi2c1.Init.NoStretchMode\ =\ I2C\_NOSTRETCH\_DISABLE;}
\DoxyCodeLine{\Hypertarget{drv__i2c_8c_source_l00020}00020\ \ \ \textcolor{keywordflow}{if}\ (HAL\_I2C\_Init(\&hi2c1)\ !=\ HAL\_OK)}
\DoxyCodeLine{\Hypertarget{drv__i2c_8c_source_l00021}00021\ \ \ \{}
\DoxyCodeLine{\Hypertarget{drv__i2c_8c_source_l00022}00022\ \ \ \ \ Error\_Handler();}
\DoxyCodeLine{\Hypertarget{drv__i2c_8c_source_l00023}00023\ \ \ \}}
\DoxyCodeLine{\Hypertarget{drv__i2c_8c_source_l00024}00024\ }
\DoxyCodeLine{\Hypertarget{drv__i2c_8c_source_l00025}00025\ \}}
\DoxyCodeLine{\Hypertarget{drv__i2c_8c_source_l00026}00026\ }
\DoxyCodeLine{\Hypertarget{drv__i2c_8c_source_l00027}00027\ }
\DoxyCodeLine{\Hypertarget{drv__i2c_8c_source_l00028}00028\ }
\DoxyCodeLine{\Hypertarget{drv__i2c_8c_source_l00029}00029\ }
\DoxyCodeLine{\Hypertarget{drv__i2c_8c_source_l00030}00030\ }
\DoxyCodeLine{\Hypertarget{drv__i2c_8c_source_l00031}00031\ \textcolor{comment}{//======================================================================}}
\DoxyCodeLine{\Hypertarget{drv__i2c_8c_source_l00032}00032\ \textcolor{comment}{//\ Transmit\ n\_data\ bytes\ to\ i2c\ slave}}
\DoxyCodeLine{\Hypertarget{drv__i2c_8c_source_l00033}00033\ \textcolor{comment}{//======================================================================}}
\DoxyCodeLine{\Hypertarget{drv__i2c_8c_source_l00034}00034\ \textcolor{keywordtype}{int}\ i2c1\_WriteBuffer(uint16\_t\ addrSlave,\ uint8\_t\ *data,\ \textcolor{keywordtype}{int}\ n\_data)}
\DoxyCodeLine{\Hypertarget{drv__i2c_8c_source_l00035}00035\ \{}
\DoxyCodeLine{\Hypertarget{drv__i2c_8c_source_l00036}00036\ \ \ \ \ \textcolor{keywordtype}{int}\ status;}
\DoxyCodeLine{\Hypertarget{drv__i2c_8c_source_l00037}00037\ \ \ \ \ status\ =\ HAL\_I2C\_Master\_Transmit(\&hi2c1,\ addrSlave,\ data,\ n\_data\ ,\ 100);}
\DoxyCodeLine{\Hypertarget{drv__i2c_8c_source_l00038}00038\ \ \ \ \ \textcolor{keywordflow}{return}\ status;}
\DoxyCodeLine{\Hypertarget{drv__i2c_8c_source_l00039}00039\ \}}
\DoxyCodeLine{\Hypertarget{drv__i2c_8c_source_l00040}00040\ \textcolor{comment}{//======================================================================}}
\DoxyCodeLine{\Hypertarget{drv__i2c_8c_source_l00041}00041\ \textcolor{comment}{//\ Receive\ n\_data\ bytes\ from\ i2c\ slave}}
\DoxyCodeLine{\Hypertarget{drv__i2c_8c_source_l00042}00042\ \textcolor{comment}{//======================================================================}}
\DoxyCodeLine{\Hypertarget{drv__i2c_8c_source_l00043}00043\ \textcolor{keywordtype}{int}\ i2c1\_ReadBuffer(uint16\_t\ addrSlave,\ uint8\_t\ *data,\ \textcolor{keywordtype}{int}\ n\_data)}
\DoxyCodeLine{\Hypertarget{drv__i2c_8c_source_l00044}00044\ \{}
\DoxyCodeLine{\Hypertarget{drv__i2c_8c_source_l00045}00045\ \ \ \ \ \textcolor{keywordtype}{int}\ status;}
\DoxyCodeLine{\Hypertarget{drv__i2c_8c_source_l00046}00046\ \ \ \ \ status\ =\ HAL\_I2C\_Master\_Receive(\&hi2c1,\ addrSlave,\ data,\ n\_data\ ,\ 100);}
\DoxyCodeLine{\Hypertarget{drv__i2c_8c_source_l00047}00047\ \ \ \ \ \textcolor{keywordflow}{return}\ status;}
\DoxyCodeLine{\Hypertarget{drv__i2c_8c_source_l00048}00048\ \}}
\DoxyCodeLine{\Hypertarget{drv__i2c_8c_source_l00049}00049\ \textcolor{comment}{//======================================================================}}
\DoxyCodeLine{\Hypertarget{drv__i2c_8c_source_l00050}00050\ \textcolor{comment}{//\ Receive\ n\_data\ bytes\ -\/\ located\ at\ regAddr\ -\/\ from\ i2c\ slave}}
\DoxyCodeLine{\Hypertarget{drv__i2c_8c_source_l00051}00051\ \textcolor{comment}{//======================================================================}}
\DoxyCodeLine{\Hypertarget{drv__i2c_8c_source_l00052}00052\ \textcolor{keywordtype}{int}\ i2c1\_ReadRegBuffer(uint16\_t\ addrSlave,\ uint8\_t\ \ regAddr,\ \ uint8\_t\ *data,\ \textcolor{keywordtype}{int}\ n\_data)}
\DoxyCodeLine{\Hypertarget{drv__i2c_8c_source_l00053}00053\ \{}
\DoxyCodeLine{\Hypertarget{drv__i2c_8c_source_l00054}00054\ \ \ \ \ \textcolor{keywordtype}{int}\ status;}
\DoxyCodeLine{\Hypertarget{drv__i2c_8c_source_l00055}00055\ \ \ \ \ uint8\_t\ RegAddr;}
\DoxyCodeLine{\Hypertarget{drv__i2c_8c_source_l00056}00056\ \ \ \ \ RegAddr=regAddr;}
\DoxyCodeLine{\Hypertarget{drv__i2c_8c_source_l00057}00057\ \ \ \ \ \textcolor{keywordflow}{do}\{}
\DoxyCodeLine{\Hypertarget{drv__i2c_8c_source_l00058}00058\ \ \ \ \ \ \ \ \ status=HAL\_I2C\_Master\_Transmit(\&hi2c1,\ addrSlave,\ \&RegAddr,\ 1,\ 100);}
\DoxyCodeLine{\Hypertarget{drv__i2c_8c_source_l00059}00059\ \ \ \ \ \ \ \ \ \textcolor{keywordflow}{if}(\ status\ )}
\DoxyCodeLine{\Hypertarget{drv__i2c_8c_source_l00060}00060\ \ \ \ \ \ \ \ \ \ \ \ \ \textcolor{keywordflow}{break};}
\DoxyCodeLine{\Hypertarget{drv__i2c_8c_source_l00061}00061\ \ \ \ \ \ \ \ \ status\ =HAL\_I2C\_Master\_Receive(\&hi2c1,\ addrSlave,\ data,\ n\_data,\ n\_data*100);}
\DoxyCodeLine{\Hypertarget{drv__i2c_8c_source_l00062}00062\ \ \ \ \ \}\textcolor{keywordflow}{while}(0);}
\DoxyCodeLine{\Hypertarget{drv__i2c_8c_source_l00063}00063\ \ \ \ \ \textcolor{keywordflow}{return}\ status;}
\DoxyCodeLine{\Hypertarget{drv__i2c_8c_source_l00064}00064\ \}}
\DoxyCodeLine{\Hypertarget{drv__i2c_8c_source_l00065}00065\ }
\DoxyCodeLine{\Hypertarget{drv__i2c_8c_source_l00066}00066\ \textcolor{comment}{//======================================================================}}
\DoxyCodeLine{\Hypertarget{drv__i2c_8c_source_l00067}00067\ \textcolor{comment}{//\ Write\ n\_data\ bytes\ -\/\ have\ to\ be\ written\ at\ regAddr\ -\/\ to\ i2c\ slave}}
\DoxyCodeLine{\Hypertarget{drv__i2c_8c_source_l00068}00068\ \textcolor{comment}{//======================================================================}}
\DoxyCodeLine{\Hypertarget{drv__i2c_8c_source_l00069}00069\ \textcolor{keywordtype}{int}\ i2c1\_WriteRegBuffer(uint16\_t\ addrSlave,\ uint8\_t\ \ regAddr,\ \ uint8\_t\ *data,\ \textcolor{keywordtype}{int}\ n\_data)}
\DoxyCodeLine{\Hypertarget{drv__i2c_8c_source_l00070}00070\ \{}
\DoxyCodeLine{\Hypertarget{drv__i2c_8c_source_l00071}00071\ \ \ \ \ \textcolor{keywordtype}{int}\ status;}
\DoxyCodeLine{\Hypertarget{drv__i2c_8c_source_l00072}00072\ \ \ \ \ uint8\_t\ RegAddr[0x10];}
\DoxyCodeLine{\Hypertarget{drv__i2c_8c_source_l00073}00073\ \ \ \ \ RegAddr[0]=regAddr;}
\DoxyCodeLine{\Hypertarget{drv__i2c_8c_source_l00074}00074\ \ \ \ \ memcpy(RegAddr+1,\ data,\ n\_data);}
\DoxyCodeLine{\Hypertarget{drv__i2c_8c_source_l00075}00075\ \ \ \ status=HAL\_I2C\_Master\_Transmit(\&hi2c1,\ addrSlave,\ RegAddr,\ n\_data+1,\ 100);}
\DoxyCodeLine{\Hypertarget{drv__i2c_8c_source_l00076}00076\ \ \ \ \ \ \textcolor{keywordflow}{return}\ status;}
\DoxyCodeLine{\Hypertarget{drv__i2c_8c_source_l00077}00077\ \}}
\DoxyCodeLine{\Hypertarget{drv__i2c_8c_source_l00078}00078\ }
\DoxyCodeLine{\Hypertarget{drv__i2c_8c_source_l00079}00079\ \textcolor{comment}{//======================================================================}}
\DoxyCodeLine{\Hypertarget{drv__i2c_8c_source_l00080}00080\ \textcolor{comment}{//\ Write\ 1\ byte\ at\ regAddr\ Slave\ -\/\ Interrupt\ Method}}
\DoxyCodeLine{\Hypertarget{drv__i2c_8c_source_l00081}00081\ \textcolor{comment}{//======================================================================}}
\DoxyCodeLine{\Hypertarget{drv__i2c_8c_source_l00082}00082\ \textcolor{keywordtype}{void}\ i2c1\_WriteRegByte\_IT(uint16\_t\ addrSlave,\ uint8\_t\ \ regAddr,\ \ uint8\_t\ data)}
\DoxyCodeLine{\Hypertarget{drv__i2c_8c_source_l00083}00083\ \{}
\DoxyCodeLine{\Hypertarget{drv__i2c_8c_source_l00084}00084\ }
\DoxyCodeLine{\Hypertarget{drv__i2c_8c_source_l00085}00085\ uint8\_t\ datas\_to\_send[2];}
\DoxyCodeLine{\Hypertarget{drv__i2c_8c_source_l00086}00086\ }
\DoxyCodeLine{\Hypertarget{drv__i2c_8c_source_l00087}00087\ datas\_to\_send[0]=regAddr;}
\DoxyCodeLine{\Hypertarget{drv__i2c_8c_source_l00088}00088\ datas\_to\_send[1]=data;}
\DoxyCodeLine{\Hypertarget{drv__i2c_8c_source_l00089}00089\ }
\DoxyCodeLine{\Hypertarget{drv__i2c_8c_source_l00090}00090\ \ \ \ \ \textcolor{keywordflow}{while}(HAL\_I2C\_Master\_Transmit\_IT(\&hi2c1,\ addrSlave,\ datas\_to\_send,\ 2)!=\ HAL\_OK)\{\}}
\DoxyCodeLine{\Hypertarget{drv__i2c_8c_source_l00091}00091\ \ \ \ \ \textcolor{keywordflow}{while}\ (HAL\_I2C\_GetState(\&hi2c1)\ !=\ HAL\_I2C\_STATE\_READY)\{\}}
\DoxyCodeLine{\Hypertarget{drv__i2c_8c_source_l00092}00092\ \}}
\DoxyCodeLine{\Hypertarget{drv__i2c_8c_source_l00093}00093\ \textcolor{comment}{//======================================================================}}
\DoxyCodeLine{\Hypertarget{drv__i2c_8c_source_l00094}00094\ \textcolor{comment}{//\ Read\ 1\ byte\ from\ regAddr\ Slave\ -\/\ Interrupt\ Method}}
\DoxyCodeLine{\Hypertarget{drv__i2c_8c_source_l00095}00095\ \textcolor{comment}{//======================================================================}}
\DoxyCodeLine{\Hypertarget{drv__i2c_8c_source_l00096}00096\ \textcolor{keywordtype}{void}\ i2c1\_ReadRegBuffer\_IT(uint16\_t\ addrSlave,\ uint8\_t\ \ regAddr,\ \ uint8\_t*\ datas,\ \textcolor{keywordtype}{int}\ len)}
\DoxyCodeLine{\Hypertarget{drv__i2c_8c_source_l00097}00097\ \{}
\DoxyCodeLine{\Hypertarget{drv__i2c_8c_source_l00098}00098\ \ \ \ \ \textcolor{keywordflow}{while}(HAL\_I2C\_Master\_Transmit\_IT(\&hi2c1,\ addrSlave,\ \&regAddr,\ 1)!=\ HAL\_OK)\{\}}
\DoxyCodeLine{\Hypertarget{drv__i2c_8c_source_l00099}00099\ \ \ \ \ \textcolor{keywordflow}{while}\ (HAL\_I2C\_GetState(\&hi2c1)\ !=\ HAL\_I2C\_STATE\_READY)\{\}}
\DoxyCodeLine{\Hypertarget{drv__i2c_8c_source_l00100}00100\ }
\DoxyCodeLine{\Hypertarget{drv__i2c_8c_source_l00101}00101\ \ \ \ \ \textcolor{keywordflow}{while}(HAL\_I2C\_Master\_Receive\_IT(\&hi2c1,\ addrSlave,\ datas,\ len)!=\ HAL\_OK)\{\}}
\DoxyCodeLine{\Hypertarget{drv__i2c_8c_source_l00102}00102\ \ \ \ \ \textcolor{keywordflow}{while}(\ HAL\_I2C\_GetState(\&hi2c1)\ !=\ HAL\_I2C\_STATE\_READY\ )\{\}}
\DoxyCodeLine{\Hypertarget{drv__i2c_8c_source_l00103}00103\ \}}
\DoxyCodeLine{\Hypertarget{drv__i2c_8c_source_l00104}00104\ }
\DoxyCodeLine{\Hypertarget{drv__i2c_8c_source_l00105}00105\ \textcolor{comment}{//======================================================================}}
\DoxyCodeLine{\Hypertarget{drv__i2c_8c_source_l00106}00106\ \textcolor{comment}{//\ Write\ 1\ byte\ to\ regAddr\ (16\ bits)\ Slave}}
\DoxyCodeLine{\Hypertarget{drv__i2c_8c_source_l00107}00107\ \textcolor{comment}{//======================================================================}}
\DoxyCodeLine{\Hypertarget{drv__i2c_8c_source_l00108}00108\ \textcolor{keywordtype}{int}\ i2c1\_WriteReg16Byte(uint16\_t\ addrSlave,\ uint16\_t\ \ regAddr,\ \ uint8\_t\ data)}
\DoxyCodeLine{\Hypertarget{drv__i2c_8c_source_l00109}00109\ \{}
\DoxyCodeLine{\Hypertarget{drv__i2c_8c_source_l00110}00110\ \ \ \ \ \textcolor{keywordtype}{int}\ status;}
\DoxyCodeLine{\Hypertarget{drv__i2c_8c_source_l00111}00111\ \ \ \ \ uint8\_t\ buffer[3];}
\DoxyCodeLine{\Hypertarget{drv__i2c_8c_source_l00112}00112\ \ \ \ \ buffer[0]=regAddr>>8;}
\DoxyCodeLine{\Hypertarget{drv__i2c_8c_source_l00113}00113\ \ \ \ \ buffer[1]=regAddr\&0xFF;}
\DoxyCodeLine{\Hypertarget{drv__i2c_8c_source_l00114}00114\ \ \ \ \ buffer[2]=data;}
\DoxyCodeLine{\Hypertarget{drv__i2c_8c_source_l00115}00115\ }
\DoxyCodeLine{\Hypertarget{drv__i2c_8c_source_l00116}00116\ \ \ \ \ status\ =\ HAL\_I2C\_Master\_Transmit(\&hi2c1,\ addrSlave,\ buffer,\ 3\ ,\ 100);}
\DoxyCodeLine{\Hypertarget{drv__i2c_8c_source_l00117}00117\ \ \ \ \ \textcolor{keywordflow}{return}\ status;}
\DoxyCodeLine{\Hypertarget{drv__i2c_8c_source_l00118}00118\ }
\DoxyCodeLine{\Hypertarget{drv__i2c_8c_source_l00119}00119\ \}}
\DoxyCodeLine{\Hypertarget{drv__i2c_8c_source_l00120}00120\ \textcolor{comment}{//======================================================================}}
\DoxyCodeLine{\Hypertarget{drv__i2c_8c_source_l00121}00121\ \textcolor{comment}{//\ Write\ 16\ bits\ word\ to\ regAddr\ (16\ bits)\ Slave}}
\DoxyCodeLine{\Hypertarget{drv__i2c_8c_source_l00122}00122\ \textcolor{comment}{//======================================================================}}
\DoxyCodeLine{\Hypertarget{drv__i2c_8c_source_l00123}00123\ \textcolor{keywordtype}{int}\ i2c1\_WriteReg16Word16(uint16\_t\ addrSlave,\ uint16\_t\ \ regAddr,\ \ uint16\_t\ data)}
\DoxyCodeLine{\Hypertarget{drv__i2c_8c_source_l00124}00124\ \{}
\DoxyCodeLine{\Hypertarget{drv__i2c_8c_source_l00125}00125\ \ \ \ \ \textcolor{keywordtype}{int}\ status;}
\DoxyCodeLine{\Hypertarget{drv__i2c_8c_source_l00126}00126\ \ \ \ \ uint8\_t\ buffer[4];}
\DoxyCodeLine{\Hypertarget{drv__i2c_8c_source_l00127}00127\ \ \ \ \ buffer[0]=regAddr>>8;}
\DoxyCodeLine{\Hypertarget{drv__i2c_8c_source_l00128}00128\ \ \ \ \ buffer[1]=regAddr\&0xFF;}
\DoxyCodeLine{\Hypertarget{drv__i2c_8c_source_l00129}00129\ \ \ \ \ buffer[2]=data>>8;}
\DoxyCodeLine{\Hypertarget{drv__i2c_8c_source_l00130}00130\ \ \ \ \ buffer[3]=data\&0xFF;}
\DoxyCodeLine{\Hypertarget{drv__i2c_8c_source_l00131}00131\ }
\DoxyCodeLine{\Hypertarget{drv__i2c_8c_source_l00132}00132\ \ \ \ \ status\ =\ HAL\_I2C\_Master\_Transmit(\&hi2c1,\ addrSlave,\ buffer,\ 4\ ,\ 100);}
\DoxyCodeLine{\Hypertarget{drv__i2c_8c_source_l00133}00133\ \ \ \ \ \textcolor{keywordflow}{return}\ status;}
\DoxyCodeLine{\Hypertarget{drv__i2c_8c_source_l00134}00134\ \}}
\DoxyCodeLine{\Hypertarget{drv__i2c_8c_source_l00135}00135\ \textcolor{comment}{//======================================================================}}
\DoxyCodeLine{\Hypertarget{drv__i2c_8c_source_l00136}00136\ \textcolor{comment}{//\ Write\ 32\ bits\ word\ to\ regAddr\ (16\ bits)\ Slave}}
\DoxyCodeLine{\Hypertarget{drv__i2c_8c_source_l00137}00137\ \textcolor{comment}{//======================================================================}}
\DoxyCodeLine{\Hypertarget{drv__i2c_8c_source_l00138}00138\ \textcolor{keywordtype}{int}\ i2c1\_WriteReg16Word32(uint16\_t\ addrSlave,\ uint16\_t\ \ regAddr,\ \ uint32\_t\ data)}
\DoxyCodeLine{\Hypertarget{drv__i2c_8c_source_l00139}00139\ \{}
\DoxyCodeLine{\Hypertarget{drv__i2c_8c_source_l00140}00140\ \ \ \ \ \textcolor{keywordtype}{int}\ status;}
\DoxyCodeLine{\Hypertarget{drv__i2c_8c_source_l00141}00141\ \ \ \ \ uint8\_t\ buffer[4];}
\DoxyCodeLine{\Hypertarget{drv__i2c_8c_source_l00142}00142\ \ \ \ \ buffer[0]=regAddr>>8;}
\DoxyCodeLine{\Hypertarget{drv__i2c_8c_source_l00143}00143\ \ \ \ \ buffer[1]=regAddr\&0xFF;}
\DoxyCodeLine{\Hypertarget{drv__i2c_8c_source_l00144}00144\ \ \ \ \ buffer[2]=data>>24;}
\DoxyCodeLine{\Hypertarget{drv__i2c_8c_source_l00145}00145\ \ \ \ \ buffer[3]=(data>>16)\&0xFF;}
\DoxyCodeLine{\Hypertarget{drv__i2c_8c_source_l00146}00146\ \ \ \ \ buffer[4]=(data>>8)\&0xFF;;}
\DoxyCodeLine{\Hypertarget{drv__i2c_8c_source_l00147}00147\ \ \ \ \ buffer[5]=data\&0xFF;}
\DoxyCodeLine{\Hypertarget{drv__i2c_8c_source_l00148}00148\ }
\DoxyCodeLine{\Hypertarget{drv__i2c_8c_source_l00149}00149\ \ \ \ \ status\ =\ HAL\_I2C\_Master\_Transmit(\&hi2c1,\ addrSlave,\ buffer,\ 6\ ,\ 100);}
\DoxyCodeLine{\Hypertarget{drv__i2c_8c_source_l00150}00150\ \ \ \ \ \textcolor{keywordflow}{return}\ status;}
\DoxyCodeLine{\Hypertarget{drv__i2c_8c_source_l00151}00151\ \}}
\DoxyCodeLine{\Hypertarget{drv__i2c_8c_source_l00152}00152\ \textcolor{comment}{//======================================================================}}
\DoxyCodeLine{\Hypertarget{drv__i2c_8c_source_l00153}00153\ \textcolor{comment}{//\ Read\ 1\ byte\ from\ regAddr\ (16\ bits)\ Slave}}
\DoxyCodeLine{\Hypertarget{drv__i2c_8c_source_l00154}00154\ \textcolor{comment}{//======================================================================}}
\DoxyCodeLine{\Hypertarget{drv__i2c_8c_source_l00155}00155\ \textcolor{keywordtype}{int}\ i2c1\_ReadReg16Byte(uint16\_t\ addrSlave,\ uint16\_t\ \ regAddr,\ uint8\_t\ *data)}
\DoxyCodeLine{\Hypertarget{drv__i2c_8c_source_l00156}00156\ \{}
\DoxyCodeLine{\Hypertarget{drv__i2c_8c_source_l00157}00157\ \ \ \ \ \textcolor{keywordtype}{int}\ status;}
\DoxyCodeLine{\Hypertarget{drv__i2c_8c_source_l00158}00158\ \ \ \ \ uint8\_t\ buffer[2];}
\DoxyCodeLine{\Hypertarget{drv__i2c_8c_source_l00159}00159\ }
\DoxyCodeLine{\Hypertarget{drv__i2c_8c_source_l00160}00160\ \ \ \ \ buffer[0]=regAddr>>8;}
\DoxyCodeLine{\Hypertarget{drv__i2c_8c_source_l00161}00161\ \ \ \ \ buffer[1]=regAddr\&0xFF;}
\DoxyCodeLine{\Hypertarget{drv__i2c_8c_source_l00162}00162\ }
\DoxyCodeLine{\Hypertarget{drv__i2c_8c_source_l00163}00163\ \ \ \ \ status=HAL\_I2C\_Master\_Transmit(\&hi2c1,\ addrSlave,\ buffer,\ 2,\ 100);}
\DoxyCodeLine{\Hypertarget{drv__i2c_8c_source_l00164}00164\ \ \ \ \ \ \textcolor{keywordflow}{if}(!status\ )\ \{}
\DoxyCodeLine{\Hypertarget{drv__i2c_8c_source_l00165}00165\ \ \ \ \ \ \ \ \ status\ =HAL\_I2C\_Master\_Receive(\&hi2c1,\ addrSlave,\ buffer,\ 1,\ 100);}
\DoxyCodeLine{\Hypertarget{drv__i2c_8c_source_l00166}00166\ \ \ \ \ \ \ \ \ \textcolor{keywordflow}{if}(\ !status\ )\{}
\DoxyCodeLine{\Hypertarget{drv__i2c_8c_source_l00167}00167\ \ \ \ \ \ \ \ \ \ \ \ \ *data=buffer[0];}
\DoxyCodeLine{\Hypertarget{drv__i2c_8c_source_l00168}00168\ \ \ \ \ \ \ \ \ \}}
\DoxyCodeLine{\Hypertarget{drv__i2c_8c_source_l00169}00169\ \ \ \ \ \ \}}
\DoxyCodeLine{\Hypertarget{drv__i2c_8c_source_l00170}00170\ }
\DoxyCodeLine{\Hypertarget{drv__i2c_8c_source_l00171}00171\ \ \ \ \ \textcolor{keywordflow}{return}\ status;}
\DoxyCodeLine{\Hypertarget{drv__i2c_8c_source_l00172}00172\ \}}
\DoxyCodeLine{\Hypertarget{drv__i2c_8c_source_l00173}00173\ \textcolor{comment}{//======================================================================}}
\DoxyCodeLine{\Hypertarget{drv__i2c_8c_source_l00174}00174\ \textcolor{comment}{//\ Read\ 16\ bits\ word\ from\ regAddr\ (16\ bits)\ Slave}}
\DoxyCodeLine{\Hypertarget{drv__i2c_8c_source_l00175}00175\ \textcolor{comment}{//======================================================================}}
\DoxyCodeLine{\Hypertarget{drv__i2c_8c_source_l00176}00176\ \textcolor{keywordtype}{int}\ i2c1\_ReadReg16Word16(uint16\_t\ addrSlave,\ uint16\_t\ \ regAddr,\ uint16\_t\ *data)}
\DoxyCodeLine{\Hypertarget{drv__i2c_8c_source_l00177}00177\ \{}
\DoxyCodeLine{\Hypertarget{drv__i2c_8c_source_l00178}00178\ \ \ \ \ \textcolor{keywordtype}{int}\ status;}
\DoxyCodeLine{\Hypertarget{drv__i2c_8c_source_l00179}00179\ \ \ \ \ uint8\_t\ buffer[2];}
\DoxyCodeLine{\Hypertarget{drv__i2c_8c_source_l00180}00180\ }
\DoxyCodeLine{\Hypertarget{drv__i2c_8c_source_l00181}00181\ \ \ \ \ buffer[0]=regAddr>>8;}
\DoxyCodeLine{\Hypertarget{drv__i2c_8c_source_l00182}00182\ \ \ \ \ buffer[1]=regAddr\&0xFF;}
\DoxyCodeLine{\Hypertarget{drv__i2c_8c_source_l00183}00183\ }
\DoxyCodeLine{\Hypertarget{drv__i2c_8c_source_l00184}00184\ \ \ \ \ status=HAL\_I2C\_Master\_Transmit(\&hi2c1,\ addrSlave,\ buffer,\ 2,\ 100);}
\DoxyCodeLine{\Hypertarget{drv__i2c_8c_source_l00185}00185\ \ \ \ \ \ \textcolor{keywordflow}{if}(!status\ )\ \{}
\DoxyCodeLine{\Hypertarget{drv__i2c_8c_source_l00186}00186\ \ \ \ \ \ \ \ \ status\ =HAL\_I2C\_Master\_Receive(\&hi2c1,\ addrSlave,\ buffer,\ 2,\ 100);}
\DoxyCodeLine{\Hypertarget{drv__i2c_8c_source_l00187}00187\ \ \ \ \ \ \ \ \ \textcolor{keywordflow}{if}(\ !status\ )\{}
\DoxyCodeLine{\Hypertarget{drv__i2c_8c_source_l00188}00188\ \ \ \ \ \ \ \ \ \ \ \ \ \ \ \textcolor{comment}{//VL6180x\ register\ are\ Big\ endian\ if\ cpu\ is\ be\ direct\ read\ direct\ into\ *data\ is\ possible}}
\DoxyCodeLine{\Hypertarget{drv__i2c_8c_source_l00189}00189\ \ \ \ \ \ \ \ \ \ \ \ \ \ *data=((uint16\_t)buffer[0]<<8)|(uint16\_t)buffer[1];}
\DoxyCodeLine{\Hypertarget{drv__i2c_8c_source_l00190}00190\ \ \ \ \ \ \ \ \ \}}
\DoxyCodeLine{\Hypertarget{drv__i2c_8c_source_l00191}00191\ \ \ \ \ \ \}}
\DoxyCodeLine{\Hypertarget{drv__i2c_8c_source_l00192}00192\ }
\DoxyCodeLine{\Hypertarget{drv__i2c_8c_source_l00193}00193\ \ \ \ \ \textcolor{keywordflow}{return}\ status;}
\DoxyCodeLine{\Hypertarget{drv__i2c_8c_source_l00194}00194\ \}}
\DoxyCodeLine{\Hypertarget{drv__i2c_8c_source_l00195}00195\ \textcolor{comment}{//======================================================================}}
\DoxyCodeLine{\Hypertarget{drv__i2c_8c_source_l00196}00196\ \textcolor{comment}{//\ Read\ 32\ bits\ word\ from\ regAddr\ (16\ bits)\ Slave}}
\DoxyCodeLine{\Hypertarget{drv__i2c_8c_source_l00197}00197\ \textcolor{comment}{//======================================================================}}
\DoxyCodeLine{\Hypertarget{drv__i2c_8c_source_l00198}00198\ \textcolor{keywordtype}{int}\ i2c1\_ReadReg16Word32(uint16\_t\ addrSlave,\ uint16\_t\ \ regAddr,\ uint32\_t\ *data)}
\DoxyCodeLine{\Hypertarget{drv__i2c_8c_source_l00199}00199\ \{}
\DoxyCodeLine{\Hypertarget{drv__i2c_8c_source_l00200}00200\ \ \ \ \ \textcolor{keywordtype}{int}\ status;}
\DoxyCodeLine{\Hypertarget{drv__i2c_8c_source_l00201}00201\ \ \ \ \ uint8\_t\ buffer[4];}
\DoxyCodeLine{\Hypertarget{drv__i2c_8c_source_l00202}00202\ }
\DoxyCodeLine{\Hypertarget{drv__i2c_8c_source_l00203}00203\ \ \ \ \ buffer[0]=regAddr>>8;}
\DoxyCodeLine{\Hypertarget{drv__i2c_8c_source_l00204}00204\ \ \ \ \ buffer[1]=regAddr\&0xFF;}
\DoxyCodeLine{\Hypertarget{drv__i2c_8c_source_l00205}00205\ }
\DoxyCodeLine{\Hypertarget{drv__i2c_8c_source_l00206}00206\ \ \ \ \ status=HAL\_I2C\_Master\_Transmit(\&hi2c1,\ addrSlave,\ buffer,\ 2,\ 100);}
\DoxyCodeLine{\Hypertarget{drv__i2c_8c_source_l00207}00207\ \ \ \ \ \ \textcolor{keywordflow}{if}(!status\ )\ \{}
\DoxyCodeLine{\Hypertarget{drv__i2c_8c_source_l00208}00208\ \ \ \ \ \ \ \ \ status\ =HAL\_I2C\_Master\_Receive(\&hi2c1,\ addrSlave,\ buffer,\ 4,\ 100);}
\DoxyCodeLine{\Hypertarget{drv__i2c_8c_source_l00209}00209\ \ \ \ \ \ \ \ \ \textcolor{keywordflow}{if}(\ !status\ )\{}
\DoxyCodeLine{\Hypertarget{drv__i2c_8c_source_l00210}00210\ \ \ \ \ \ \ \ \ \ \ \ \ \ \ \textcolor{comment}{//VL6180x\ register\ are\ Big\ endian\ if\ cpu\ is\ be\ direct\ read\ direct\ into\ *data\ is\ possible}}
\DoxyCodeLine{\Hypertarget{drv__i2c_8c_source_l00211}00211\ \ \ \ \ \ \ \ \ \ \ \ \ \ *data=((uint32\_t)buffer[0]<<24)|((uint32\_t)buffer[1]<<16)|((uint32\_t)buffer[2]<<8)|((uint32\_t)buffer[3]);}
\DoxyCodeLine{\Hypertarget{drv__i2c_8c_source_l00212}00212\ \ \ \ \ \ \ \ \ \}}
\DoxyCodeLine{\Hypertarget{drv__i2c_8c_source_l00213}00213\ \ \ \ \ \ \}}
\DoxyCodeLine{\Hypertarget{drv__i2c_8c_source_l00214}00214\ }
\DoxyCodeLine{\Hypertarget{drv__i2c_8c_source_l00215}00215\ \ \ \ \ \textcolor{keywordflow}{return}\ status;}
\DoxyCodeLine{\Hypertarget{drv__i2c_8c_source_l00216}00216\ \}}
\DoxyCodeLine{\Hypertarget{drv__i2c_8c_source_l00217}00217\ }
\DoxyCodeLine{\Hypertarget{drv__i2c_8c_source_l00218}00218\ \textcolor{comment}{//======================================================================}}
\DoxyCodeLine{\Hypertarget{drv__i2c_8c_source_l00219}00219\ \textcolor{comment}{//\ Read\ n\_data\ bytes\ from\ regAddr\ (16\ bits)\ Slave}}
\DoxyCodeLine{\Hypertarget{drv__i2c_8c_source_l00220}00220\ \textcolor{comment}{//======================================================================}}
\DoxyCodeLine{\Hypertarget{drv__i2c_8c_source_l00221}00221\ \textcolor{keywordtype}{int}\ i2c1\_ReadReg16Buffer(uint16\_t\ addrSlave,\ uint16\_t\ \ regAddr,\ \ uint8\_t\ *data,\ \textcolor{keywordtype}{int}\ n\_data)}
\DoxyCodeLine{\Hypertarget{drv__i2c_8c_source_l00222}00222\ \{}
\DoxyCodeLine{\Hypertarget{drv__i2c_8c_source_l00223}00223\ \ \ \ \ \textcolor{keywordtype}{int}\ status;}
\DoxyCodeLine{\Hypertarget{drv__i2c_8c_source_l00224}00224\ \ \ \ \ uint8\_t\ buffer[2];}
\DoxyCodeLine{\Hypertarget{drv__i2c_8c_source_l00225}00225\ }
\DoxyCodeLine{\Hypertarget{drv__i2c_8c_source_l00226}00226\ \ \ \ \ buffer[0]=regAddr>>8;}
\DoxyCodeLine{\Hypertarget{drv__i2c_8c_source_l00227}00227\ \ \ \ \ buffer[1]=regAddr\&0xFF;}
\DoxyCodeLine{\Hypertarget{drv__i2c_8c_source_l00228}00228\ }
\DoxyCodeLine{\Hypertarget{drv__i2c_8c_source_l00229}00229\ \ \ \ \ status=HAL\_I2C\_Master\_Transmit(\&hi2c1,\ addrSlave,\ buffer,\ 2,\ 100);}
\DoxyCodeLine{\Hypertarget{drv__i2c_8c_source_l00230}00230\ \ \ \ \ \textcolor{keywordflow}{if}(\ !status\ )\{}
\DoxyCodeLine{\Hypertarget{drv__i2c_8c_source_l00231}00231\ \ \ \ \ \ \ \ \ status=HAL\_I2C\_Master\_Receive(\&hi2c1,\ addrSlave,\ data,\ n\_data,\ n\_data*100);}
\DoxyCodeLine{\Hypertarget{drv__i2c_8c_source_l00232}00232\ \ \ \ \ \}}
\DoxyCodeLine{\Hypertarget{drv__i2c_8c_source_l00233}00233\ }
\DoxyCodeLine{\Hypertarget{drv__i2c_8c_source_l00234}00234\ }
\DoxyCodeLine{\Hypertarget{drv__i2c_8c_source_l00235}00235\ }
\DoxyCodeLine{\Hypertarget{drv__i2c_8c_source_l00236}00236\ \ \ \ \ \textcolor{keywordflow}{return}\ status;}
\DoxyCodeLine{\Hypertarget{drv__i2c_8c_source_l00237}00237\ \}}
\DoxyCodeLine{\Hypertarget{drv__i2c_8c_source_l00238}00238\ }
\DoxyCodeLine{\Hypertarget{drv__i2c_8c_source_l00239}00239\ }
\DoxyCodeLine{\Hypertarget{drv__i2c_8c_source_l00240}00240\ }
\DoxyCodeLine{\Hypertarget{drv__i2c_8c_source_l00241}00241\ }
\DoxyCodeLine{\Hypertarget{drv__i2c_8c_source_l00242}00242\ }

\end{DoxyCode}
