TitouanMelon/ENIB_Robot_Mobile_Ros2/docs/latex/retarget_8h.tex

\doxysection{C\+:/\+Users/\+Administrator/\+Documents/\+Git\+Hub/\+ENIB\+\_\+\+Robot\+\_\+\+Mobile\+\_\+\+Ros2/final\+Code/\+WORKSPACE\+\_\+\+F411\+\_\+u\+ROS/base\+\_\+robot/\+Core/\+Inc/retarget.h File Reference}
\hypertarget{retarget_8h}{}\label{retarget_8h}\index{C:/Users/Administrator/Documents/GitHub/ENIB\_Robot\_Mobile\_Ros2/finalCode/WORKSPACE\_F411\_uROS/base\_robot/Core/Inc/retarget.h@{C:/Users/Administrator/Documents/GitHub/ENIB\_Robot\_Mobile\_Ros2/finalCode/WORKSPACE\_F411\_uROS/base\_robot/Core/Inc/retarget.h}}

\+: Contain function to add printf and scanf function use the UART2 All credit to Carmine Noviello for this code \href{https://github.com/cnoviello/mastering-stm32/blob/master/nucleo-f030R8/system/src/retarget/}{\texttt{ https\+://github.\+com/cnoviello/mastering-\/stm32/blob/master/nucleo-\/f030\+R8/system/src/retarget/}}  

{\ttfamily \#include "{}stm32f4xx\+\_\+hal.\+h"{}}\newline
{\ttfamily \#include $<$sys/stat.\+h$>$}\newline
\doxysubsubsection*{Functions}
\begin{DoxyCompactItemize}
\item 
void \mbox{\hyperlink{retarget_8h_ac7028227e5051dfa3bb8fabb0edd07c8}{Retarget\+Init}} (UART\+\_\+\+Handle\+Type\+Def \texorpdfstring{$\ast$}{*}huart)
\item 
int \mbox{\hyperlink{retarget_8h_a4284676ccba12d7f2061d338001f71fb}{\+\_\+isatty}} (int fd)
\item 
int \mbox{\hyperlink{retarget_8h_a0c1fa2d02c07b22bf2ebd769a028b852}{\+\_\+write}} (int fd, char \texorpdfstring{$\ast$}{*}ptr, int len)
\item 
int \mbox{\hyperlink{retarget_8h_a58a559c63748012aab165d5f82af766d}{\+\_\+close}} (int fd)
\item 
int \mbox{\hyperlink{retarget_8h_a883d6c1f92ad3c6f19731e7b57b2c458}{\+\_\+lseek}} (int fd, int ptr, int dir)
\item 
int \mbox{\hyperlink{retarget_8h_ab60e5acd5530805f1421802fc0dc1d35}{\+\_\+read}} (int fd, char \texorpdfstring{$\ast$}{*}ptr, int len)
\item 
int \mbox{\hyperlink{retarget_8h_a6e8d95db883bc4efe10c487d74e96b06}{\+\_\+fstat}} (int fd, struct stat \texorpdfstring{$\ast$}{*}st)
\item 
int \mbox{\hyperlink{retarget_8h_a945e539df8e0f66d3c73c533fe1968ee}{\+\_\+getpid}} (void)
\item 
int \mbox{\hyperlink{retarget_8h_a062a5101199c3128edd5170f2575bb10}{\+\_\+kill}} (int pid, int sig)
\end{DoxyCompactItemize}

\doxysubsection{Detailed Description}
\+: Contain function to add printf and scanf function use the UART2 All credit to Carmine Noviello for this code \href{https://github.com/cnoviello/mastering-stm32/blob/master/nucleo-f030R8/system/src/retarget/}{\texttt{ https\+://github.\+com/cnoviello/mastering-\/stm32/blob/master/nucleo-\/f030\+R8/system/src/retarget/}} 

Definition in file \mbox{\hyperlink{retarget_8h_source}{retarget.\+h}}.

\doxysubsection{Macro Definition Documentation}
\Hypertarget{retarget_8h_aab2736c1de0d441e1707968caa495dc9}\label{retarget_8h_aab2736c1de0d441e1707968caa495dc9} 
\index{retarget.h@{retarget.h}!\_RETARGET\_H\_\_@{\_RETARGET\_H\_\_}}
\index{\_RETARGET\_H\_\_@{\_RETARGET\_H\_\_}!retarget.h@{retarget.h}}
\doxysubsubsection{\texorpdfstring{\_RETARGET\_H\_\_}{\_RETARGET\_H\_\_}}
{\footnotesize\ttfamily \#define \+\_\+\+RETARGET\+\_\+\+H\+\_\+\+\_\+}

Definition at line \mbox{\hyperlink{retarget_8h_source_l00012}{12}} of file \mbox{\hyperlink{retarget_8h_source}{retarget.\+h}}.

\doxysubsection{Function Documentation}
\Hypertarget{retarget_8h_a58a559c63748012aab165d5f82af766d}\label{retarget_8h_a58a559c63748012aab165d5f82af766d} 
\index{retarget.h@{retarget.h}!\_close@{\_close}}
\index{\_close@{\_close}!retarget.h@{retarget.h}}
\doxysubsubsection{\texorpdfstring{\_close()}{\_close()}}
{\footnotesize\ttfamily int \+\_\+close (\begin{DoxyParamCaption}\item[{int}]{fd }\end{DoxyParamCaption})}

Definition at line \mbox{\hyperlink{retarget_8c_source_l00057}{57}} of file \mbox{\hyperlink{retarget_8c_source}{retarget.\+c}}.

\Hypertarget{retarget_8h_a6e8d95db883bc4efe10c487d74e96b06}\label{retarget_8h_a6e8d95db883bc4efe10c487d74e96b06} 
\index{retarget.h@{retarget.h}!\_fstat@{\_fstat}}
\index{\_fstat@{\_fstat}!retarget.h@{retarget.h}}
\doxysubsubsection{\texorpdfstring{\_fstat()}{\_fstat()}}
{\footnotesize\ttfamily int \+\_\+fstat (\begin{DoxyParamCaption}\item[{int}]{fd,  }\item[{struct stat \texorpdfstring{$\ast$}{*}}]{st }\end{DoxyParamCaption})}

Definition at line \mbox{\hyperlink{retarget_8c_source_l00088}{88}} of file \mbox{\hyperlink{retarget_8c_source}{retarget.\+c}}.

\Hypertarget{retarget_8h_a945e539df8e0f66d3c73c533fe1968ee}\label{retarget_8h_a945e539df8e0f66d3c73c533fe1968ee} 
\index{retarget.h@{retarget.h}!\_getpid@{\_getpid}}
\index{\_getpid@{\_getpid}!retarget.h@{retarget.h}}
\doxysubsubsection{\texorpdfstring{\_getpid()}{\_getpid()}}
{\footnotesize\ttfamily int \+\_\+getpid (\begin{DoxyParamCaption}\item[{void}]{ }\end{DoxyParamCaption})}

Definition at line \mbox{\hyperlink{retarget_8c_source_l00098}{98}} of file \mbox{\hyperlink{retarget_8c_source}{retarget.\+c}}.

\Hypertarget{retarget_8h_a4284676ccba12d7f2061d338001f71fb}\label{retarget_8h_a4284676ccba12d7f2061d338001f71fb} 
\index{retarget.h@{retarget.h}!\_isatty@{\_isatty}}
\index{\_isatty@{\_isatty}!retarget.h@{retarget.h}}
\doxysubsubsection{\texorpdfstring{\_isatty()}{\_isatty()}}
{\footnotesize\ttfamily int \+\_\+isatty (\begin{DoxyParamCaption}\item[{int}]{fd }\end{DoxyParamCaption})}

Definition at line \mbox{\hyperlink{retarget_8c_source_l00035}{35}} of file \mbox{\hyperlink{retarget_8c_source}{retarget.\+c}}.

\Hypertarget{retarget_8h_a062a5101199c3128edd5170f2575bb10}\label{retarget_8h_a062a5101199c3128edd5170f2575bb10} 
\index{retarget.h@{retarget.h}!\_kill@{\_kill}}
\index{\_kill@{\_kill}!retarget.h@{retarget.h}}
\doxysubsubsection{\texorpdfstring{\_kill()}{\_kill()}}
{\footnotesize\ttfamily int \+\_\+kill (\begin{DoxyParamCaption}\item[{int}]{pid,  }\item[{int}]{sig }\end{DoxyParamCaption})}

Definition at line \mbox{\hyperlink{retarget_8c_source_l00103}{103}} of file \mbox{\hyperlink{retarget_8c_source}{retarget.\+c}}.

\Hypertarget{retarget_8h_a883d6c1f92ad3c6f19731e7b57b2c458}\label{retarget_8h_a883d6c1f92ad3c6f19731e7b57b2c458} 
\index{retarget.h@{retarget.h}!\_lseek@{\_lseek}}
\index{\_lseek@{\_lseek}!retarget.h@{retarget.h}}
\doxysubsubsection{\texorpdfstring{\_lseek()}{\_lseek()}}
{\footnotesize\ttfamily int \+\_\+lseek (\begin{DoxyParamCaption}\item[{int}]{fd,  }\item[{int}]{ptr,  }\item[{int}]{dir }\end{DoxyParamCaption})}

Definition at line \mbox{\hyperlink{retarget_8c_source_l00065}{65}} of file \mbox{\hyperlink{retarget_8c_source}{retarget.\+c}}.

\Hypertarget{retarget_8h_ab60e5acd5530805f1421802fc0dc1d35}\label{retarget_8h_ab60e5acd5530805f1421802fc0dc1d35} 
\index{retarget.h@{retarget.h}!\_read@{\_read}}
\index{\_read@{\_read}!retarget.h@{retarget.h}}
\doxysubsubsection{\texorpdfstring{\_read()}{\_read()}}
{\footnotesize\ttfamily int \+\_\+read (\begin{DoxyParamCaption}\item[{int}]{fd,  }\item[{char \texorpdfstring{$\ast$}{*}}]{ptr,  }\item[{int}]{len }\end{DoxyParamCaption})}

Definition at line \mbox{\hyperlink{retarget_8c_source_l00074}{74}} of file \mbox{\hyperlink{retarget_8c_source}{retarget.\+c}}.

\Hypertarget{retarget_8h_a0c1fa2d02c07b22bf2ebd769a028b852}\label{retarget_8h_a0c1fa2d02c07b22bf2ebd769a028b852} 
\index{retarget.h@{retarget.h}!\_write@{\_write}}
\index{\_write@{\_write}!retarget.h@{retarget.h}}
\doxysubsubsection{\texorpdfstring{\_write()}{\_write()}}
{\footnotesize\ttfamily int \+\_\+write (\begin{DoxyParamCaption}\item[{int}]{fd,  }\item[{char \texorpdfstring{$\ast$}{*}}]{ptr,  }\item[{int}]{len }\end{DoxyParamCaption})}

Definition at line \mbox{\hyperlink{retarget_8c_source_l00043}{43}} of file \mbox{\hyperlink{retarget_8c_source}{retarget.\+c}}.

\Hypertarget{retarget_8h_ac7028227e5051dfa3bb8fabb0edd07c8}\label{retarget_8h_ac7028227e5051dfa3bb8fabb0edd07c8} 
\index{retarget.h@{retarget.h}!RetargetInit@{RetargetInit}}
\index{RetargetInit@{RetargetInit}!retarget.h@{retarget.h}}
\doxysubsubsection{\texorpdfstring{RetargetInit()}{RetargetInit()}}
{\footnotesize\ttfamily void Retarget\+Init (\begin{DoxyParamCaption}\item[{UART\+\_\+\+Handle\+Type\+Def \texorpdfstring{$\ast$}{*}}]{huart }\end{DoxyParamCaption})}

Reconfigure stdin, stdout and stderr to use UART 
\begin{DoxyParams}{Parameters}
{\em huart} & Structure wich represent an UART \\
\hline
\end{DoxyParams}

Definition at line \mbox{\hyperlink{retarget_8c_source_l00027}{27}} of file \mbox{\hyperlink{retarget_8c_source}{retarget.\+c}}.
