TitouanMelon/ENIB_Robot_Mobile_Ros2/docs/latex/sysmem_8c.tex

\doxysection{C\+:/\+Users/\+Administrator/\+Documents/\+Git\+Hub/\+ENIB\+\_\+\+Robot\+\_\+\+Mobile\+\_\+\+Ros2/final\+Code/\+WORKSPACE\+\_\+\+F411\+\_\+u\+ROS/base\+\_\+robot/\+Core/\+Src/sysmem.c File Reference}
\hypertarget{sysmem_8c}{}\label{sysmem_8c}\index{C:/Users/Administrator/Documents/GitHub/ENIB\_Robot\_Mobile\_Ros2/finalCode/WORKSPACE\_F411\_uROS/base\_robot/Core/Src/sysmem.c@{C:/Users/Administrator/Documents/GitHub/ENIB\_Robot\_Mobile\_Ros2/finalCode/WORKSPACE\_F411\_uROS/base\_robot/Core/Src/sysmem.c}}

STM32\+Cube\+IDE System Memory calls file.  

{\ttfamily \#include $<$errno.\+h$>$}\newline
{\ttfamily \#include $<$stdint.\+h$>$}\newline
\doxysubsubsection*{Functions}
\begin{DoxyCompactItemize}
\item 
void \texorpdfstring{$\ast$}{*} \mbox{\hyperlink{sysmem_8c_a68125648bcce70b6bb3aa0be50e99700}{\+\_\+sbrk}} (ptrdiff\+\_\+t incr)
\begin{DoxyCompactList}\small\item\em \doxylink{sysmem_8c_a68125648bcce70b6bb3aa0be50e99700}{\+\_\+sbrk()} allocates memory to the newlib heap and is used by malloc and others from the C library \end{DoxyCompactList}\end{DoxyCompactItemize}
\doxysubsubsection*{Variables}
\begin{DoxyCompactItemize}
\item 
static uint8\+\_\+t \texorpdfstring{$\ast$}{*} \mbox{\hyperlink{sysmem_8c_a2cf862d604e9c7cfcf0528a0f539a6a5}{\+\_\+\+\_\+sbrk\+\_\+heap\+\_\+end}} = NULL
\end{DoxyCompactItemize}

\doxysubsection{Detailed Description}
STM32\+Cube\+IDE System Memory calls file. 

\begin{DoxyAuthor}{Author}
Generated by STM32\+Cube\+IDE \begin{DoxyVerb}       For more information about which C functions
       need which of these lowlevel functions
       please consult the newlib libc manual
\end{DoxyVerb}
 
\end{DoxyAuthor}
\begin{DoxyAttention}{Attention}

\end{DoxyAttention}
Copyright (c) 2022 STMicroelectronics. All rights reserved.

This software is licensed under terms that can be found in the LICENSE file in the root directory of this software component. If no LICENSE file comes with this software, it is provided AS-\/\+IS. 

Definition in file \mbox{\hyperlink{sysmem_8c_source}{sysmem.\+c}}.

\doxysubsection{Function Documentation}
\Hypertarget{sysmem_8c_a68125648bcce70b6bb3aa0be50e99700}\label{sysmem_8c_a68125648bcce70b6bb3aa0be50e99700} 
\index{sysmem.c@{sysmem.c}!\_sbrk@{\_sbrk}}
\index{\_sbrk@{\_sbrk}!sysmem.c@{sysmem.c}}
\doxysubsubsection{\texorpdfstring{\_sbrk()}{\_sbrk()}}
{\footnotesize\ttfamily void \texorpdfstring{$\ast$}{*} \+\_\+sbrk (\begin{DoxyParamCaption}\item[{ptrdiff\+\_\+t}]{incr }\end{DoxyParamCaption})}

\doxylink{sysmem_8c_a68125648bcce70b6bb3aa0be50e99700}{\+\_\+sbrk()} allocates memory to the newlib heap and is used by malloc and others from the C library 

\begin{DoxyVerb}* ############################################################################
* #  .data  #  .bss  #       newlib heap       #          MSP stack          #
* #         #        #                         # Reserved by _Min_Stack_Size #
* ############################################################################
* ^-- RAM start      ^-- _end                             _estack, RAM end --^
* \end{DoxyVerb}

This implementation starts allocating at the \textquotesingle{}\+\_\+end\textquotesingle{} linker symbol The \textquotesingle{}\+\_\+\+Min\+\_\+\+Stack\+\_\+\+Size\textquotesingle{} linker symbol reserves a memory for the MSP stack The implementation considers \textquotesingle{}\+\_\+estack\textquotesingle{} linker symbol to be RAM end NOTE\+: If the MSP stack, at any point during execution, grows larger than the reserved size, please increase the \textquotesingle{}\+\_\+\+Min\+\_\+\+Stack\+\_\+\+Size\textquotesingle{}.

\begin{DoxyParams}{Parameters}
{\em incr} & Memory size \\
\hline
\end{DoxyParams}
\begin{DoxyReturn}{Returns}
Pointer to allocated memory 
\end{DoxyReturn}

Definition at line \mbox{\hyperlink{sysmem_8c_source_l00053}{53}} of file \mbox{\hyperlink{sysmem_8c_source}{sysmem.\+c}}.

\doxysubsection{Variable Documentation}
\Hypertarget{sysmem_8c_a2cf862d604e9c7cfcf0528a0f539a6a5}\label{sysmem_8c_a2cf862d604e9c7cfcf0528a0f539a6a5} 
\index{sysmem.c@{sysmem.c}!\_\_sbrk\_heap\_end@{\_\_sbrk\_heap\_end}}
\index{\_\_sbrk\_heap\_end@{\_\_sbrk\_heap\_end}!sysmem.c@{sysmem.c}}
\doxysubsubsection{\texorpdfstring{\_\_sbrk\_heap\_end}{\_\_sbrk\_heap\_end}}
{\footnotesize\ttfamily uint8\+\_\+t\texorpdfstring{$\ast$}{*} \+\_\+\+\_\+sbrk\+\_\+heap\+\_\+end = NULL\hspace{0.3cm}{\ttfamily [static]}}

Pointer to the current high watermark of the heap usage 

Definition at line \mbox{\hyperlink{sysmem_8c_source_l00030}{30}} of file \mbox{\hyperlink{sysmem_8c_source}{sysmem.\+c}}.
