TitouanMelon/ENIB_Robot_Mobile_Ros2/finalCode/Camera/image.png

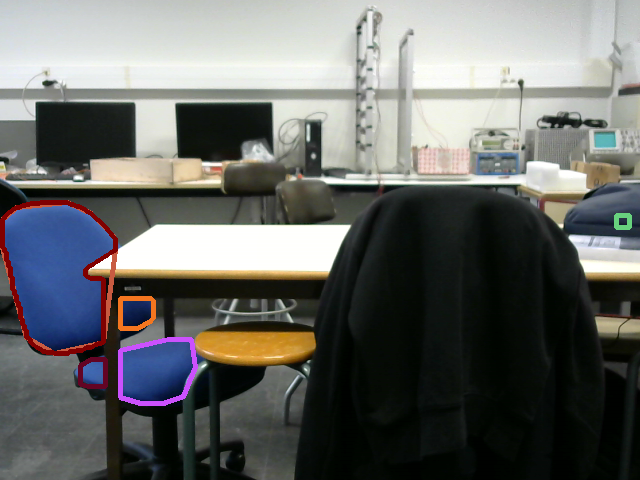
finalCode/Camera/image.png
