TitouanMelon/ENIB_Robot_Mobile_Ros2/finalCode/WORKSPACE_F411_uROS/base_robot/Core/Src/VL53L0X.c

/**
 * @file : VL53L0X.c
 * @brief : VL53L0X API STSW-IMG005 portage
 * Most of the functionality of this library is based on the VL53L0X API
 * provided by ST (STSW-IMG005), and some of the explanatory comments are quoted
 * or paraphrased from the API source code, API user manual (UM2039), and the
 * VL53L0X datasheet.
 */

//"${workspace_loc:/${ProjName}/Drivers/vl53l0x}" into include path of c++ buider properties

#include "main.h"
#include <unistd.h>

#include <stdint.h>
#include "VL53L0X.h"
#include "drv_i2c.h"

//---------------------------------------------------------
// Local variables within this file (private)
//---------------------------------------------------------
uint8_t g_i2cAddr = ADDRESS;
uint8_t g_stopVariable; // read by init and used when starting measurement; is StopVariable field of VL53L0X_DevData_t structure in API

uint16_t addr_read = 0;

//---------------------------------------------------------
// Locally used functions (private)
//---------------------------------------------------------
uint8_t performSingleRefCalibration(uint8_t vhv_init_byte);
//---------------------------------------------------------
// I2C communication Functions
//---------------------------------------------------------
// Write an 8-bit register
void writeReg(uint8_t reg, uint8_t value) {
	i2c1_WriteRegBuffer(g_i2cAddr,reg,&value,1);
}

// Write a 16-bit register
void writeReg16Bit(uint8_t reg, uint16_t value){
	uint8_t tab[2];
	tab[0]= ((value >> 8));
	tab[1] = ((value ) & 0xFF);
	i2c1_WriteRegBuffer(g_i2cAddr,reg,tab,2);
}

// Write a 32-bit register
void writeReg32Bit(uint8_t reg, uint32_t value){
	uint8_t tab[4];
		tab[3]= ((value >> 24) & 0xFF);
		tab[2]= ((value >> 16) & 0xFF);
		tab[1]= ((value >> 8) & 0xFF);
		tab[0] = ((value ) & 0xFF);
		i2c1_WriteRegBuffer(g_i2cAddr,reg,tab,4);
}

// Read an 8-bit register
uint8_t readReg(uint8_t reg) {
  	uint8_t value=0;
  	i2c1_WriteBuffer(g_i2cAddr, &reg, 1);
	i2c1_ReadBuffer(g_i2cAddr|0x01, &value, 1);
  	return value;
}

// Read a 16-bit register
uint16_t readReg16Bit(uint8_t reg) {
	uint8_t tab[2];
	i2c1_WriteBuffer(g_i2cAddr, &reg, 1);
	i2c1_ReadBuffer(g_i2cAddr|0x01, tab, 2);
  	uint16_t value= ((uint16_t)tab[0] << 8) | (uint16_t)tab[1];
  	return value;
}

// Read a 32-bit register
uint32_t readReg32Bit(uint8_t reg) {
  uint8_t tab[4];
  i2c1_WriteBuffer(g_i2cAddr, &reg, 1);
  i2c1_ReadBuffer(g_i2cAddr|0x01, tab, 4);
  uint32_t value= (tab[3] << 24) | (tab[2] << 16 ) | (tab[1] << 8) | tab[0];
  return value;
}

// Write an arbitrary number of bytes from the given array to the sensor,
// starting at the given register
void writeMulti(uint8_t reg, uint8_t const *src, uint8_t count){
  while ( count-- > 0 ) {
    i2c1_WriteRegBuffer(g_i2cAddr,reg,(uint8_t *)src,1);
  }
}



// Public Methods //////////////////////////////////////////////////////////////
void setAddress(uint8_t new_addr) {
  writeReg( I2C_SLAVE_DEVICE_ADDRESS, (new_addr>>1) & 0x7F );
  g_i2cAddr = new_addr;
}

uint8_t getAddress() {
  return g_i2cAddr;
}

// Initialize sensor using sequence based on VL53L0X_DataInit(),
// VL53L0X_StaticInit(), and VL53L0X_PerformRefCalibration().
// This function does not perform reference SPAD calibration
// (VL53L0X_PerformRefSpadManagement()), since the API user manual says that it
// is performed by ST on the bare modules; it seems like that should work well
// enough unless a cover glass is added.
// If io_2v8 (optional) is true or not given, the sensor is configured for 2V8
// mode.
uint8_t initVL53L0X( ){
  // VL53L0X_DataInit() begin


  // sensor uses 1V8 mode for I/O by default; switch to 2V8 mode if necessary
  if (IO_2V8)
  {
    writeReg(VHV_CONFIG_PAD_SCL_SDA__EXTSUP_HV,
    readReg(VHV_CONFIG_PAD_SCL_SDA__EXTSUP_HV) | 0x01); // set bit 0
  }

  // "Set I2C standard mode"
  writeReg(0x88, 0x00);

  writeReg(0x80, 0x01);
  writeReg(0xFF, 0x01);
  writeReg(0x00, 0x00);
  g_stopVariable = readReg(0x91);
  writeReg(0x00, 0x01);
  writeReg(0xFF, 0x00);
  writeReg(0x80, 0x00);

  // disable SIGNAL_RATE_MSRC (bit 1) and SIGNAL_RATE_PRE_RANGE (bit 4) limit checks
  writeReg(MSRC_CONFIG_CONTROL, readReg(MSRC_CONFIG_CONTROL) | 0x12);

  // set final range signal rate limit to 0.25 MCPS (million counts per second)
  setSignalRateLimit(0.25);

  writeReg(SYSTEM_SEQUENCE_CONFIG, 0xFF);

  // VL53L0X_DataInit() end

  // VL53L0X_StaticInit() begin

  // The SPAD map (RefGoodSpadMap) is read by VL53L0X_get_info_from_device() in
  // the API, but the same data seems to be more easily readable from
  // GLOBAL_CONFIG_SPAD_ENABLES_REF_0 through _6, so read it from there

  // -- VL53L0X_set_reference_spads() begin (assume NVM values are valid)

  writeReg(0xFF, 0x01);
  writeReg(DYNAMIC_SPAD_REF_EN_START_OFFSET, 0x00);
  writeReg(DYNAMIC_SPAD_NUM_REQUESTED_REF_SPAD, 0x2C);
  writeReg(0xFF, 0x00);
  writeReg(GLOBAL_CONFIG_REF_EN_START_SELECT, 0xB4);


  // -- VL53L0X_set_reference_spads() end

  // -- VL53L0X_load_tuning_settings() begin
  // DefaultTuningSettings from vl53l0x_tuning.h

  writeReg(0xFF, 0x01);
  writeReg(0x00, 0x00);

  writeReg(0xFF, 0x00);
  writeReg(0x09, 0x00);
  writeReg(0x10, 0x00);
  writeReg(0x11, 0x00);

  writeReg(0x24, 0x01);
  writeReg(0x25, 0xFF);
  writeReg(0x75, 0x00);

  writeReg(0xFF, 0x01);
  writeReg(0x4E, 0x2C);
  writeReg(0x48, 0x00);
  writeReg(0x30, 0x20);

  writeReg(0xFF, 0x00);
  writeReg(0x30, 0x09);
  writeReg(0x54, 0x00);
  writeReg(0x31, 0x04);
  writeReg(0x32, 0x03);
  writeReg(0x40, 0x83);
  writeReg(0x46, 0x25);
  writeReg(0x60, 0x00);
  writeReg(0x27, 0x00);
  writeReg(0x50, 0x06);
  writeReg(0x51, 0x00);
  writeReg(0x52, 0x96);
  writeReg(0x56, 0x08);
  writeReg(0x57, 0x30);
  writeReg(0x61, 0x00);
  writeReg(0x62, 0x00);
  writeReg(0x64, 0x00);
  writeReg(0x65, 0x00);
  writeReg(0x66, 0xA0);

  writeReg(0xFF, 0x01);
  writeReg(0x22, 0x32);
  writeReg(0x47, 0x14);
  writeReg(0x49, 0xFF);
  writeReg(0x4A, 0x00);

  writeReg(0xFF, 0x00);
  writeReg(0x7A, 0x0A);
  writeReg(0x7B, 0x00);
  writeReg(0x78, 0x21);

  writeReg(0xFF, 0x01);
  writeReg(0x23, 0x34);
  writeReg(0x42, 0x00);
  writeReg(0x44, 0xFF);
  writeReg(0x45, 0x26);
  writeReg(0x46, 0x05);
  writeReg(0x40, 0x40);
  writeReg(0x0E, 0x06);
  writeReg(0x20, 0x1A);
  writeReg(0x43, 0x40);

  writeReg(0xFF, 0x00);
  writeReg(0x34, 0x03);
  writeReg(0x35, 0x44);

  writeReg(0xFF, 0x01);
  writeReg(0x31, 0x04);
  writeReg(0x4B, 0x09);
  writeReg(0x4C, 0x05);
  writeReg(0x4D, 0x04);

  writeReg(0xFF, 0x00);
  writeReg(0x44, 0x00);
  writeReg(0x45, 0x20);
  writeReg(0x47, 0x08);
  writeReg(0x48, 0x28);
  writeReg(0x67, 0x00);
  writeReg(0x70, 0x04);
  writeReg(0x71, 0x01);
  writeReg(0x72, 0xFE);
  writeReg(0x76, 0x00);
  writeReg(0x77, 0x00);

  writeReg(0xFF, 0x01);
  writeReg(0x0D, 0x01);

  writeReg(0xFF, 0x00);
  writeReg(0x80, 0x01);
  writeReg(0x01, 0xF8);

  writeReg(0xFF, 0x01);
  writeReg(0x8E, 0x01);
  writeReg(0x00, 0x01);
  writeReg(0xFF, 0x00);
  writeReg(0x80, 0x00);

  // -- VL53L0X_load_tuning_settings() end

  // "Set interrupt config to new sample ready"
  // -- VL53L0X_SetGpioConfig() begin

  writeReg(SYSTEM_INTERRUPT_CONFIG_GPIO, 0x04);
  writeReg(GPIO_HV_MUX_ACTIVE_HIGH, readReg(GPIO_HV_MUX_ACTIVE_HIGH) & ~0x10); // active low
  writeReg(SYSTEM_INTERRUPT_CLEAR, 0x01);

  // -- VL53L0X_SetGpioConfig() end



  // "Disable MSRC and TCC by default"
  // MSRC = Minimum Signal Rate Check
  // TCC = Target CentreCheck
  // -- VL53L0X_SetSequenceStepEnable() begin

  writeReg(SYSTEM_SEQUENCE_CONFIG, 0xE8);

  // -- VL53L0X_SetSequenceStepEnable() end



  // VL53L0X_StaticInit() end

  // VL53L0X_PerformRefCalibration() begin (VL53L0X_perform_ref_calibration())

  // -- VL53L0X_perform_vhv_calibration() begin

  writeReg(SYSTEM_SEQUENCE_CONFIG, 0x01);
  if (performSingleRefCalibration(0x40)) { return 1; }

  // -- VL53L0X_perform_vhv_calibration() end

  // -- VL53L0X_perform_phase_calibration() begin

  writeReg(SYSTEM_SEQUENCE_CONFIG, 0x02);
  if (performSingleRefCalibration(0x00)) { return 1; }

  // -- VL53L0X_perform_phase_calibration() end

  // "restore the previous Sequence Config"
  writeReg(SYSTEM_SEQUENCE_CONFIG, 0xE8);

  // VL53L0X_PerformRefCalibration() end

  return 0;
}

// Set the return signal rate limit check value in units of MCPS (mega counts
// per second). "This represents the amplitude of the signal reflected from the
// target and detected by the device"; setting this limit presumably determines
// the minimum measurement necessary for the sensor to report a valid reading.
// Setting a lower limit increases the potential range of the sensor but also
// seems to increase the likelihood of getting an inaccurate reading because of
// unwanted reflections from objects other than the intended target.
// Defaults to 0.25 MCPS as initialized by the ST API and this library.
uint8_t setSignalRateLimit(float limit_Mcps)
{
  if (limit_Mcps < 0 || limit_Mcps > 511.99) { return false; }

  // Q9.7 fixed point format (9 integer bits, 7 fractional bits)
  writeReg16Bit(FINAL_RANGE_CONFIG_MIN_COUNT_RATE_RTN_LIMIT, limit_Mcps * (1 << 7));
  return 0;
}

// Get the return signal rate limit check value in MCPS
float getSignalRateLimit(void)
{
  return (float)readReg16Bit(FINAL_RANGE_CONFIG_MIN_COUNT_RATE_RTN_LIMIT) / (1 << 7);
}





// Performs a single-shot range measurement and returns the reading in
// millimeters
// based on VL53L0X_PerformSingleRangingMeasurement()
// extraStats provides additional info for this measurment. Set to 0 if not needed.
uint16_t readRangeSingleMillimeters( /*statInfo_t *extraStats */) {
  writeReg(0x80, 0x01);
  writeReg(0xFF, 0x01);
  writeReg(0x00, 0x00);
  writeReg(0x91, g_stopVariable);
  writeReg(0x00, 0x01);
  writeReg(0xFF, 0x00);
  writeReg(0x80, 0x00);
  writeReg(SYSRANGE_START, 0x01);

  uint16_t temp;

  if (ACTIVE_WHILE)
  {
	  while (readReg(SYSRANGE_START) & 0x01){};
	  while ((readReg(RESULT_INTERRUPT_STATUS) & 0x07) == 0){};
  }
  // assumptions: Linearity Corrective Gain is 1000 (default);
  // fractional ranging is not enabled
  temp = readReg16Bit(RESULT_RANGE_STATUS + 10);
  temp+=0;

  return temp;
}


// based on VL53L0X_perform_single_ref_calibration()
uint8_t performSingleRefCalibration(uint8_t vhv_init_byte)
{
  writeReg(SYSRANGE_START, 0x01 | vhv_init_byte); // VL53L0X_REG_SYSRANGE_MODE_START_STOP

  if (ACTIVE_WHILE)
	  while ((readReg(RESULT_INTERRUPT_STATUS) & 0x07) == 0){};

  writeReg(SYSTEM_INTERRUPT_CLEAR, 0x01);

  writeReg(SYSRANGE_START, 0x00);

  return 0;
}
